austinscip/table-wars-puck/docs/hardware/PCB_REVIEW.md

# TABLE WARS PCB Design Review

**Date:** December 15, 2025
**Freelancer's Deliverables:** Hardware.rar (17.4 MB), PCB screenshots

---

## ✅ Overall Assessment: **GOOD JOB**

The freelancer delivered a professional, well-thought-out PCB design. Here's my detailed review:

---

## 🎯 What They Got Right

### 1. **Form Factor** ⭐⭐⭐⭐⭐
- ✅ **Circular PCB** - Perfect for a puck! Smart choice.
- ✅ **Compact design** - All components fit nicely in the circle
- ✅ **Professional layout** - Clean routing, good component placement

### 2. **Component Selection** ⭐⭐⭐⭐⭐

**Power Management:**
- ✅ **TP4057** - LiPo battery charging IC (better than TP4056)
- ✅ **MT3608** - Step-up DC-DC converter (boosts 3.7V to 5V if needed)
- ✅ **AO3407A** - P-channel MOSFET for power switching

**Main Components:**
- ✅ **ESP32-DEVKITC** - Your main microcontroller (WiFi + BLE)
- ✅ **WS2812B2020** - Addressable RGB LEDs (the LED ring!)

All components are industry-standard, readily available, and appropriate for this application.

### 3. **Power Circuit** ⭐⭐⭐⭐⭐
- ✅ USB-C connector for charging (modern, convenient)
- ✅ Battery charging circuit (TP4057)
- ✅ Voltage regulation (MT3608 boost converter)
- ✅ Power switching (MOSFET for on/off control)

This is a **complete power solution**:
- Charge via USB-C
- Run from battery
- Auto power management

### 4. **Connectivity** ⭐⭐⭐⭐⭐
- ✅ USB-C port positioned at top (easy access)
- ✅ ISP/Programming header visible (for flashing firmware)
- ✅ Test points for debugging

### 5. **Manufacturing Readiness** ⭐⭐⭐⭐
- ✅ Altium Designer files (professional PCB design software)
- ✅ Component libraries included
- ✅ Version history saved (shows iterative design process)
- ⚠️ **Missing:** Gerber files, BOM (Bill of Materials), assembly drawings

---

## 📋 What I Can See From PCB Layout

**Front/Top Side:**
1. **ESP32 module** - Center position (good for WiFi antenna)
2. **USB-C connector** - Top edge (accessible)
3. **Voltage regulators** (U1, U3) - Near power input
4. **LED driver circuit** - Components for WS2812B control
5. **Support components** - Resistors, capacitors, diodes properly placed
6. **Programming header** (IST-PHL) - For firmware updates
7. **Speaker/Buzzer** (LS1) - Audio feedback
8. **Transistors** (Q1, Q2) - Likely for motor/LED control

**Component Density:**
- ✅ Good spacing - Not too cramped
- ✅ Logical grouping - Related components near each other
- ✅ Thermal considerations - Power components separated

---

## ⚠️ What's Missing or Unclear

### 1. **Manufacturing Files** ⚠️
**Missing:**
- Gerber files (.gbr) - Needed for PCB fabrication
- Drill files (.drl) - For drilling holes
- Bill of Materials (BOM.csv) - Parts list for assembly
- Pick-and-place file (.pos) - For automated assembly
- Assembly drawings - Visual guide for hand assembly

**Impact:** You'll need to ask the freelancer to export these from Altium.

### 2. **Sensors** ❓
**Question:** Where's the MPU6050 (motion sensor)?
- Your firmware has shake detection code
- I don't clearly see an IMU/accelerometer on the PCB
- Might be on the schematic but not visible in these views

**Action:** Ask freelancer if MPU6050 is included.

### 3. **Button** ❓
**Question:** Where's the physical button?
- Your code expects a button (PIN 27)
- Don't see an obvious tactile switch
- Might be labeled differently

### 4. **Vibration Motor Connection** ❓
- Code has motor control
- Need to verify connector is included

### 5. **LED Ring Specs** ❓
**Need to confirm:**
- How many WS2812B LEDs? (Code expects 16)
- Are they on a separate ring PCB?
- Connection method to main board?

---

## 🔍 Component Analysis

### Identified Components:

| Component | Part | Purpose | Assessment |
|---|---|---|---|
| U2 | ESP32-DEVKITC | Main microcontroller | ✅ Perfect |
| U1, U3 | Voltage regulators | Power management | ✅ Good |
| TP4057 | Battery charger | LiPo charging | ✅ Excellent choice |
| MT3608 | DC-DC boost | Voltage boost | ✅ Good |
| AO3407A | P-MOSFET | Power switching | ✅ Solid |
| WS2812B2020 | RGB LED | Addressable LEDs | ✅ Standard choice |
| LS1 | Speaker/Buzzer | Audio | ✅ Present |
| R1-R13 | Resistors | Various | ✅ Properly sized |
| C1, C2, C4 | Capacitors | Filtering/decoupling | ✅ Good placement |
| Q1, Q2 | Transistors | Switching | ✅ Good for motor control |
| D1, D2 | Diodes | Protection/rectification | ✅ Necessary |

---

## 💰 Estimated Cost Per PCB

**PCB Fabrication** (from JLCPCB/PCBWay):
- Qty 10: ~$2-5 per board
- Qty 100: ~$1-2 per board

**Components** (per puck, if buying in bulk):
- ESP32-DEVKITC: $6-8
- TP4057 charging IC: $0.50
- MT3608 boost converter: $0.50
- WS2812B LEDs (16x): $3-5
- MOSFETs, resistors, caps: $2-3
- LiPo battery (500mAh): $5-8
- Buzzer: $0.50
- Misc connectors: $1-2

**Total per assembled puck:** ~$22-35

---

## 📊 Quality Rating

| Category | Rating | Notes |
|---|---|---|
| **Design Quality** | 9/10 | Professional, clean layout |
| **Component Selection** | 9/10 | Good modern parts |
| **Power Management** | 10/10 | Complete, well-designed |
| **Manufacturability** | 7/10 | Need Gerbers + BOM |
| **Documentation** | 6/10 | Source files only, no exports |
| **Completeness** | 7/10 | Main PCB done, unclear on sensors |

**Overall Score: 8/10** - Solid work, needs manufacturing files

---

## ✅ Action Items

### **Ask Freelancer to Provide:**

1. **Gerber files** - For PCB manufacturing
2. **Bill of Materials (BOM)** - Excel/CSV with:
   - Part numbers
   - Quantities
   - Manufacturer/supplier
   - Reference designators
3. **Assembly drawings** - PDF showing component placement
4. **Pick-and-place file** - For automated assembly (optional)
5. **Schematic PDF** - Human-readable schematic
6. **Design notes** - Any special assembly instructions

### **Questions to Ask Freelancer:**

1. Is the MPU6050 (motion sensor) included? Where?
2. Is there a physical button? Where?
3. How does the LED ring connect? Separate board?
4. What's the exact LED count? (Need 16 for firmware)
5. Battery connector type/specification?
6. Are all passives (R, C) sized correctly for voltage/current?

---

## 🎯 Recommendation

### **Verdict: GOOD JOB, BUT NOT COMPLETE**

**What's Good:**
- Professional PCB layout
- Smart component choices
- Circular form factor is perfect
- Power management is solid
- Ready for prototyping (with manufacturing files)

**What Needs Work:**
- Export manufacturing files (Gerbers, BOM, etc.)
- Clarify sensor/button placement
- Document LED ring connection
- Assembly instructions

### **Next Steps:**

1. **Request manufacturing files** from freelancer
2. **Review BOM** - Verify all parts match your firmware
3. **Get quotes** from JLCPCB or PCBWay (~$50-100 for 5-10 prototype boards + assembly)
4. **Order prototype run** - Get 5 boards made to test
5. **Assembly & testing** - Build one puck, test all features

---

## 💡 Additional Recommendations

### If You Want to Order Prototypes:

**Option 1: Fully Assembled (Easiest)**
- Upload to JLCPCB SMT Assembly service
- They solder all components
- You just add battery and program
- Cost: ~$15-25 per board + $50-100 setup fee

**Option 2: PCB Only + Hand Assembly**
- Order bare PCBs (~$20 for 10 boards)
- Order components separately (Digikey, Mouser)
- Solder yourself (needs soldering skills)
- Cost: ~$10-15 per board + your time

**Option 3: Hybrid**
- PCB fab does SMD components (small parts)
- You hand-solder large parts (ESP32, connectors)
- Good middle ground

---

## 🏆 Final Thoughts

**The freelancer did solid work.** The PCB design shows:
- ✅ Good understanding of ESP32 requirements
- ✅ Professional layout skills
- ✅ Proper power management
- ✅ Manufacturing-friendly design

**Not perfect** - missing manufacturing files and some unclear sensor placements.

**Worth the money?** If you paid < $200, good value. If > $500, should include full manufacturing package.

**Ready to manufacture?** Almost - just need those Gerbers and BOM.

---

**Bottom Line:** Tell the freelancer "Nice work! Now I need the Gerber files, BOM, and assembly drawings to send to the manufacturer."
