austinscip/table-wars-puck/docs/specs/hardware_requirements.md

# Hardware Requirements Specification

**Project:** [PROJECT_NAME]
**Version:** 1.0
**Date:** [YYYY-MM-DD]
**Status:** [Draft / Under Review / Approved]

## 1. Overview

### 1.1 Purpose
[What does this hardware do? What problem does it solve?]

### 1.2 Scope
[What is included/excluded from this specification]

### 1.3 Definitions and Acronyms
- **MCU:** Microcontroller Unit
- **PCB:** Printed Circuit Board
- **GPIO:** General Purpose Input/Output
- [Add project-specific terms]

## 2. Functional Requirements

### 2.1 Primary Functions

#### FR-001: [Function Name]
**Description:** The system shall [do something]
**Priority:** [Critical / High / Medium / Low]
**Acceptance Criteria:**
- [ ] Criteria 1
- [ ] Criteria 2
- [ ] Criteria 3

#### FR-002: [Function Name]
[Same structure]

### 2.2 User Interface

#### FR-010: Input Controls
- Button 1: [Function]
- Button 2: [Function]
- [Describe all user inputs]

#### FR-011: Output Indicators
- LED 1: [Status indication]
- LED 2: [Status indication]
- Display: [What it shows]
- Audio: [Beep patterns]

### 2.3 Communication

#### FR-020: Wireless Communication
- Protocol: [WiFi / Bluetooth / LoRa / etc.]
- Range: [X meters]
- Data rate: [X kbps]
- Security: [Encryption method]

#### FR-021: Wired Communication
- Interface: [USB / UART / I2C / SPI]
- Purpose: [Programming / Debugging / Data transfer]

## 3. Performance Requirements

### 3.1 Speed and Timing

#### PR-001: Response Time
- User input to feedback: < X ms
- Sensor reading rate: X Hz
- Processing cycle time: < X ms

#### PR-002: Boot Time
- Power-on to ready: < X seconds

### 3.2 Accuracy and Precision

#### PR-010: Sensor Accuracy
- [Sensor 1]: ± X% or ± X units
- [Sensor 2]: ± X% or ± X units

#### PR-011: Measurement Resolution
- [Parameter]: X bits / X units

### 3.3 Capacity and Limits

#### PR-020: Data Storage
- Memory capacity: X MB
- Number of logs: X entries
- Retention time: X days

#### PR-021: Operating Range
- [Parameter]: Min X to Max X [units]

## 4. Power Requirements

### 4.1 Power Supply

#### PW-001: Input Power
- Voltage: X.X V ± X%
- Source: [Battery / USB / Wall adapter]
- Connector: [Type]

#### PW-002: Battery Operation
- Type: [Li-ion / LiPo / Alkaline]
- Capacity: X mAh
- Voltage: X.X V nominal
- Charging: [Method and rate]

### 4.2 Power Consumption

#### PW-010: Operating Modes
- Active mode: X mA @ X.X V
- Sleep mode: X µA @ X.X V
- Deep sleep: X µA @ X.X V

#### PW-011: Battery Life
- Typical usage: X hours/days
- Continuous operation: X hours
- Standby: X days

## 5. Environmental Requirements

### 5.1 Operating Conditions

#### EN-001: Temperature Range
- Operating: X°C to X°C
- Storage: X°C to X°C
- Performance derating: [Describe any temperature effects]

#### EN-002: Humidity
- Operating: X% to X% RH (non-condensing)
- Storage: X% to X% RH

#### EN-003: Other Environmental
- Altitude: [Max X meters]
- Vibration: [Specification]
- Shock: [G-force rating]
- Dust/water: [IP rating if applicable]

### 5.2 Mechanical

#### EN-010: Physical Dimensions
- Maximum: X mm (L) × X mm (W) × X mm (H)
- Weight: X grams (maximum)
- Mounting: [Method and requirements]

#### EN-011: Enclosure
- Material: [ABS / PETG / Aluminum / etc.]
- Color: [Options]
- Finish: [Matte / Glossy / Textured]
- Durability: [Drop test / scratch resistance]

## 6. Interface Requirements

### 6.1 Electrical Interfaces

#### IF-001: [Interface Name]
- Type: [Connector type]
- Signals: [List of signals]
- Voltage levels: [X V logic]
- Current capability: [X mA per pin]
- Protection: [ESD / overcurrent]

### 6.2 Mechanical Interfaces

#### IF-010: Mounting Points
- Type: [Screw holes / clips / adhesive]
- Positions: [Locations]
- Compatibility: [Standards]

## 7. Safety and Compliance

### 7.1 Safety Requirements

#### SF-001: Overcurrent Protection
- Input: Fuse / PTC at X A
- Battery: Protection circuit

#### SF-002: Overvoltage Protection
- Input: TVS diodes / Zener
- Max safe voltage: X V

#### SF-003: Thermal Protection
- Max operating temperature: X°C
- Thermal shutdown: X°C

### 7.2 Regulatory Compliance

#### SF-010: Certifications Required
- [ ] FCC (USA)
- [ ] CE (Europe)
- [ ] RoHS
- [ ] REACH
- [ ] UL/CSA
- [ ] [Others as needed]

## 8. Reliability and Maintenance

### 8.1 Reliability

#### RL-001: MTBF (Mean Time Between Failures)
- Target: X hours
- Conditions: [Operating conditions]

#### RL-002: Component Ratings
- Derating: X% for critical components
- Temperature derating: X% per °C

### 8.2 Maintenance

#### RL-010: User Serviceable Parts
- Battery: [Replaceable by user / technician / non-replaceable]
- [Other parts]

#### RL-011: Firmware Updates
- Method: [OTA / USB / programmer]
- Frequency: [Expected update schedule]

## 9. Quality Requirements

### 9.1 Testing

#### QA-001: Functional Testing
- Power-on self-test
- Communication verification
- Sensor calibration check
- [Other functional tests]

#### QA-002: Environmental Testing
- Temperature cycling: X cycles
- Humidity exposure: X hours
- Vibration: [Profile]

#### QA-003: Production Testing
- Yield target: X%
- Test coverage: X% of functions
- Test time: < X minutes per unit

## 10. Manufacturing Requirements

### 10.1 PCB Specifications

#### MF-001: PCB Details
- Layers: X layers
- Thickness: X.X mm
- Material: [FR4 / Rogers / etc.]
- Surface finish: [HASL / ENIG / etc.]
- Solder mask: [Color]
- Silkscreen: [Color and details]
- Min trace/space: X/X mil
- Min hole size: X mil

### 10.2 Assembly

#### MF-010: Assembly Method
- SMT components: [Auto placement]
- Through-hole: [Manual / wave solder]
- Special processes: [Conformal coating / potting]

#### MF-011: Testing Requirements
- In-circuit test: [Yes / No]
- Functional test: [Procedure]
- Programming: [In-circuit / pre-programmed]

## 11. Documentation Requirements

### 11.1 Required Documentation

- [ ] Schematic (PDF and source)
- [ ] PCB layout (Gerbers and source)
- [ ] BOM with part numbers
- [ ] Assembly drawings
- [ ] Test procedures
- [ ] User manual
- [ ] Quick start guide
- [ ] Firmware source code
- [ ] Design decision log

## 12. Constraints and Assumptions

### 12.1 Constraints
- Budget: $X per unit at quantity Y
- Timeline: [Milestone dates]
- Technology: [Must use existing tools]
- [Other limitations]

### 12.2 Assumptions
- Component availability: [Lead times]
- Manufacturing capability: [Processes available]
- [Other assumptions]

## 13. Verification and Validation

### 13.1 Verification Methods

| Requirement ID | Verification Method | Acceptance Criteria |
|---|---|---|
| FR-001 | Lab test | [Specific test] |
| PR-001 | Measurement | < X ms response |
| PW-010 | Power analyzer | < X mA measured |

### 13.2 Validation Plan

- Prototype testing: [Number of units and test scenarios]
- Field testing: [Beta test plan]
- User feedback: [Method]

## 14. Appendices

### Appendix A: Reference Documents
- [Link to datasheets]
- [Link to application notes]
- [Link to standards]

### Appendix B: Revision History

| Version | Date | Author | Changes |
|---|---|---|---|
| 1.0 | YYYY-MM-DD | [Name] | Initial release |
| 1.1 | YYYY-MM-DD | [Name] | Updated power specs |

---

**Approval Signatures:**

- **Engineering:** ___________ Date: _______
- **Management:** ___________ Date: _______
- **Quality:** ___________ Date: _______

---

*Template by Claude Code*
