austinscip/table-wars-puck/FEATURES_REALITY_CHECK.md

# ESP32 Features - Reality Check for Your Current Hardware

## ✅ WHAT YOU CAN DO RIGHT NOW (No New Hardware)

### 1. ✅ OTA Firmware Updates
**Hardware needed**: NONE - just WiFi
**Cost**: $0
**Status**: ✅ READY TO USE

```cpp
#include "ota_update.h"

void setup() {
    connectWiFi();
    initArduinoOTA();  // Enable OTA updates
}

void loop() {
    handleOTAUpdates();  // Check for updates automatically
}
```

**What this means**:
- Update all 6 pucks wirelessly from your laptop
- Push new games without touching the pucks
- Fix bugs in deployed pucks at the bar

---

### 2. ✅ Dual-Core Processing
**Hardware needed**: NONE - it's in the ESP32 chip
**Cost**: $0
**Status**: ✅ READY TO USE

```cpp
#include "dual_core.h"

void setup() {
    initDualCore();  // Replaces your loop()
}

void loop() {
    // Empty - tasks run on both cores automatically
}
```

**What this means**:
- Game runs on Core 0 (smooth, no lag)
- WiFi runs on Core 1 (doesn't slow down game)
- LEDs update 60 FPS even with heavy WiFi traffic

---

### 3. ✅ Capacitive Touch Surface
**Hardware needed**: Copper tape ($2 for entire roll)
**Cost**: ~$0.30 per puck
**Status**: ✅ READY TO USE

**The ESP32 has 10 built-in touch sensors!** No external hardware needed.

```cpp
#include "capacitive_touch.h"

void setup() {
    initCapacitiveTouch();
    calibrateTouchSensors();  // One-time calibration
}

void loop() {
    readTouchPads();

    if (gestureDetected(GESTURE_TAP)) {
        Serial.println("Tapped!");
    }

    if (gestureDetected(GESTURE_SWIPE_LEFT)) {
        Serial.println("Swiped left!");
    }

    if (gestureDetected(GESTURE_DOUBLE_TAP)) {
        Serial.println("Double tap!");
    }

    // Show which pads are touched on LEDs
    showTouchFeedback();
}
```

**Touch zones available**:
```
T0 = GPIO 4   → Top of puck (tap/double-tap)
T2 = GPIO 2   → Left side (swipe left)
T3 = GPIO 15  → Right side (swipe right)
T4 = GPIO 13  → Bottom (long press)
T5 = GPIO 12  → Corner 1
T6 = GPIO 14  → Corner 2
T7 = GPIO 27  → Corner 3
T8 = GPIO 33  → Corner 4
```

**How to add to your puck**:
1. Cut copper tape into strips
2. Stick to inside of your 3D printed case
3. Solder wire from copper to ESP32 GPIO pins
4. Done! Works through plastic case

---

### 4. ⚠️ Bluetooth Audio (Mixed)
**Hardware needed**: NONE
**Cost**: $0
**Status**: ⚠️ POSSIBLE but HIGH POWER DRAW

```cpp
#include "bluetooth_audio.h"

void setup() {
    // Stream audio TO Bluetooth speaker (instead of buzzer)
    initBluetoothSource("TableWarsPuck");

    // Wait for bar's speaker to connect
    while (!isBluetoothConnected()) {
        delay(100);
    }
}

void gameStart() {
    // Play tones through Bluetooth speaker
    playBluetoothTone(1000, 500);
}
```

**⚠️ WARNING**: Bluetooth uses 100-120 mA
- Your battery: 2000 mAh
- With Bluetooth + WiFi: ~350 mA total
- Battery life: 2000 / 350 = **5.7 hours**
- Without Bluetooth: **8+ hours**

**Recommendation**: Use Bluetooth OR WiFi, not both. Or only use for specific games.

---

## ❌ WHAT YOU CANNOT DO (Need New Hardware)

### 5. ❌ I2S Speaker (Real Audio)
**Hardware needed**: MAX98357A I2S Amplifier ($2.50) + Speaker ($2)
**Cost**: ~$4.50 per puck
**Status**: ❌ NEED TO BUY

**Why you'd want this**:
- Current: Piezo buzzer = annoying beeps
- With I2S: Real audio, voice, music

---

### 6. ❌ SD Card Storage
**Hardware needed**: Micro SD module ($1.50) + SD card ($1)
**Cost**: ~$2.50 per puck
**Status**: ❌ NEED TO BUY

**Why you'd want this**:
- Store 10,000 trivia questions offline
- No WiFi needed for trivia games
- Persistent high scores

---

### 7. ❌ Camera (AR Games)
**Hardware needed**: ESP32-CAM module ($6)
**Cost**: ~$6 per puck
**Status**: ❌ NEED TO BUY

**Why you'd want this**:
- AR games (point at objects)
- QR code scanning
- Victory selfies

---

## 🔊 AUDIO CONFUSION - LET ME EXPLAIN

You currently have a **piezo buzzer**. Here's what each audio option means:

### Option A: Current Buzzer (What You Have)
```cpp
// Your current setup
tone(BUZZER_PIN, 1000, 500);  // Beep at 1000 Hz for 500ms
```

**Sounds like**:
- BEEP BEEP BEEP
- Like a smoke detector
- Can play simple melodies (Mario theme, etc.)
- Very annoying after 5 minutes

**Example**:
```cpp
// Mario coin sound
tone(BUZZER_PIN, 988, 100);
delay(120);
tone(BUZZER_PIN, 1319, 400);
```

Sounds like: "**BEEP BEEP**" (recognizable but not great)

---

### Option B: I2S Speaker (Need $4.50 Hardware)
```cpp
#include "i2s_audio.h"

// Play actual audio files
playWAV("/sounds/mario_coin.wav");  // Real Mario coin sound
playWAV("/sounds/applause.wav");    // Real crowd applause
announceVoice("Player 1 wins!");    // Human voice
```

**Sounds like**:
- Actual recorded audio
- Professional game sounds
- Human voice announcements
- Background music

**Example**:
```cpp
// Game start with voice
announceVoice("ready");     // "Ready" in human voice
delay(1000);
announceCountdown();        // "3... 2... 1... GO!"
startBackgroundMusic("/music/action_theme.wav");

// During game
playWAV("/sounds/score.wav");      // Real "cha-ching!" sound
playWAV("/sounds/explosion.wav");  // Real explosion sound

// Game over
announceVoice("game_over");        // "Game Over" in human voice
playWAV("/sounds/crowd_cheer.wav"); // Real crowd cheering
```

---

### Option C: Bluetooth Audio (No Hardware)
```cpp
#include "bluetooth_audio.h"

// Connect puck to bar's Bluetooth speaker
initBluetoothSource("TableWarsPuck");

// Now ALL sounds play through bar's speakers
playBluetoothTone(1000, 500);
```

**Sounds like**:
- Your buzzer beeps, but through the bar's speaker system
- Still just tones, not real audio
- But MUCH louder

**Use case**: Bar has a Bluetooth speaker system, you want game sounds to play over it

---

### Option D: DAC Analog Audio (Built-in, Free!)
**Wait... I just realized you have ANOTHER option I didn't mention!**

ESP32 has a built-in DAC (Digital-to-Analog Converter) that can generate analog audio.

```cpp
// Use ESP32's built-in DAC to play tones through a simple speaker
// No I2S amplifier needed!

#define SPEAKER_PIN 25  // DAC1 pin

void playDACTone(int frequency, int duration) {
    // Generate analog sine wave
    for (int i = 0; i < duration; i++) {
        int value = 128 + 127 * sin(2 * PI * frequency * i / 44100);
        dacWrite(SPEAKER_PIN, value);
        delayMicroseconds(22);  // 44.1kHz sample rate
    }
}
```

This is better than buzzer beeps but not as good as I2S. It's a **FREE** middle ground!

---

## 🆕 OTHER FEATURES I FORGOT TO MENTION

### 8. ✅ ESP-NOW (Puck-to-Puck Communication)
**Hardware needed**: NONE
**Cost**: $0
**Status**: ✅ READY TO USE

**What this does**: Pucks talk to each other directly (no WiFi router needed!)

```cpp
#include <esp_now.h>

// Send data to another puck instantly
void sendToPuck(int targetPuckId, String message) {
    esp_now_send(targetPuckMAC, message.c_str(), message.length());
}

// Receive from another puck
void onPuckMessage(const uint8_t *mac, const uint8_t *data, int len) {
    String msg = String((char*)data);
    Serial.printf("Puck %d says: %s\n", puckId, msg.c_str());
}
```

**Game ideas**:
- **Puck Wars**: Pucks battle each other, send damage
- **Relay Race**: Pass token from puck to puck
- **Team Games**: Pucks coordinate attacks
- **Sync Challenge**: All pucks must shake at same time

**Benefits**:
- No WiFi needed
- 250m range (way more than Bluetooth)
- Very low power
- Up to 20 pucks can communicate

---

### 9. ✅ Hall Effect Sensor (Magnet Detection)
**Hardware needed**: Small magnet ($0.20)
**Cost**: ~$0.20 per puck
**Status**: ✅ BUILT INTO ESP32!

```cpp
// Detect magnetic field strength
int magneticField = hallRead();

if (magneticField > threshold) {
    Serial.println("Magnet detected!");
}
```

**Game ideas**:
- **Magnetic Treasure Hunt**: Find hidden magnets
- **Docking Station**: Puck knows when it's on charger
- **Secret Unlock**: Wave special magnet to unlock secret game
- **Orientation Detect**: Use Earth's magnetic field as compass

---

### 10. ✅ Temperature Sensor
**Hardware needed**: NONE
**Cost**: $0
**Status**: ✅ BUILT INTO ESP32!

```cpp
extern "C" {
    uint8_t temprature_sens_read();  // Internal temp sensor
}

float temperature = (temprature_sens_read() - 32) / 1.8;
Serial.printf("Temperature: %.1f°C\n", temperature);
```

**Game ideas**:
- **Hot Potato**: Puck gets "hotter" as time runs out
- **Heat Detector**: Find the "hot" zone in the bar
- **Overheat Warning**: Protect the puck from overheating

---

### 11. ✅ Deep Sleep Mode
**Hardware needed**: NONE
**Cost**: $0
**Status**: ✅ READY TO USE

```cpp
// Put puck to sleep when idle
void goToSleep(int seconds) {
    esp_sleep_enable_timer_wakeup(seconds * 1000000ULL);
    esp_deep_sleep_start();
}

// Wake up on button press
void enableButtonWake() {
    esp_sleep_enable_ext0_wakeup(GPIO_NUM_0, 0);  // Button pin
    esp_deep_sleep_start();
}
```

**What this does**:
- Normal power: 250 mA (8 hours battery)
- Deep sleep: 0.01 mA (22,000 hours = 2.5 YEARS!)
- Wake on button press or motion

**Use case**: Puck sleeps when not in use, wakes instantly when picked up

---

## 💰 COST ANALYSIS

### Free Features (Can Do Right Now)
| Feature | Cost | Impact |
|---|---|---|
| OTA Updates | $0 | ⭐⭐⭐⭐⭐ Critical |
| Dual-Core | $0 | ⭐⭐⭐⭐⭐ Huge |
| Capacitive Touch | $0.30 | ⭐⭐⭐⭐ Major |
| ESP-NOW | $0 | ⭐⭐⭐⭐ Major |
| Hall Sensor | $0.20 | ⭐⭐ Nice |
| Temperature | $0 | ⭐ Novelty |
| Deep Sleep | $0 | ⭐⭐⭐ Useful |
| DAC Audio | $0 | ⭐⭐⭐ Good |

**Total: $0.50 per puck**

### Paid Features (Need to Buy)
| Feature | Cost | Impact |
|---|---|---|
| I2S Speaker | $4.50 | ⭐⭐⭐⭐ Major |
| SD Card | $2.50 | ⭐⭐⭐⭐ Major |
| Camera | $6.00 | ⭐⭐⭐⭐ Game changer |

**Total: $13 per puck for all paid features**

---

## 🎯 MY RECOMMENDATION

### Phase 1: FREE UPGRADES (This Weekend!)
1. ✅ **OTA Updates** - Deploy this FIRST
2. ✅ **Dual-Core** - Massive performance boost
3. ✅ **Capacitive Touch** - Add copper tape to case
4. ✅ **ESP-NOW** - Enable multiplayer games

**Cost**: ~$0.50 per puck (just copper tape)
**Time**: 2 hours to integrate
**Result**: Professional-grade puck with multiplayer!

---

### Phase 2: AUDIO UPGRADE ($4.50)
Buy MAX98357A I2S amplifier + small speaker

**Why**:
- Buzzer beeps are annoying
- Voice announcements are awesome
- Background music creates atmosphere

**Example before/after**:
```
BEFORE (buzzer):
Game Start: BEEP BEEP BEEP
Score Point: BEEP!
Game Over: BEEP BEEP BEEEEEEP

AFTER (I2S):
Game Start: "Ready... 3... 2... 1... GO!" (human voice)
Score Point: *cha-ching!* (coin sound)
Game Over: *crowd cheering* (real applause)
```

**Cost**: $4.50 × 6 pucks = **$27 total**

---

### Phase 3: STORAGE UPGRADE ($2.50)
Buy SD card module + 8GB SD card

**Why**:
- 10,000 trivia questions offline
- Works without WiFi
- Downloadable content packs

**Cost**: $2.50 × 6 pucks = **$15 total**

---

### Phase 4: CAMERA (Optional, $6)
Buy ESP32-CAM modules

**Why**:
- AR games are unique
- QR code scavenger hunts
- Victory selfies

**Cost**: $6 × 6 pucks = **$36 total**

---

## 🔊 AUDIO EXAMPLES - BEFORE & AFTER

### Example 1: Trivia Game

**Current (Buzzer)**:
```cpp
void triviaGame() {
    Serial.println("Question: What is 2+2?");

    // Wait for answer...

    if (correct) {
        tone(BUZZER_PIN, 2000, 200);  // BEEP!
        Serial.println("Correct!");
    } else {
        tone(BUZZER_PIN, 500, 500);   // BEEEEP
        Serial.println("Wrong!");
    }
}
```

Sounds like: "**BEEP!**" or "**BEEEEP**" (annoying)

---

**With I2S Speaker** ($4.50):
```cpp
void triviaGame() {
    announceVoice("question_1");  // "What is 2 plus 2?"

    // Wait for answer...

    if (correct) {
        playWAV("/sounds/correct.wav");     // Ding-ding-ding!
        announceVoice("correct");            // "Correct!"
        playWAV("/sounds/applause.wav");    // Crowd cheering
    } else {
        playWAV("/sounds/wrong.wav");       // Buzzer sound
        announceVoice("wrong_answer");       // "Oops, wrong answer!"
    }
}
```

Sounds like: **Real game show!**

---

### Example 2: Shake Duel

**Current (Buzzer)**:
```cpp
void shakeDuel() {
    tone(BUZZER_PIN, 1000, 100);  // Start beep
    delay(3000);
    tone(BUZZER_PIN, 1500, 100);  // GO beep

    // Shake detection...

    tone(BUZZER_PIN, 2000, 1000);  // Winner beep
}
```

Sounds like: "**BEEP ... BEEP ... BEEEEEP**" (boring)

---

**With I2S Speaker**:
```cpp
void shakeDuel() {
    announceVoice("ready");               // "Ready..."
    delay(1000);
    announceCountdown();                  // "3... 2... 1... GO!"

    startBackgroundMusic("/music/tension.wav");  // Suspenseful music

    // Shake detection...

    stopBackgroundMusic();
    playWAV("/sounds/victory_fanfare.wav");     // Ta-da!
    announceVoice("winner");                     // "We have a winner!"
}
```

Sounds like: **Professional game!**

---

### Example 3: Puck Racer (TV Game)

**Current (Buzzer)**:
```cpp
void puckRacer() {
    tone(BUZZER_PIN, 800, 100);   // Start
    // Racing...
    tone(BUZZER_PIN, 1200, 50);   // Nitro boost
    // Racing...
    tone(BUZZER_PIN, 300, 500);   // Crash
}
```

Sounds like: "**BEEP ... BEEP! ... BEEEEEP**" (lame)

---

**With I2S Speaker**:
```cpp
void puckRacer() {
    announceVoice("ready_set_go");              // "Ready, set, GO!"
    startBackgroundMusic("/music/racing.wav");   // Racing music

    // Racing...
    if (nitroBoost) {
        playWAV("/sounds/nitro.wav");          // WHOOOOSH!
    }

    // Racing...
    if (crashed) {
        playWAV("/sounds/car_crash.wav");      // CRASH sound
        announceVoice("crashed");               // "Oops, you crashed!"
    } else {
        playWAV("/sounds/finish_line.wav");    // Checkered flag
        announceVoice("you_win");               // "You win!"
    }
}
```

Sounds like: **Real racing game!**

---

## 🎮 CONCRETE NEXT STEPS

### This Weekend (Free)
```bash
# 1. Integrate OTA updates
cp src/ota_update.h into your main.cpp
# Add to setup(): initArduinoOTA()
# Add to loop(): handleOTAUpdates()

# 2. Enable dual-core
cp src/dual_core.h into your project
# Replace loop() with initDualCore()

# 3. Add capacitive touch
cp src/capacitive_touch.h into your project
# Stick copper tape to case
# Wire to GPIO 4, 2, 15, 13
```

### Next Week (Order Parts - $27)
```bash
# Order on Amazon:
# - 6× MAX98357A I2S Amplifier ($15)
# - 6× Small 4Ω speakers ($12)
```

### Week After (Install I2S)
```bash
# Wire speakers to ESP32
# Load audio files to SPIFFS
# Enjoy professional audio!
```

---

## ❓ FAQ

**Q: Can I just use Bluetooth instead of buying I2S speaker?**
A: Yes, BUT:
- Bluetooth only plays tones (not real audio)
- Bluetooth drains battery fast (100 mA)
- Requires external Bluetooth speaker

I2S is way better for $4.50.

---

**Q: Do I need ALL the features?**
A: No! Priority:
1. OTA Updates (critical)
2. Dual-Core (free performance)
3. I2S Audio (makes it professional)
4. Everything else is optional

---

**Q: What about the camera?**
A: Cool but expensive ($6) and high power (150 mA). Try audio first.

---

**Q: ESP-NOW sounds awesome, how do I use it?**
A: I'll create examples! It's perfect for multiplayer games where pucks need to communicate.

---

## 🚀 BOTTOM LINE

**With current hardware + $0.50 copper tape**:
- ✅ OTA updates
- ✅ Dual-core performance
- ✅ Touch-sensitive surface
- ✅ Puck-to-puck communication
- ✅ Deep sleep battery savings

**Add $27 for I2S audio**:
- ✅ Professional voice announcements
- ✅ Real game sounds
- ✅ Background music
- ✅ Makes your puck 10× better

**Total to make it AMAZING: $27.50 for all 6 pucks**

That's a no-brainer! 🎯
