austinscip/table-wars-puck/.claude.md

# [PROJECT_NAME] - Hardware Project

## Project Overview
**Brief description:** [What this hardware does - 1-2 sentences]
**Type:** [IoT Device / Sensor / Controller / etc.]
**Status:** [Planning / Design / Prototype / Manufacturing / Testing / Production]
**Start Date:** [YYYY-MM-DD]

## Current Status
**Phase:** [Current development phase]
**Version:** [Current version number]
**Last Updated:** [YYYY-MM-DD]

## Quick Facts
- **Target Quantity:** [Number of units to produce]
- **Estimated Cost per Unit:** $[X-Y]
- **Timeline:** [Expected completion date]
- **Key Components:** [List 3-5 main components]

## File Inventory

### ✅ Hardware Design Files
- **CAD Tool:** [Altium / KiCad / Eagle / Other]
- **Schematic:** [Status and location]
- **PCB Layout:** [Status and location]
- **Board Layers:** [Number of layers]
- **Board Size:** [Dimensions]
- **Latest Revision:** [vX.Y - Date]

### ✅ Manufacturing Files
- **Gerbers:** [Status - location]
- **Drill Files:** [Status - location]
- **BOM:** [Status - location]
- **Pick-and-Place (CPL):** [Status - location]
- **Assembly Drawings:** [Status - location]

### ✅ Mechanical Files
- **3D Models:** [Status - location]
- **STL Files:** [Status - location]
- **STEP Files:** [Status - location]
- **Technical Drawings:** [Status - location]

### ✅ Firmware/Software
- **Platform:** [Arduino / ESP32 / STM32 / etc.]
- **Language:** [C++ / MicroPython / etc.]
- **Repository:** [Link or location]
- **Version:** [Current version]

### ❌ Missing or In-Progress
- [List what still needs to be created or completed]

## Key Components

### Main ICs
- **MCU:** [Part number] - $[price] - [Notes]
- **Sensors:** [Part number] - $[price] - [Notes]
- **Power Management:** [Part number] - $[price] - [Notes]
- **Communication:** [Part number] - $[price] - [Notes]

### Power System
- **Input Voltage:** [X-Y V]
- **Battery:** [Type, capacity, voltage]
- **Charging:** [Method - IC used]
- **Regulators:** [List voltage regulators]
- **Expected Runtime:** [Hours on battery]

### Connectivity
- **WiFi:** [Yes/No - chip used]
- **Bluetooth:** [Yes/No - chip used]
- **Cellular:** [Yes/No - chip used]
- **Wired:** [USB / Ethernet / etc.]
- **Other:** [LoRa / ZigBee / etc.]

### I/O
- **Sensors:** [List all sensors]
- **Actuators:** [Motors, LEDs, speakers, etc.]
- **User Interface:** [Buttons, display, etc.]
- **Indicators:** [LEDs, etc.]

## Cost Breakdown

### Per-Unit Component Cost
- **PCB Fabrication:** $[X]
- **Components:** $[X]
- **Assembly:** $[X]
- **Enclosure:** $[X]
- **Testing:** $[X]
- **Packaging:** $[X]
- **Total per unit:** $[X]

### Development Costs (One-Time)
- **Design Time:** $[X] or [Y hours]
- **Prototypes:** $[X]
- **Tooling:** $[X]
- **Certifications:** $[X] (FCC/CE/etc.)
- **Total NRE:** $[X]

### Production Estimates
- **Prototype (1-5 units):** $[X] per unit
- **Small Batch (10-50):** $[X] per unit
- **Medium Run (100-500):** $[X] per unit
- **Production (1000+):** $[X] per unit

## Manufacturing Strategy

### Target Manufacturers
- **PCB Assembly:** [JLCPCB / PCBWay / MacroFab / etc.]
- **3D Printing:** [Same as PCB or separate]
- **Final Assembly:** [Manual / Automated]

### Critical Requirements
- [ ] [List any special manufacturing requirements]
- [ ] [SMT, Through-hole, Mixed assembly]
- [ ] [Conformal coating, special finish, etc.]

### Lead Times
- **PCB Fabrication:** [X days]
- **Assembly:** [Y days]
- **Shipping:** [Z days]
- **Total:** [X+Y+Z days]

## Technical Specifications

### Electrical
- **Operating Voltage:** [X-Y V]
- **Current Draw:**
  - Idle: [X mA]
  - Active: [Y mA]
  - Peak: [Z mA]
- **Power Consumption:** [X W max]

### Environmental
- **Operating Temperature:** [X to Y °C]
- **Storage Temperature:** [X to Y °C]
- **Humidity:** [X-Y% RH]
- **IP Rating:** [IP XX or N/A]

### Mechanical
- **Dimensions:** [L x W x H mm]
- **Weight:** [X grams]
- **Mounting:** [How it mounts/installs]
- **Connectors:** [List external connectors]

### Compliance
- [ ] **FCC:** [Required / Not Required / Status]
- [ ] **CE:** [Required / Not Required / Status]
- [ ] **RoHS:** [Yes / No]
- [ ] **REACH:** [Yes / No]
- [ ] **UL/CSA:** [Required / Not Required / Status]

## Design Decisions

### [Date] - [Decision Title]
**Context:** [Why this decision was needed]
**Options Considered:**
1. [Option 1 - pros/cons]
2. [Option 2 - pros/cons]
**Decision:** [What was chosen]
**Rationale:** [Why this option was best]
**Impact:** [Cost / schedule / performance impact]

### [Date] - Component Selection: [Component Name]
**Chosen:** [Part number]
**Alternatives Considered:** [List]
**Reason:** [Why chosen]
**Source:** [Where to buy]
**Cost Impact:** $[X] per unit

## Known Issues

### Critical (Blocking Progress)
- [Issue description - what's blocked]

### Major (Impacts Functionality)
- [Issue description - workaround if any]

### Minor (Nice to Fix)
- [Issue description]

### Resolved
- [Issue] - Fixed by [solution] on [date]

## Testing & Validation

### Test Procedures Created
- [ ] Power-on test
- [ ] Functional test
- [ ] Stress test
- [ ] Environmental test
- [ ] Compliance test

### Test Results
- **Prototype v1.0:** [Pass/Fail - Date - Notes]
- **Prototype v1.1:** [Pass/Fail - Date - Notes]

### Issues Found in Testing
- [Issue] - [Severity] - [Status]

## External Dependencies

### Must Source Separately
1. **[Component Name]**
   - Reason: [Not available from PCB assembly house]
   - Source: [Adafruit / Digi-Key / etc.]
   - Cost: $[X]
   - Lead Time: [Y days]

### Manual Assembly Required
1. [Component or step that must be done by hand]
2. [Why it can't be automated]

## Certifications & Compliance

### Required Certifications
- [ ] **FCC Part 15:** [Status]
- [ ] **CE:** [Status]
- [ ] **Other:** [List]

### Testing Labs
- [Lab name] - [Contact] - [Cost estimate]

### Timeline
- [Certification name]: [Expected completion date]

## Suppliers & Vendors

### PCB Manufacturing
- **Primary:** [Company name] - [Contact] - [Website]
- **Backup:** [Company name]

### Components
- **Primary:** [Digi-Key / Mouser / etc.]
- **Backup:** [LCSC / Arrow / etc.]

### Mechanical
- **3D Printing:** [Company / In-house]
- **Injection Molding:** [If applicable]
- **Machining:** [If applicable]

### Assembly/Testing
- **Who:** [In-house / Contract manufacturer]
- **Where:** [Location]

## Project Timeline

### Milestones
- [x] **[Date]** - Concept & requirements defined
- [ ] **[Date]** - Schematic complete
- [ ] **[Date]** - PCB layout complete
- [ ] **[Date]** - Prototype ordered
- [ ] **[Date]** - Prototype received & tested
- [ ] **[Date]** - Revisions complete
- [ ] **[Date]** - Pilot run ordered
- [ ] **[Date]** - Production run

## Lessons Learned

### What Went Well
- [Thing that worked well]

### What Could Be Improved
- [Thing to do differently next time]

### Design Changes for v2.0
- [Improvement idea]

## Session Log

### [Date] - [Session Title]
**What was done:**
- [Bullet list of accomplishments]

**Decisions made:**
- [Key decisions]

**Next steps:**
- [ ] [What to do next]

**Time spent:** [X hours]
**Status after session:** [Current state]

---

## Quick Reference

**Main Files:**
- Schematic: `hardware/[tool]/[project].sch`
- PCB: `hardware/[tool]/[project].pcb`
- BOM: `hardware/manufacturing/bom/[project]_bom.csv`
- Gerbers: `hardware/manufacturing/gerbers/`

**Key Documents:**
- README.md - Project overview
- CHANGELOG.md - Version history
- docs/specs/ - Technical specifications
- docs/decisions/ - Design decisions

**Commands:**
```bash
# Zip gerbers for manufacturer
cd hardware/manufacturing && zip gerbers.zip gerbers/*

# Run tests (add your commands)
cd firmware && platformio test

# Generate BOM (add your commands)
# ...
```

---

**Last Updated:** [YYYY-MM-DD] by [Your Name]
**Project Status:** [Planning / Active Development / Testing / Production]
**Next Review:** [YYYY-MM-DD]
