austinscip/table-wars-puck/cad/FINAL_SUMMARY.md

# ESP32 Gaming Puck - CAD Design Final Summary

## 🎮 What You Have

### **Files Created:**
1. ✅ **forerunner_top_shell_v2.scad** → Top dome with Forerunner aesthetics
2. ✅ **forerunner_bottom_shell_v2.scad** → Bottom shell with component mounts
3. ✅ **button_glyph_cap_v2.scad** → Center button with Forerunner glyph
4. ✅ **motor_sock_tpu.scad** → TPU vibration motor holder
5. ✅ **bumper_ring_tpu.scad** → TPU equator bumper ring
6. ✅ **assembled_view.scad** → Full assembly visualization

### **Exported STL Files (Ready to Print):**
- forerunner_top_shell_v2.stl (554 KB)
- forerunner_bottom_shell_v2.stl (455 KB)
- button_glyph_cap_v2.stl (64 KB)
- motor_sock_tpu.stl (126 KB)
- bumper_ring_tpu.stl (255 KB)

---

## ⚠️ CRITICAL DISCOVERY - MUST READ

### **Your Spec vs My Design:**

**Sid's Technical Doc Describes:**
- Custom 88-90mm circular PCB design
- ESP32 chip mounted directly on PCB (not DevKitC module)
- MPU6050 at EXACT CENTER for symmetric motion
- Professional PCB fab + assembly
- **Cost: ~$900-1600 for 10 units**

**My CAD Files Are For:**
- Hand-wired assembly using ESP32-DevKitC module
- Separate breakout boards (MPU6050, TP4057, MT3608)
- MPU6050 offset 25mm from center (asymmetric motion)
- Component mounts for off-the-shelf modules
- **Cost: ~$260-490 for 10 units**

### **These Are DIFFERENT Approaches!**

Read `SPEC_COMPARISON.md` for full details.

---

## 🔴 Design Issues Found

### **1. Battery Clearance (FIXED in next version)**
- Battery tray extends 1mm beyond internal cavity
- **Fix:** Lower tray by 3mm → Done in V3

### **2. MPU6050 Placement (DESIGN DECISION NEEDED)**
- **Spec requires:** MPU6050 at exact center
- **My design:** MPU6050 at 25mm offset
- **Impact:** Asymmetric motion detection (tilt right ≠ tilt left)

**Options:**
- A) Accept offset placement (OK for shake/tap games)
- B) Custom PCB with centered MPU ($900-1600 total)
- C) Redesign enclosure for centered MPU (loses button tower)

### **3. Assembly Type Mismatch**
- **Spec assumes:** Custom PCB
- **My design:** DevKitC modules + wiring

**You need to choose:**
- Path A: Custom PCB (Sid's spec, more $$, better performance)
- Path B: DevKitC assembly (my design, cheaper, faster)

---

## 📐 Current Design Specifications

### **Enclosure:**
- Outer diameter: 95mm
- Total height: 40mm
- Wall thickness: 3.5mm (bottom), 3.0mm (top)
- Material: PETG (structure), TPU 95A (bumper/motor sock)

### **Features:**
✅ 6× M3 screw bosses with brass insert pockets
✅ O-ring groove for IP54 splash resistance
✅ USB-C cutout for TP4057 charging
✅ LED ring mounts (4× standoffs)
✅ Center button tower with 12mm hole
✅ Battery tray (62×37×9mm)
✅ Motor pocket (12.5mm)
✅ Buzzer recess (23mm)
✅ Thermal & sound vents
✅ Wire routing channels
✅ Decorative Forerunner elements

### **Aesthetics V2:**
✅ 3× prominent energy rings on dome
✅ 16× radial light diffusion channels
✅ 6× Forerunner hexagons (top + bottom)
✅ Hexagonal screw recesses
✅ Decorative button recess
✅ Base ridges
✅ Smooth dome curves

---

## 🎯 What to Do Next

### **DECISION 1: PCB or DevKitC?**

**Custom PCB (Sid's Spec):**
- ✅ MPU centered (best gameplay)
- ✅ Professional, compact
- ❌ $900-1600 total
- ❌ 3-4 weeks
- ⚠️ Need to adapt my enclosures for PCB

**DevKitC Assembly (My Design):**
- ✅ Cheaper ($260-490 total)
- ✅ Faster (1-2 weeks)
- ✅ My enclosures ready to use
- ❌ MPU offset (not ideal for precise motion)
- ❌ More wiring

**Answer:** Which path do you want?

---

### **DECISION 2: MPU Centering Priority?**

**For your 37 games, is MPU centering critical?**

**If games need PRECISE tilt:**
- Example: "Tilt 30° left to aim laser"
- → Need custom PCB with centered MPU

**If games just detect SHAKE/TAP:**
- Example: "Shake detected, trigger explosion"
- → Offset MPU is FINE

**Answer:** What type of motion do your games use?

---

### **DECISION 3: Assembly Approach?**

**Option A - DevKitC + My Enclosures:**
1. Use my V2 STL files
2. 3D print enclosures
3. Buy ESP32-DevKitC + breakout boards
4. Hire Sid for assembly only
5. **Total: ~$500, 2 weeks**

**Option B - Custom PCB + Adapted Enclosures:**
1. Pay Sid for PCB design ($300-500)
2. PCB fab + assembly ($500-800)
3. I redesign enclosures for PCB (1 hour)
4. 3D print adapted enclosures
5. **Total: ~$1200, 4 weeks**

**Answer:** Which option?

---

## 📂 File Locations

**All files in:**
```
~/table-wars-puck/cad/
```

**Key files:**
- `SPEC_COMPARISON.md` - PCB vs DevKitC analysis
- `CLEARANCE_CHECK.md` - Technical clearance issues
- `BUTTON_LOCATION.txt` - Button placement explanation
- `V2_IMPROVEMENTS.md` - Aesthetic upgrades
- `assembled_view.scad` - Full assembly visualization

---

## 🖼️ Viewing Your Design

### **Assembly View:**
OpenSCAD should be showing `assembled_view.scad` now.

**In OpenSCAD:**
- Preview (F5) - Fast preview
- Render (F6) - Full render (takes 30 sec)
- Rotate - Left-click + drag
- Zoom - Scroll wheel

**To see exploded view:**
1. Open `assembled_view.scad` in text editor
2. Change line 8: `exploded_view = true;`
3. Re-preview in OpenSCAD

**To see cross-section:**
1. Comment out `full_assembly();` (line at end)
2. Uncomment `cross_section_view();`
3. Re-preview

---

## ✅ What's Ready to Use

**If you choose DevKitC path:**
- ✅ All 5 STL files ready to print
- ✅ All component mounts sized correctly
- ⚠️ Need to fix battery clearance (V3 update)
- ⚠️ MPU is offset (acceptable for most games)

**If you choose Custom PCB path:**
- ⚠️ Need to redesign enclosures for PCB mounting
- ⚠️ Remove component-specific mounts
- ⚠️ Add 88-90mm PCB mounting ring
- ⏱️ 1 hour redesign time

---

## 💰 Cost Estimate

### **DevKitC Path (My Design):**
```
Components (10 units):     $400-500
3D Printing:               $200-400
Assembly (Sid):            $200-400
--------------------------------
TOTAL:                     $800-1300
```

### **Custom PCB Path (Sid's Spec):**
```
PCB Design:                $300-500
PCB Fab + Assembly:        $500-800
3D Printing:               $200-400
--------------------------------
TOTAL:                     $1000-1700
```

---

## 🚀 Next Actions

**ANSWER THESE 3 QUESTIONS:**

1. **Budget:** OK with $800-1300 (DevKitC) or $1000-1700 (PCB)?

2. **Motion sensing:** Do games need precise tilt or just shake detection?

3. **Timeline:** Need in 2 weeks or 4 weeks OK?

**Then I will:**
- Fix battery clearance issue
- Optimize for your chosen path
- Create final production-ready STL files
- Give you assembly instructions

---

## 📞 Contact Sid

**Update your Freelancer message:**

> Hi Sid,
>
> I've reviewed your technical spec and have enclosure CAD files ready.
>
> **Question:** Your spec describes a custom circular PCB. I have two paths:
>
> **Path A - Custom PCB (your spec):**
> - You design 88-90mm circular PCB
> - PCB fab + assembly + 3D printed enclosures
> - Quote for 10 units?
>
> **Path B - DevKitC assembly (simpler/cheaper):**
> - Use ESP32-DevKitC module + breakout boards
> - You assemble electronics only
> - I have enclosure STLs ready
> - Quote for 10 units?
>
> Which do you recommend for 10 prototype units?
>
> Also confirm:
> - Load-sharing solution (Option B vs C)
> - Timeline estimate
> - 30-day warranty
>
> Thanks!

---

**WAITING FOR YOUR 3 ANSWERS TO PROCEED!**
