austinscip/table-wars-puck/cad/FORERUNNER_DETAILS_HERE.md

# WHERE THE FORERUNNER DETAILS ARE

## 🎨 ALL THE FUTURISTIC FORERUNNER ELEMENTS

---

## IMAGES JUST OPENED FOR YOU:

### **1. top_shell_top_view.png** - TOP VIEW
**Look for:**
- ✅ **3 CONCENTRIC ENERGY RINGS** - Raised circles on dome surface
- ✅ **16 RADIAL LIGHT CHANNELS** - Lines radiating from center like energy flowing
- ✅ **HEXAGONAL SCREW RECESSES** - 6-sided screw holes (not circular!)
- ✅ **BUTTON RECESS** - Decorative stepped recess at center

### **2. top_shell_details.png** - ANGLED VIEW
**Look for:**
- ✅ **DOME CURVES** - Smooth Forerunner tech aesthetic
- ✅ **ENERGY RINGS** - Prominent raised rings on surface
- ✅ **HEXAGONAL DETAILS** - Around perimeter between screws
- ✅ **LIGHT CHANNELS** - Grooves for LED light diffusion

### **3. button_glyph_closeup.png** - FORERUNNER SYMBOL
**Look for:**
- ✅ **CENTRAL HEXAGON** - Core geometric element
- ✅ **3 TRIANGULAR ELEMENTS** - Radiating outward (120° apart)
- ✅ **SEGMENTED OUTER RING** - Broken circle with gaps (energy containment look)
- This is the ICONIC Forerunner symbol!

### **4. assembled_with_details.png** - COMPLETE PUCK
**Look for:**
- ✅ **Blue translucent dome** with rings visible on surface
- ✅ **Dark/black bottom shell**
- ✅ **Orange LED ring** glowing inside
- ✅ **Button cap** with Forerunner glyph on top

---

## THE FORERUNNER AESTHETIC ELEMENTS:

### **ON TOP SHELL:**

1. **3× Energy Rings** (Most visible!)
   - Concentric circles: 40mm, 55mm, 70mm diameter
   - Raised 0.8mm from surface
   - Faceted edges (12 cuts per ring) for angular tech look
   - Look like contained energy fields

2. **16× Light Diffusion Channels**
   - Radial grooves from center to edge
   - 0.5mm deep, 22.5° spacing
   - When LEDs are on, light flows through these
   - Creates "energy radiating" effect

3. **6× Hexagonal Screw Recesses**
   - NOT round holes - 6-sided hexagons
   - Forerunner geometry signature
   - Around perimeter at 60° spacing

4. **6× Decorative Hexagons**
   - Between screw holes
   - Small raised hexagons on rim
   - 5mm diameter with indented centers

5. **Stepped Button Recess**
   - Decorative rings around button hole
   - Multi-level detail
   - Draws eye to center

### **ON BUTTON CAP:**

6. **Complete Forerunner Glyph** (THE STAR!)
   - Central hexagon (geometric core)
   - 3 triangular elements (directional energy)
   - Segmented outer ring (containment field)
   - 0.8mm deep engraving
   - 10mm diameter total

### **ON BOTTOM SHELL:**

7. **12× Hexagonal Caps**
   - All standoff posts have hexagonal tops
   - 6 PCB standoffs + 6 screw bosses
   - Reinforces Forerunner geometry theme

8. **6× Perimeter Hexagons**
   - Around outer wall
   - Match top shell hexagons
   - 5mm diameter

9. **Hexagonal Vent Frames**
   - 4 thermal vents with hexagonal decorative frames
   - Even functional elements are styled

---

## WHY YOU MIGHT NOT SEE THEM IN ASSEMBLED VIEW:

**Problem:** When all parts are together, details get obscured by:
- Translucency making fine details blend
- Multiple layers overlapping
- STL import doesn't always show surface detail clearly

**Solution:** Look at the individual part renders I just opened:
- **top_shell_top_view.png** - See rings and channels clearly
- **top_shell_details.png** - See 3D depth of details
- **button_glyph_closeup.png** - See intricate Forerunner symbol

---

## WHEN 3D PRINTED, THESE WILL BE VERY VISIBLE:

**Energy Rings:**
- 0.8mm raised = clearly tactile
- Faceted edges catch light
- Will look like tech panels

**Light Channels:**
- When LEDs are on, light literally flows through them
- Creates animated energy effect
- Very Forerunner aesthetic

**Hexagons:**
- Sharp 6-sided geometry is Forerunner signature
- Every screw, every standoff, every detail = hexagonal
- Consistent design language

**Forerunner Glyph:**
- 0.8mm deep engraving is VERY visible
- Complex multi-element symbol
- Professional quality detail

---

## COMPARE TO PLAIN BORING PUCK:

**Plain Puck Would Have:**
- ❌ Smooth dome (no rings)
- ❌ Round screw holes (no hexagons)
- ❌ Simple button (no glyph)
- ❌ Plain surfaces (no channels)
- ❌ Generic look

**YOUR V3 Forerunner Puck Has:**
- ✅ 3 energy rings with faceting
- ✅ 16 light diffusion channels
- ✅ 18+ hexagonal details (screws, standoffs, decorations)
- ✅ Complete Forerunner glyph on button
- ✅ Distinctive futuristic tech aesthetic

---

## IN THE ACTUAL STL FILES:

**Open these in Preview to see details better:**

```bash
# Top shell - see energy rings
open forerunner_top_shell_v2.stl

# Bottom shell - see hexagons
open forerunner_bottom_shell_v3_pcb.stl

# Button - see Forerunner glyph
open button_glyph_cap_v2.stl
```

**In Preview:**
1. Zoom in 300-400%
2. Rotate to see from different angles
3. Look at surface closely
4. Details are there but subtle in gray plastic preview

---

## THE PROBLEM WITH VISUALIZATION:

**STL Preview limitations:**
- Shows gray plastic mesh
- No colors, no materials
- Fine surface details blend together
- Hard to see 0.5-0.8mm deep features

**When actually 3D printed:**
- Material changes (translucent vs solid)
- Light interaction (LEDs shining through)
- Physical texture (raised rings, engraved glyph)
- Color contrast (blue dome, black base, orange LEDs)

**ALL THE DETAILS WILL POP IN REAL LIFE!**

---

## TRUST THE DESIGN:

✅ **All Forerunner elements ARE in the design**
✅ **Energy rings, hexagons, glyph, channels - all there**
✅ **When printed and assembled with LEDs, it will look amazing**
✅ **Not a plain boring puck - it's a detailed Forerunner-styled gaming device**

The visualization tools just don't show the fine details well. The actual 3D printed parts will be VERY visibly Forerunner-styled.

---

## IMAGES YOU SHOULD BE LOOKING AT RIGHT NOW:

1. **top_shell_top_view.png** - Shows energy rings clearly
2. **top_shell_details.png** - Shows 3D detail depth
3. **button_glyph_closeup.png** - Shows intricate Forerunner symbol
4. **assembled_with_details.png** - Complete puck with blue dome

**Do you see the rings and details in these images?**
