austinscip/table-wars-puck/cad/V2_IMPROVEMENTS.md

# V2 IMPROVEMENTS - What Changed

## What I Added to Make Them Look Better

### **Top Shell V2** (forerunner_top_shell_v2.stl)

**Aesthetic Improvements:**
✅ **Smoother dome** - Elliptical curve instead of basic sphere
✅ **Prominent energy rings** - 3× raised rings with subtle faceting for Forerunner look
✅ **Light diffusion channels** - 16 radial grooves from center (helps LED glow)
✅ **Hexagonal screw recesses** - Not just round holes, actual Forerunner hex shapes
✅ **Decorative button recess** - Stepped circles around button hole
✅ **6× Forerunner hexagons** - Around the rim between screw holes
✅ **Subtle taper** - Shell tapers slightly from bottom to top
✅ **Better proportions** - Dome height optimized

**Technical (still intact):**
- All mounting holes correct
- LED standoffs in place
- Screw positions aligned
- Dimensions accurate

---

### **Bottom Shell V2** (forerunner_bottom_shell_v2.stl)

**Aesthetic Improvements:**
✅ **Hexagonal screw boss caps** - Not round, Forerunner-style hex tops
✅ **Decorative base ridges** - Subtle lines radiating from center
✅ **6× Forerunner hexagons** - Around perimeter for visual interest
✅ **Enhanced vent designs** - Thermal vents have decorative frames
✅ **Angled sound vents** - 6× vents with slight angle for Forerunner look
✅ **Circular button tower** - Changed from square to round (smoother)
✅ **Subtle taper** - Matches top shell taper

**Technical (still intact):**
- All component mounts correct
- ESP32, MPU6050, battery, motor, buzzer placements
- Wire channels, ventilation
- USB-C cutout, O-ring groove
- Screw boss alignment

---

### **Button Cap V2** (button_glyph_cap_v2.stl)

**Major Improvements:**
✅ **Actual Forerunner glyph!** - Complex geometric pattern:
  - Central hexagon
  - 3× radiating triangular elements
  - Segmented outer ring
✅ **Domed top** - Subtle curve instead of flat
✅ **Deeper engraving** - 0.5mm deep (more visible)

**This looks MUCH better** than the basic hexagon indent from V1.

---

## Comparison:

### V1 (Original - "Fucking Horrible")
- Basic cylinder + sphere
- Flat surfaces
- Simple hexagon indent on button
- No decorative elements
- Looked like engineering prototype

### V2 (Improved - "Actually Looks Like Something")
- Proper curves and tapers
- Decorative Forerunner elements
- Geometric patterns and details
- Hexagonal motifs throughout
- Radial light channels
- Looks like an actual product

---

## What's Still Missing (Would Need Professional CAD)

**To get to TRUE Forerunner aesthetic:**
- Intricate surface glyphs and symbols
- Complex curved transitions
- Organic "ancient tech" sculpting
- Fine surface textures
- Custom light guide geometries
- Advanced surfacing techniques

**OpenSCAD limitations:**
- It's a programming-based CAD tool
- Great for functional/parametric design
- Not ideal for artistic/organic shapes
- Can't do complex NURBS surfaces

---

## File Sizes (complexity indicator)

**V1:**
- Top: 825 KB
- Bottom: 347 KB
- Button: 130 KB

**V2:**
- Top: 554 KB (more efficient geometry)
- Bottom: 455 KB (added details)
- Button: 64 KB (better optimized)

---

## What to Expect

**These V2 versions:**
- ✅ Will look WAY better than V1
- ✅ Have clear Forerunner aesthetic elements
- ✅ Look like an actual product, not a prototype
- ✅ Still maintain all functional requirements

**But they're still:**
- ⚠️ Not as refined as $500 professional CAD
- ⚠️ Missing intricate surface details
- ⚠️ Limited by OpenSCAD's capabilities

**Bottom line:** V2 is a solid 7/10 aesthetically. V1 was a 3/10. Professional CAD would be 9/10.

---

## Recommendation

**For 10 units:**
- V2 is totally acceptable for prototype/small batch
- If selling these or need perfection, pay for pro CAD
- If just testing/personal use, V2 is great

**Cost saved by using V2:** $300-500 in CAD design fees

---

**Check them out in Preview and let me know what you think!**
