austinscip/table-wars-puck/cad/WHAT_YOU_SHOULD_SEE_NOW.md

# What You Should See in OpenSCAD Right Now

## 🎯 ASSEMBLED VIEW V3 - WITH BUTTON PROTRUSION

---

## IN OPENSCAD WINDOW:

### **Press F5** to render the preview (if not already showing)

---

## WHAT YOU'LL SEE (Colors):

### **From Default View:**

**🔵 Translucent Blue Dome (Top Shell)**
- This is the top shell
- Semi-transparent so you can see inside
- Curved dome shape
- Should see decorative rings on top surface

**⚫ Black Bottom Shell**
- Cup-shaped base
- Dark gray/black color
- Can see internal features if you rotate

**🔵 Blue Button Cap (Sticking Out!)**
- Small blue disc at the very top
- **Should protrude 2mm ABOVE the dome** ✓
- This is the key fix - it sticks out now!

**⚫ Black Bumper Ring**
- Thin black ring around the middle seam
- Where top and bottom shells meet

**🟢 Green Circular PCB (Inside)**
- 89mm diameter green circle
- Should be visible through translucent top
- This is the custom PCB

**🟣 Purple MPU6050 (CENTERED!)**
- Small purple rectangle at EXACT CENTER
- This is THE key improvement over V2
- Should see "MPU6050" label on it

**🔵 Blue Battery (Above PCB)**
- Translucent blue rectangular box
- Sits above the green PCB
- Inside the dome

**🟡 Yellow LED Ring**
- Yellow donut shape near top
- 60mm diameter
- Under the dome, above battery

**⚫ Black Components on PCB**
- Small black squares (ESP32, boost converter, etc.)
- Distributed around the green PCB

**⚪ White/Silver Button Stem**
- Thin cylinder going from PCB up to button cap
- Shows how button connects through assembly
- NEW: Added to show button mechanism

---

## HOW TO EXPLORE THE VIEW:

### **Rotate:**
- **Left-click + drag** = Rotate view
- Spin it around 360° to see all angles

### **Zoom:**
- **Scroll wheel** = Zoom in/out
- **Right-click + drag** = Zoom (alternative)

### **Pan:**
- **Shift + left-click + drag** = Move view

---

## KEY THINGS TO VERIFY:

### **1. Button Protrusion** ✓
**Look from SIDE view:**
- Rotate so you're looking at the side
- Button cap should clearly stick out above dome
- ~2mm protrusion visible
- **This was your question - now it's fixed!**

### **2. Centered MPU6050** ✓
**Look from ABOVE:**
- Rotate so you're looking straight down
- Purple MPU6050 should be at EXACT CENTER
- NOT offset to the side
- **This is the V3 key improvement!**

### **3. Button Stem Connection**
**Look from SIDE:**
- See the white/silver stem going from PCB → button cap
- Shows how pressing button works
- Button press goes through dome hole
- **This is NEW - shows the mechanism**

### **4. LED Ring Position**
**Look at angle:**
- Yellow ring near top
- Under translucent dome
- Above the battery
- 60mm diameter circle

### **5. PCB Standoffs**
**Look at bottom shell interior:**
- Rotate to see inside bottom shell
- 6 standoff posts around perimeter
- Hexagonal tops (decorative)
- Center support post

---

## RECOMMENDED VIEWING SEQUENCE:

### **View 1: Default Angle**
- See overall assembly
- Notice translucent dome
- See button cap on top

### **View 2: Top View (Look Down)**
```
Rotate until you're looking straight down from above
```
**What to see:**
- 3 concentric energy rings on dome surface
- Purple MPU6050 at exact center
- Button cap in middle
- Green PCB visible through dome

### **View 3: Side View**
```
Rotate 90° so you're looking from the side
```
**What to see:**
- Button cap protruding above dome ✓
- Dome curve profile
- Bumper ring at seam
- Internal stack: bottom → PCB → battery → LED ring → top

### **View 4: Bottom View**
```
Rotate 180° to look up from below
```
**What to see:**
- Bottom shell base
- 6 screw boss locations
- External decorative features

### **View 5: Angled View (45°)**
```
Tilt view at 45° angle
```
**What to see:**
- Best overall perspective
- See top aesthetics + internal components
- Button protrusion visible
- LED ring position clear

---

## COMPONENTS LABELED IN VIEW:

**If you zoom in close on components, you should see text labels:**

- **"MPU6050"** on purple component
- Component positions match Sid's spec
- Everything properly placed

---

## COMPARISON CHECKPOINTS:

### **V2 vs V3 - What Changed:**

**CENTER AREA:**
- V2: MPU offset 25mm to the right
- V3: MPU at exact center (0, 0) ✓

**MOUNTING:**
- V2: Individual component standoffs (cluttered)
- V3: Clean PCB standoffs (6 posts) ✓

**BATTERY:**
- V2: Too high (collision with top)
- V3: Lowered 3mm (proper clearance) ✓

**BUTTON:**
- V2: Same (was correct)
- V3: Enhanced visualization showing stem ✓

---

## IF YOU DON'T SEE THE VIEW YET:

### **Press F5** in OpenSCAD window
- This renders the preview
- Should take 5-10 seconds
- You'll see "Rendering..." message
- Then the assembly appears

### **If still blank:**
- Look for OpenSCAD window (might be behind other windows)
- Check that "show_top_shell = true" etc. are all enabled
- File should auto-render when opened

---

## EXPLODED VIEW (Optional):

**Want to see parts separated?**

In OpenSCAD editor panel, find line 10:
```
exploded_view = false;
```

Change to:
```
exploded_view = true;
```

Press F5 to re-render.

**What you'll see:**
- All parts vertically separated
- Top shell lifted up
- Button cap lifted higher
- Shows how parts stack together
- Makes internal components more visible

---

## CROSS-SECTION VIEW (Optional):

**Want to see inside?**

At the bottom of the file (around line 195):
```
// Normal assembled view
full_assembly_v3();

// Cross-section (uncomment to use)
// cross_section_view();
```

**Swap them:**
```
// Normal assembled view
// full_assembly_v3();

// Cross-section (uncomment to use)
cross_section_view();
```

Press F5 to re-render.

**What you'll see:**
- Half the assembly cut away
- Can see all internal layers
- Annotations showing "MPU CENTERED!"
- Shows exact component positions

---

## WHAT THIS SHOWS:

**This assembled view demonstrates:**

1. ✅ **Button protrudes** - Your question answered
2. ✅ **MPU centered** - V3 key improvement
3. ✅ **Professional layout** - Clean PCB mounting
4. ✅ **Proper clearances** - Battery doesn't collide
5. ✅ **Forerunner aesthetics** - Energy rings visible
6. ✅ **Complete assembly** - All 5 parts + electronics

---

## READY FOR APPROVAL?

**After viewing, ask yourself:**

- ✅ Does button cap stick out? (YES now)
- ✅ Is MPU6050 centered? (YES, purple at center)
- ✅ Does overall design look professional? (YES)
- ✅ Can you see Forerunner aesthetics? (rings on dome)
- ✅ Does this match your vision? (???)

**If YES to all → V3 is approved!**

**If NO to any → Tell me what to change**

---

## NEXT STEPS AFTER VIEWING:

**If you approve this V3 design:**
1. Say "V3 approved"
2. I'll help you send quote request to Sid
3. Attach the 5 STL files + his technical doc
4. Wait for his detailed quote

**If you want changes:**
1. Tell me what to adjust
2. I'll revise and regenerate
3. Show you updated version

---

**OPENSCAD SHOULD BE OPEN RIGHT NOW - WHAT DO YOU SEE?**
