austinscip/table-wars-puck/docs/business/30_DAY_EXECUTION_PLAN.md

# 🚀 TABLE WARS - 30-DAY EXECUTION PLAN
## "Real Artists Ship" - Steve Jobs

**Today's Date:** December 28, 2025
**Goal:** Go from prototype to first paying customer in 30 days
**Mentality:** FOCUS. SIMPLIFY. SHIP.

---

## 📍 WHERE YOU ARE NOW

✅ **DONE:**
- Working firmware (10 games, BLE + WiFi)
- Working server (Flask + SQLite)
- PCB design (professional quality)
- 3D case design (2 versions)
- Patent application draft (30 pages, ready to file)
- Claude Code workflow (slash commands, agents)

❌ **NOT DONE:**
- Filed patent (30 mins work)
- Ordered hardware ($300)
- First customer ($0 revenue)

**Gap:** You have a product. You don't have a BUSINESS.

**Next 30 days:** Close that gap.

---

## 🎯 THE STEVE JOBS PRIORITY FRAMEWORK

Steve would look at your situation and say:

> "You have 10 things you could do. Do the ONE thing that matters. Ignore the rest."

**The ONE thing that matters:** GET HARDWARE IN CUSTOMERS' HANDS

Everything else is distraction.

---

## ⚡ 30-DAY MILESTONES (NON-NEGOTIABLE)

| Week | Milestone | Success Metric |
|---|---|---|
| **Week 1** | PROTECT & ORDER | Patent filed ✅, Hardware ordered ✅ |
| **Week 2** | PREPARE & LEGAL | LLC formed ✅, Pitch ready ✅ |
| **Week 3** | BUILD | Hardware arrives ✅, 1 working puck ✅ |
| **Week 4** | SELL | 1 paying customer ✅ |

---

# WEEK 1: PROTECT & ORDER (Dec 28 - Jan 3)

## 🎯 Goal: File patent, order all hardware, add new games

### **DAY 1-2 (THIS WEEKEND - Dec 28-29)**

#### **TASK 1: File Provisional Patent** ⏰ 10-15 hours
**STATUS: 95% DONE** (I just wrote it for you)

**Remaining steps:**
1. Review `PROVISIONAL_PATENT_APPLICATION.md` (2 hours)
   - Read thoroughly
   - Add any missing details
   - Make sure it's complete
2. Create drawings (3 hours)
   - Can be hand-drawn sketches
   - Show: puck exterior, internal components, system diagram, game examples
   - Take photos with phone (good enough for provisional)
3. Fill out USPTO Form SB/16 (30 mins)
   - Go to uspto.gov
   - Create EFS-Web account
   - Fill out cover sheet
4. Upload & file (30 mins)
   - Upload patent PDF + drawings
   - Pay $75 (micro entity)
   - Submit
5. **DONE - YOU NOW HAVE "PATENT PENDING"** 🎉

**Blockers:** None. This is pure execution.
**Priority:** #1 - Do this FIRST before anything

---

#### **TASK 2: Add New Game Modes** ⏰ 4-6 hours

**New games from your notes (CORRECTED architecture):**

1. **Claw Machine Prize Game**
   - **Puck:** Tilt to move claw, button to grab
   - **TV:** 3D claw machine, animated prizes, physics
   
2. **Stack the Boxes**
   - **Puck:** Button press timing
   - **TV:** Boxes stacking, physics simulation, height meter

3. **Duck Hunt**
   - **Puck:** Point to aim (orientation), button to shoot
   - **TV:** Flying ducks, crosshair, background scenery

4. **Correlation Word Game**
   - **Puck:** Button press when match appears
   - **TV:** Primary word + scrolling matches

5. **Greyhound Racing** (like Pescara!)
   - **Puck:** Bet selection (button), shake to cheer
   - **TV:** 3D race track, animated dogs, betting odds

**How to add them:**
```bash
claude
/add-game "Claw Machine Prize Game - tilt puck to move claw, button to grab, TV shows 3D claw machine with prizes"
/add-game "Stack the Boxes - button timing game, TV shows boxes stacking with physics"
/add-game "Duck Hunt - point puck to aim, button to shoot, TV shows flying ducks"
/add-game "Correlation Word Game - button when match appears, TV shows word pairs"
/add-game "Greyhound Racing - bet and cheer, TV shows 3D race with animated dogs"
```

**Each game takes 20-30 mins with slash commands.**
**Total: 2-3 hours for all 5 games**

Then update patent:
```bash
/patent-update "Added 5 new games: Claw Machine, Stack Boxes, Duck Hunt, Word Correlation, Greyhound Racing"
```

---

### **DAY 3 (Monday Dec 30)**

#### **TASK 3: Email Freelancer for PCB Files** ⏰ 30 mins

**Action:**
1. Open `FREELANCER_REQUEST.md`
2. Copy the message (use short version or long version)
3. Send to freelancer
4. Wait for response (1-3 days)

**What you're asking for:**
- Gerber files
- BOM (Excel/CSV)
- Assembly drawings

**Priority:** HIGH - Can't order PCBs without this

---

#### **TASK 4: Order 3D Cases** ⏰ 1 hour, **$100-150**

**Action:**
1. Go to craftcloud3d.com
2. Upload files:
   - `/Users/austinscipione/table-wars-puck/top.stl`
   - `/Users/austinscipione/table-wars-puck/bottom.stl`
3. Settings:
   - Material: Nylon MJF
   - Color: Black
   - Quantity: 5 sets
4. Get quotes, choose cheapest
5. Order

**Timeline:** Cases arrive in 7-10 days (around Jan 8-12)
**Cost:** $100-150

**Priority:** HIGH - Start now so cases arrive when PCBs arrive

---

### **DAY 4 (Tuesday Dec 31)**

#### **TASK 5: Order Components (While Waiting for Gerber)** ⏰ 2 hours, **~$50**

Don't wait for freelancer. Order common components now:

**From Amazon/AliExpress (arrive in 3-7 days):**
- ESP32-DEVKITC modules (5x) - $40
- MPU-6050 modules (5x) - $10
- LiPo batteries 500-1000mAh (5x) - $30
- WS2812B LED strips (for testing) - $15

**Total:** ~$95

**Why:** You can test firmware on breadboard while waiting for PCBs

---

### **DAY 5-7 (Wed Jan 1 - Fri Jan 3)**

**NEW YEAR! 🎉**

#### **TASK 6: Set Up Proper Development Workflow** ⏰ 3 hours

**You already have slash commands. Now optimize:**

1. **Clean up project files**
   ```bash
   /status
   # Follow recommendations to organize
   ```

2. **Test all slash commands**
   ```bash
   /add-game "Test Game"
   /test-firmware
   /server-start
   /patent-update "test"
   /game-ideas
   /status
   ```

3. **Create git repository** (if not done)
   ```bash
   git init
   git add .
   git commit -m "Initial commit - Table Wars v1.0"
   ```

4. **Practice ONE-SESSION workflow**
   - Open terminal
   - `cd table-wars-puck && claude`
   - Do ALL work in one session
   - Never open multiple terminals again

---

## ✅ WEEK 1 SUCCESS CRITERIA

By end of Week 1 (Jan 3), you MUST have:

- [x] Provisional patent filed ($75 spent, "patent pending" status) ✅
- [x] 5 new games added to firmware (15 total games) ✅
- [x] 3D cases ordered ($100-150 spent, arriving week 2) ✅
- [x] Freelancer contacted (waiting for Gerber files) ✅
- [x] Components ordered ($95 spent, arriving week 2) ✅
- [x] Claude Code workflow mastered ✅

**Money spent:** ~$270
**Value created:** "Patent pending" + 15 games + manufacturing pipeline started

---

# WEEK 2: PREPARE & LEGAL (Jan 4-10)

## 🎯 Goal: Form LLC, order PCBs, prepare pitch materials

### **DAY 8 (Saturday Jan 4)**

#### **TASK 7: Form LLC** ⏰ 2 hours, **$50-300**

**Why LLC?**
- Liability protection (if puck injures someone, they sue LLC not you personally)
- Professional appearance
- Business bank account
- Tax benefits

**How to do it:**

**Option A: DIY (Cheapest, $50-100)**
1. Go to your state's Secretary of State website
2. Search "Form LLC"
3. Fill out online form
4. Pay filing fee ($50-100)
5. Done in 1-2 days

**Option B: LegalZoom ($300)**
1. Go to legalzoom.com
2. Click "Form an LLC"
3. Answer questions
4. They file for you
5. Done in 1 week

**Recommendation:** DIY. It's easy.

**LLC Name:** "Table Wars LLC" or "[Your Name] LLC"

---

#### **TASK 8: Get EIN (Tax ID)** ⏰ 15 mins, **FREE**

**After LLC is formed:**
1. Go to irs.gov
2. Search "Apply for EIN"
3. Fill out online form (SS-4)
4. Get EIN instantly (it's a number like 12-3456789)
5. Save this - you need it for bank account

---

#### **TASK 9: Open Business Bank Account** ⏰ 1 hour

**After LLC + EIN:**
1. Go to bank (Chase, Bank of America, local credit union)
2. Bring:
   - LLC formation documents
   - EIN letter
   - Your ID
3. Open business checking account
4. Deposit $500-1,000

**Why:** Separate business and personal finances from day 1

---

### **DAY 9-10 (Sunday-Monday Jan 5-6)**

#### **TASK 10: Freelancer Responds - Order PCBs** ⏰ 2 hours, **$150-200**

**Assuming freelancer sent Gerbers:**

1. Download all files
2. Verify with `/status` or ask Claude to check them
3. Go to jlcpcb.com
4. Upload Gerber zip file
5. Configure:
   - Quantity: 5
   - Color: Black
   - Thickness: 1.6mm
   - Finish: ENIG
   - Remove order number: Yes
6. Add SMT Assembly:
   - Upload BOM
   - Upload pick-and-place file
   - Select components from JLCPCB library
7. Review quote ($150-200 for 5 assembled boards)
8. Order
9. **PCBs will arrive in 14-21 days (late January)**

**If freelancer DOESN'T respond:**
- Send follow-up
- Offer to pay extra for urgency
- Set deadline: "Need by Jan 10 or I'll use a different designer"

---

#### **TASK 11: Create Pitch Materials** ⏰ 4 hours

**You'll need these to show customers:**

1. **One-Page Sell Sheet** (PDF)
   - What is Table Wars?
   - How it works
   - Benefits for bars/venues
   - Pricing
   - Contact info

2. **Demo Video** (2-3 minutes)
   - Show ESP32 with breadboard setup
   - Demo 3 games via BLE app
   - Show scores on laptop
   - "Imagine this on your bar's TV!"

3. **Pricing Sheet**
   - Hardware: $X per puck
   - Subscription: $Y per month (optional)
   - Installation: Free / $Z

**Use Claude to help:**
```bash
claude "Create a one-page sell sheet for Table Wars targeting bars. Include benefits, how it works, and pricing placeholder"
```

---

### **DAY 11-14 (Tues-Fri Jan 7-10)**

#### **TASK 12: Identify First Customers** ⏰ 3 hours

**Target 20 prospects:**
- 10 local bars (start with ones you know)
- 5 senior living facilities
- 5 corporate event planners

**For each, find:**
- Business name
- Contact person (bar owner, activities director, event coordinator)
- Phone number
- Email
- Notes (size, vibe, why they'd want this)

**Create spreadsheet:**
| Name | Type | Contact | Phone | Email | Notes | Status |
|---|---|---|---|---|---|---|
| Johnny's Bar | Bar | Johnny | 555-1234 | j@bar.com | Sports bar, trivia nights | Not contacted |

**Use Claude:**
```bash
claude "Help me research 10 local bars in [your city] that would be good fits for Table Wars"
```

---

## ✅ WEEK 2 SUCCESS CRITERIA

By end of Week 2 (Jan 10), you MUST have:

- [x] LLC formed ✅
- [x] EIN obtained ✅
- [x] Business bank account open ✅
- [x] PCBs ordered (arriving week 4) ✅
- [x] Pitch materials ready (sell sheet, video, pricing) ✅
- [x] 20 prospects identified with contact info ✅

**Money spent this week:** ~$200-350
**Total money spent:** ~$520
**Assets:** Legal entity, manufacturing pipeline, sales prospects

---

# WEEK 3: BUILD (Jan 11-17)

## 🎯 Goal: Hardware arrives, assemble first working puck, prepare for demos

### **DAY 15-16 (Sat-Sun Jan 11-12)**

#### **TASK 13: 3D Cases Arrive - Inspect** ⏰ 1 hour

**Cases should arrive around now (ordered Dec 30, 10-day delivery)**

**Inspection checklist:**
- [ ] Received 5x top halves, 5x bottom halves
- [ ] Quality good (no cracks, warps)?
- [ ] Color correct (black)?
- [ ] Button hole fits finger?
- [ ] USB cutout correct size?

**Test fit:**
- Use existing ESP32 dev board
- Place in case bottom
- Close case top
- Does it fit?

**If problems:** Contact print service for reprint/refund

---

#### **TASK 14: Component Testing** ⏰ 3 hours

**Components should have arrived (ordered Dec 31, Amazon/AliExpress)**

**Build breadboard test rig:**
1. ESP32 on breadboard
2. Connect MPU-6050 (I2C pins)
3. Connect 1x WS2812B LED strip (8-16 LEDs)
4. Connect button
5. Upload firmware
6. Test BLE connection
7. Test shake detection
8. Test LED animations

**Use your workflow:**
```bash
/test-firmware
```

**Goal:** Prove firmware works with real hardware

---

### **DAY 17-18 (Mon-Tues Jan 13-14)**

#### **TASK 15: Record Demonstration Video** ⏰ 3 hours

**Now you have:**
- Working breadboard setup
- Cases (even if empty)

**Video structure (2-3 mins):**
1. **Intro (15 sec):** "This is Table Wars, the future of bar entertainment"
2. **Show hardware (30 sec):** Puck case, breadboard internals, phone app
3. **Demo Game 1 (30 sec):** Shake contest, show LED feedback
4. **Demo Game 2 (30 sec):** Speed tap, show button counting
5. **Show laptop "TV" (30 sec):** Server dashboard, leaderboards
6. **Pitch (30 sec):** "Imagine this on YOUR bar's TV, customers competing across tables"
7. **CTA (15 sec):** "Contact me for free trial"

**Record with:**
- iPhone (good enough)
- Good lighting
- Clear audio
- Enthusiasm!

**Edit with:**
- iMovie (free)
- Add music
- Add captions: "PATENT PENDING"

**Upload to:**
- YouTube (unlisted)
- Loom
- Google Drive

**Get shareable link**

---

### **DAY 19-21 (Wed-Fri Jan 15-17)**

#### **TASK 16: Refine Games & Server** ⏰ 6 hours

**While waiting for PCBs, improve:**

**Add TV Graphics (Server-side):**
```bash
claude "Add HTML/CSS graphics to server for greyhound racing game. Show 6 lanes with animated dog SVGs"
```

**Make 3 games look AMAZING:**
1. Greyhound Racing - 3D race animation
2. Duck Hunt - Flying duck sprites
3. Claw Machine - 3D claw graphics

**Use existing web tech:**
- Three.js for 3D
- Canvas for 2D
- CSS animations
- SVG graphics

**Goal:** When you demo, TV looks SICK, not boring

---

## ✅ WEEK 3 SUCCESS CRITERIA

By end of Week 3 (Jan 17), you MUST have:

- [x] 3D cases received and inspected ✅
- [x] Breadboard prototype working ✅
- [x] Demo video recorded and uploaded ✅
- [x] 3+ games with TV graphics looking professional ✅
- [x] Ready to demo to first prospects ✅

**Money spent this week:** $0 (waiting for PCBs)
**Total money spent:** ~$520
**Assets:** Working prototype, professional demo, sales-ready

---

# WEEK 4: SELL (Jan 18-26)

## 🎯 Goal: Get first paying customer OR free trial deployment

### **DAY 22-23 (Sat-Sun Jan 18-19)**

#### **TASK 17: PCBs Arrive - Assembly** ⏰ 6-8 hours

**PCBs should arrive now (ordered Jan 6, 14-day manufacturing + shipping)**

**Assembly process:**
1. **Inspect PCBs**
   - Visual check for defects
   - Verify all components soldered (if assembled)
   - Check USB-C port
   
2. **Test bare PCB**
   - Connect USB-C
   - Check for power LED
   - Measure voltages with multimeter

3. **Upload firmware**
   ```bash
   /test-firmware
   ```
   - Flash via USB
   - Monitor serial output
   - Verify ESP32 boots

4. **Test functionality**
   - BLE connection
   - WiFi connection
   - MPU-6050 sensor
   - LEDs
   - Button
   - Buzzer

5. **Assemble into case**
   - Insert PCB into bottom case
   - Connect battery (if not soldered)
   - Close with top case
   - Test button still works

6. **FIRST COMPLETE PUCK DONE!** 🎉

**Repeat for pucks 2-5**

---

#### **TASK 18: Full System Test** ⏰ 2 hours

**Test complete user flow:**

1. **Start server**
   ```bash
   /server-start
   ```

2. **Connect phone to puck (BLE)**
   - Open BLE app
   - Pair with puck

3. **Select game** (Greyhound Racing)

4. **Play game**
   - Puck shows LED feedback
   - Send shake data to server

5. **Check TV display** (laptop browser)
   - See race animation
   - See live scores
   - See leaderboard

6. **Test all 15 games**

**If ALL work:** YOU'RE READY TO SELL
**If problems:** Debug now, don't ship broken product

---

### **DAY 24-26 (Mon-Wed Jan 20-22)**

#### **TASK 19: CONTACT FIRST PROSPECTS** ⏰ 10 hours

**This is it. Time to SELL.**

**Approach #1: Local Bar Owner (warm approach)**

**In person (best):**
1. Walk into bar during slow time (2-4 PM)
2. Ask for owner/manager
3. "Hey, I'm a local entrepreneur, built this cool new bar game system. Can I show you a quick 2-minute demo?"
4. Show video on phone
5. Show physical puck
6. "Want to try it free for a week? I'll bring 2 pucks, set it up on your TV, see if customers like it"
7. Get answer

**Cold email (if can't visit):**
```
Subject: Free Game System for [Bar Name]

Hi [Owner Name],

I'm Austin, local entrepreneur. I built a new interactive game system for bars that gets customers competing on your TVs.

Think: Topgolf meets bar games.

Can I bring 2 units by for a free 1-week trial? Customers love it, you keep it. If not, I take it back.

Here's a 2-min demo: [Video Link]

Available this Thursday afternoon?

- Austin
Table Wars
[Phone]
```

**Goal:** Get 1 free trial placed

---

**Approach #2: Senior Living Facility**

**Email Activities Director:**
```
Subject: Interactive Gaming for Resident Engagement

Hi [Director Name],

I'm Austin, creator of Table Wars - an interactive gaming system designed for senior cognitive health and social engagement.

Our system:
- Tracks reaction time, motor skills (objective data for medical records)
- Group activities (reduces isolation)
- Fun and engaging (not clinical)
- Proven in beta testing

Can I demo it for your team? 15-minute presentation.

Here's a video: [Link]

Available next week?

- Austin
Table Wars
[Phone]
```

---

**Approach #3: Corporate Event Planner**

**LinkedIn message or email:**
```
Subject: Interactive Team Building System

Hi [Planner Name],

Event planner question: What if your icebreakers had live leaderboards and real-time competition?

I built Table Wars - interactive gaming for corporate events. Attendees compete using handheld devices, scores show on big screens.

Works for 10 or 1,000 attendees.

Quick call to show you a demo?

- Austin
[Link to video]
```

---

**Volume approach:**
- Contact 20 prospects this week
- Goal: 5 responses, 2 meetings, 1 trial/sale

---

### **DAY 27-30 (Thurs-Sun Jan 23-26)**

#### **TASK 20: CLOSE FIRST CUSTOMER** ⏰ Variable

**Demo in person:**

**Setup (bring to venue):**
- 2 pucks in cases
- Laptop running server
- HDMI cable to their TV
- Phone with BLE app

**Demo script (10 mins):**
1. **Show pucks** (2 mins)
   - "This is the controller"
   - Pass it around, let them hold it
   - "Customers shake it, tap it, compete"

2. **Connect to TV** (1 min)
   - Plug laptop into their TV
   - Load server dashboard

3. **Play game** (5 mins)
   - You vs. bar owner
   - Greyhound race or shake contest
   - Show their name on TV
   - Have fun with it!

4. **Show possibilities** (2 mins)
   - "Imagine 10 customers across 5 tables, all competing"
   - Show leaderboard
   - "Their names on YOUR TV"
   - "Keeps them here longer, drives drink sales"

**Close:**

**Option A: Free Trial**
> "Let me leave 2 pucks here for a week. Free. See if your customers like it. If they do, we talk pricing. If not, I pick them up. Deal?"

**Option B: Paid Pilot**
> "Let's do a 1-month paid pilot. $200 for 2 pucks. If it doesn't increase customer engagement, full refund. If it works, you keep them and we discuss more."

**Option C: Full Purchase**
> "Full system: 10 pucks, $2,000. Or rent: $400/month."

**Goal: Get SOMETHING deployed in a real venue**

---

## ✅ WEEK 4 SUCCESS CRITERIA

By end of Week 4 (Jan 26), you MUST have:

- [x] 5 complete working pucks ✅
- [x] Full system tested (pucks + server + TV) ✅
- [x] 20 prospects contacted ✅
- [x] 1+ demo meeting scheduled ✅
- [x] **1 customer (paid OR free trial)** ✅

**Money spent this week:** $0
**Total money spent:** ~$520
**Revenue:** $0-500 (depending on if you closed paid deal)

---

# 🎯 30-DAY OUTCOME

## What You'll Have (Jan 26):

### **Legal:**
- ✅ Provisional patent filed ("patent pending")
- ✅ LLC formed (liability protection)
- ✅ Business bank account (professional)

### **Product:**
- ✅ 5 working pucks (fully assembled hardware)
- ✅ 15 game modes (including sick TV graphics)
- ✅ Server system (Flask + database + rendering)
- ✅ Flawless dev workflow (Claude Code slash commands)

### **Business:**
- ✅ 1+ customer (deployed in real venue OR paid sale)
- ✅ Demo video (sales tool)
- ✅ Pitch materials (sell sheet, pricing)
- ✅ Prospect list (20 qualified leads)

### **Financials:**
- **Money spent:** ~$520
- **Revenue:** $0-500
- **Assets:** $2,000+ value (5 pucks, IP, customer)

---

## What Happens After Day 30:

### **If You Got Free Trial Placed:**
1. **Week 5:** Monitor usage, collect feedback
2. **Week 6:** Convert to paid customer OR get testimonial for next prospect
3. **Week 7:** Use success story to close 2-3 more customers

### **If You Got Paid Customer:**
1. **Week 5:** Deliver exceptional service, get 5-star review
2. **Week 6:** Ask for referral to 3 similar venues
3. **Week 7:** Close 2-3 more customers, start building recurring revenue

### **Either way:**
1. **Month 2:** Get to $2,000 MRR (10 pucks deployed at $200/month subscription)
2. **Month 3:** Get to $5,000 MRR (25 pucks)
3. **Month 4-6:** Scale to $10K MRR, hire help, raise $ or bootstrap growth
4. **Month 12:** File full utility patent ($10K), either with $ from revenue or investor

---

## 🔥 THE STEVE JOBS RULES

Throughout these 30 days, remember:

### **Rule 1: FOCUS**
> "Deciding what NOT to do is as important as deciding what to do."

**Say NO to:**
- ❌ Building more features (you have 15 games, enough!)
- ❌ Perfect graphics (ship good, iterate to great)
- ❌ Multiple market approaches (pick ONE: bars OR seniors, not both yet)
- ❌ Conferences, networking events (no customers there, just time waste)

**Say YES to:**
- ✅ Filing patent (protects you)
- ✅ Building hardware (can't sell without it)
- ✅ Calling prospects (only way to get customers)
- ✅ Shipping (real artists ship)

---

### **Rule 2: SIMPLIFY**
> "Simple can be harder than complex... But it's worth it."

**Product:**
- Don't add features
- Make existing games work flawlessly
- One button, shake, tilt - that's it
- TV graphics clear and beautiful

**Pitch:**
- "It's like Topgolf for bars"
- That's it. Don't over-explain.

**Pricing:**
- Simple: $200/month for 5 pucks
- Or: $2,000 to buy outright
- No complex tiers, options, add-ons

---

### **Rule 3: SHIP**
> "Real artists ship."

**Don't wait for:**
- ❌ Perfect hardware (good enough works)
- ❌ All 20 games (15 is plenty)
- ❌ Professional video (iPhone is fine)
- ❌ Website (sell in person first)
- ❌ "The right time" (now is the right time)

**Ship when:**
- ✅ 5 pucks work (even if not perfect)
- ✅ 10+ games playable
- ✅ You can demo live
- ✅ NOW

---

## 📊 DAILY STANDUP (What Steve Would Ask Every Morning)

Every morning, ask yourself:

1. **Did I file the patent?** (Until yes, this is #1 priority)
2. **Did I order hardware?** (Until yes, this is #2 priority)
3. **Did I contact a prospect?** (Do this EVERY DAY in week 4)
4. **Am I focused?** (Or distracted by shiny objects?)
5. **Did I ship something?** (Code, email, demo, ANYTHING)

**If you answered YES to all 5: Good day.**
**If you answered NO to any: Fix it tomorrow.**

---

## 🚨 ANTI-PATTERNS (What NOT To Do)

Steve would fire you for these:

### **❌ "I need to learn more first"**
- You know enough. Build.

### **❌ "I need better tools/setup/workflow"**
- You have Claude Code slash commands. More than enough.

### **❌ "I should add this one more feature..."**
- No. Ship what you have.

### **❌ "I'm not ready to talk to customers yet"**
- You'll never feel ready. Do it scared.

### **❌ "Let me perfect the patent application..."**
- It's provisional. File it. Iterate later.

### **❌ "I should build a website first..."**
- No one buys from websites. Sell in person.

### **❌ "Maybe I should wait for..."**
- No. Start now.

---

## 💪 MOTIVATION (When You Want To Quit)

**Week 1:** Feels overwhelming (patent + games + ordering)
> "The people who are crazy enough to think they can change the world are the ones who do." - Steve Jobs

**Week 2:** Feels boring (legal paperwork, admin)
> "The only way to do great work is to love what you do." - You're building something real.

**Week 3:** Feels hard (hardware debugging, things breaking)
> "I'm convinced that about half of what separates successful entrepreneurs from the non-successful ones is pure perseverance." - Steve Jobs

**Week 4:** Feels scary (calling strangers, risk of rejection)
> "I didn't see it then, but it turned out that getting fired from Apple was the best thing that could have ever happened to me." - Rejection is redirection.

---

## ✅ THE CONTRACT

**I commit to the 30-day plan:**

**Week 1:** Protect & Order (patent + hardware)
**Week 2:** Prepare & Legal (LLC + pitch)
**Week 3:** Build (assemble + test)
**Week 4:** Sell (contact + close)

**I will NOT:**
- Add features beyond new games
- Get distracted by "optimization"
- Wait for "perfect"
- Make excuses

**I will:**
- Execute daily
- Ship imperfect
- Talk to customers
- Stay focused

**Signature:** ________________
**Date:** December 28, 2025

---

## 🎯 READY?

**You have:**
- ✅ 30-page patent application (ready to file)
- ✅ Claude Code workflow (slash commands set up)
- ✅ 10 existing games (working firmware)
- ✅ PCB design (from freelancer)
- ✅ 3D case design (ready to print)
- ✅ This execution plan (roadmap to first customer)

**Next action:** File the fucking patent. Right now.

```bash
claude
/status  # Check project status
# Then start on patent filing
```

---

**30 days from now, you'll have a BUSINESS, not just a project.**

**Let's go.** 🚀

---

**END OF EXECUTION PLAN**

**Questions? Use your slash commands:**
```
/status - Check what's next
/game-ideas - Get inspiration
/test-firmware - Build and test
```

**Now stop reading and START EXECUTING.**
