austinscip/table-wars-puck/docs/business/BAR_PILOT.md

# TABLE WARS - Bar Pilot Deployment Guide

**Your roadmap to getting TABLE WARS into a real bar for testing.**

---

## 🎯 Pilot Goals

The goal of this pilot is to:
1. **Validate the concept** - Do people actually want to play?
2. **Test durability** - Can the pucks survive bar use?
3. **Gather feedback** - What games work? What doesn't?
4. **Capture content** - Get video footage for marketing
5. **Build relationships** - Establish your first customer

**Success = People playing voluntarily + positive feedback + viral video potential**

---

## 📋 Pre-Pilot Checklist

### Phase 1: Build & Test (Complete Before Approaching Bar)

- [ ] **Order remaining parts** (~$60)
  - MT3608 boost converter (10-pack)
  - Multimeter
  - 1× LED ring backup
  - 1× MPU6050 3-pack backup
  - 2× extra batteries

- [ ] **Build first working puck**
  - Assemble per BUILD_CHECKLIST.md
  - Adjust MT3608 to exactly 5.0V
  - Upload TABLE_WARS_MODE firmware
  - Test all 8 games physically
  - Verify battery lasts 6+ hours

- [ ] **Build minimum viable set** (3-6 pucks)
  - 3 pucks = Good for small bar/demo
  - 6 pucks = Full table experience
  - Label each puck (Puck ID 1-6)
  - Test all pucks work identically

- [ ] **Film demo footage**
  - Record each game being played
  - Get reactions from friends/family
  - Create 30-second highlight reel
  - Save for showing bar owner

- [ ] **Create simple instructions**
  - 1-page laminated card
  - "HOW TO PLAY TABLE WARS"
  - Simple graphics/photos
  - List all 8 games briefly

### Phase 2: Find The Right Bar

**Ideal pilot bar characteristics:**
- ✅ Young crowd (21-35 demographic)
- ✅ Social atmosphere (not a quiet dive bar)
- ✅ Already has games (pool table, darts, etc.)
- ✅ Owner/manager is tech-friendly
- ✅ Good social media presence
- ✅ Located near you (easy to monitor)
- ✅ Slow night you can target (Monday-Thursday)

**Red flags:**
- ❌ Corporate chain (too many approvals)
- ❌ Quiet/older crowd
- ❌ Owner seems skeptical of new ideas
- ❌ Already cluttered with failed game attempts

### Phase 3: Research Your Target Bar

- [ ] **Visit during target night**
  - Observe crowd size and energy
  - See what games they currently play
  - Note peak hours
  - Identify decision maker

- [ ] **Social media research**
  - Check Instagram/Facebook
  - See if they promote events
  - Look for innovation/new ideas
  - Find owner's contact info

- [ ] **Competitor analysis**
  - What other bars have games?
  - What's working in your area?
  - How is TABLE WARS different/better?

---

## 🎤 The Pitch

### Timing Your Approach

**Best time to pitch:**
- Early afternoon (2-4pm) when bar is quiet
- NOT during peak hours
- NOT on Friday/Saturday (too busy)
- Talk to owner/manager, not bartender

### The 30-Second Hook

*"Hey [Name], I'm [Your Name]. I've built this new bar game called TABLE WARS - it's like interactive electronic game pucks that people pass around the table. Think of it like a high-tech drinking game meets arcade. I'm looking for one bar to pilot it for free for 2-4 weeks. Would you be open to a 5-minute demo?"*

**Key points:**
- **FREE** for the pilot (they pay nothing)
- **Short commitment** (2-4 weeks)
- **No work for them** (you handle everything)
- **Ask for demo first** (don't oversell before showing)

### The Demo (If They Say Yes)

1. **Show the demo video** (30 seconds)
   - Pull it up on your phone
   - Let them see people playing
   - Show excitement/reactions

2. **Let them hold a puck**
   - Turn it on
   - Let them press button/shake it
   - Run through 2-3 games quickly
   - Make it interactive, not a lecture

3. **Explain the value**
   - *"People stay longer when they're having fun"*
   - *"It's Instagrammable - free marketing for you"*
   - *"Encourages group interaction, more drink orders"*
   - *"Bar vs Bar competition potential"*

4. **Address concerns preemptively**
   - **"What if someone breaks it?"** - *"They're pretty durable, and I'll swap out any broken ones immediately. I'm here to make sure it succeeds."*
   - **"What if people don't play?"** - *"That's what the pilot is for. If it doesn't work, I take them back, no hard feelings."*
   - **"How much?"** - *"Nothing for the pilot. I want your feedback. If you love it after 2-4 weeks, we can talk about a monthly fee."*

5. **Close with a specific ask**
   - *"Can I bring 6 pucks this Thursday night and set them up at one table?"*
   - *"I'll stay the whole night to explain the game and get feedback."*
   - *"Sound good?"*

### If They're Interested But Hesitant

**Offer a super low-commitment test:**
- *"How about I bring them just for one night - this Thursday from 7-11pm?"*
- *"I'll handle everything, and if people love it, we can do the full 2-week pilot."*
- *"If it flops, I take them home and we're done. No risk to you."*

### If They Say No

**Don't burn bridges:**
- *"No problem! If you hear about it working at another bar and change your mind, here's my number."*
- Leave your contact info
- Ask for referral: *"Do you know any other bar owners who might be interested?"*

---

## 📅 Pilot Logistics

### Equipment You Need on Pilot Night

**The Pucks:**
- [ ] 3-6 fully charged pucks (6+ hour battery)
- [ ] Backup batteries (charged)
- [ ] Small toolkit (screwdriver for quick repairs)
- [ ] Charging cables + power bank

**Marketing Materials:**
- [ ] 2-3 laminated instruction cards
- [ ] QR code to feedback form (Google Form)
- [ ] Your business cards
- [ ] "HOW TO PLAY" poster (optional)

**Documentation:**
- [ ] Phone/camera for filming
- [ ] Notebook for feedback
- [ ] Laptop (in car as backup)

### Setup Process

**1 hour before peak time:**

1. **Claim a table**
   - Pick high-visibility table
   - Near bar (staff can see)
   - NOT hidden in corner

2. **Set up signage**
   - Instruction card on table
   - Make it look intentional, not random

3. **Test all pucks**
   - Boot each one
   - Verify games work
   - Check battery levels

4. **Brief the staff**
   - Explain it to bartenders
   - Give them simple pitch: *"It's a new game we're testing, free to play!"*
   - Tell them to send interested people your way

### During the Pilot Night

**Your role:**
- **Be present but not pushy**
- **Approach groups sitting idle:** *"Hey, want to try a new game? It's free!"*
- **Do the first demo yourself** - get people excited
- **Step back once they're playing** - let them discover it
- **Film reactions** (ask permission first!)
- **Take notes on:**
  - Which games get the most laughs?
  - Which games are confusing?
  - Do people play for 5 min or 30 min?
  - Do they order more drinks while playing?

**Red flags to watch for:**
- Pucks getting thrown/dropped
- Games too complicated (people give up)
- Not enough spectator value (boring to watch)
- Technical issues (LEDs flickering, games crashing)

**Good signs:**
- People filming it for Instagram
- Groups playing for 20+ minutes
- Bystanders asking "what is that?"
- Staff getting interested
- People asking "when is this coming back?"

---

## 📊 Gathering Feedback

### Create a Simple Google Form

**Questions to ask:**

1. **How fun was TABLE WARS?** (1-10 scale)
2. **Which game was your favorite?**
   - [ ] Speed Tap Battle
   - [ ] Shake Duel
   - [ ] Red Light Green Light
   - [ ] LED Chase Race
   - [ ] Color Wars
   - [ ] Rainbow Roulette
   - [ ] Visual Bomb
   - [ ] Simon Says

3. **What would make it better?**
   - [ ] Different games
   - [ ] Multiplayer mode
   - [ ] Leaderboard
   - [ ] Prizes/rewards
   - [ ] Other: _______

4. **Would you play this again?**
   - [ ] Definitely
   - [ ] Probably
   - [ ] Maybe
   - [ ] No

5. **Would you pay $5 to play for an hour?**
   - [ ] Yes
   - [ ] No
   - [ ] Maybe if _______

6. **Can we contact you for future testing?**
   - Email: _______
   - Instagram: _______

**Share this via:**
- QR code on table
- Text link you share verbally
- Instagram story (tag the bar)

---

## 🎥 Content Creation Strategy

### What to Film

**Mandatory shots:**
1. **Unboxing/setup** - You setting up the pucks
2. **First reactions** - People's faces when they first play
3. **Action shots** - People shaking pucks, pressing buttons
4. **Crowd shots** - Multiple people playing together
5. **Highlights** - Close-ups of LED animations
6. **Testimonials** - *"This is so cool!"* reactions

**Bonus footage:**
1. Bar owner trying it
2. Bartender reaction
3. Puck in action (POV from puck)
4. Montage of all 8 games

### Editing Plan

**Create 3 versions:**

1. **30-second Instagram Reel**
   - Fast cuts
   - Upbeat music
   - Text overlays: "NEW BAR GAME 🔥"
   - End with "Coming to [Bar Name]"

2. **60-second YouTube Short**
   - Explain what it is
   - Show gameplay
   - Show reactions
   - CTA: "Comment which game you'd play!"

3. **2-minute full video**
   - Story format
   - Problem: "Bar games are boring"
   - Solution: TABLE WARS
   - Social proof: Show people playing
   - Next steps: "DM for pilot in your city"

### Social Media Strategy

**Post schedule:**
- **Night of pilot:** Instagram story live updates
- **Next morning:** Post highlight reel
- **2-3 days later:** Longer YouTube video
- **1 week later:** Testimonial compilation

**Hashtags:**
- #TableWars
- #BarGames
- #InteractiveGames
- #[YourCity]Nightlife
- #TechMeetsBar

**Tag:**
- The bar's social accounts
- People who played (with permission)
- Local influencers (if you know any)

---

## 📈 Post-Pilot Analysis

### Week 1 Debrief (After First Night)

**Ask yourself:**

1. **Did people play voluntarily?**
   - Yes = Great sign!
   - No = Need better hook/marketing

2. **How long did groups play?**
   - 20+ min = Solid engagement
   - 5-10 min = Games need work
   - < 5 min = Major redesign needed

3. **Technical issues?**
   - List every bug/failure
   - Fix before next session

4. **Which games worked best?**
   - Double down on winners
   - Cut or redesign losers

5. **Bar owner's reaction?**
   - Excited = Continue pilot
   - Neutral = Show data, push harder
   - Negative = Pivot or find new bar

### Week 2-4: Iterate & Improve

**Based on feedback:**
- [ ] Update firmware (fix bugs, tweak games)
- [ ] Improve instructions
- [ ] Add requested features
- [ ] Build more pucks if demand is high
- [ ] Schedule regular nights (every Thursday?)

**Track metrics:**
- Total hours played
- Number of unique players
- Social media engagement
- Bar owner satisfaction (weekly check-in)
- Drink sales on pilot nights (ask bartender)

---

## 💰 Pivot to Paid (If Pilot Succeeds)

### When to Bring Up Pricing

**Wait until:**
- Week 3-4 of pilot
- Bar owner has seen people playing regularly
- You have solid feedback/data
- People are asking "is this staying?"

### Proposed Pricing Models

**Option 1: Monthly Rental**
- $150-300/month for 6 pucks
- You maintain/update them
- They keep them at the bar

**Option 2: Revenue Share**
- Free rental
- Bar charges players ($5 per hour)
- You get 50% of revenue

**Option 3: Purchase**
- $500-800 one-time for 6 pucks
- Bar owns them
- You offer paid support ($50/month)

### The Pricing Pitch

*"So it's been [X weeks], and I've been hearing great feedback. People love it! I'm thinking of rolling this out to more bars. Would you want to keep the pucks here? I'm thinking $200/month for the set of 6, and I'll handle all updates and repairs. That's like $6-7 per night for a unique attraction that keeps people at your bar longer. Sound fair?"*

**If they hesitate:**
- Offer first month at 50% off
- Offer trial extension (one more month free)
- Ask what price would work for them

**If they say yes:**
- Get it in writing (simple one-page agreement)
- Set up recurring payment (Venmo/PayPal/Square)
- Thank them for being your first customer!

---

## 🚀 Scaling Beyond the First Bar

### Once You Have Proof of Concept

**Leverage your success:**

1. **Film testimonial from bar owner**
   - *"TABLE WARS has been great for business..."*
   - Use for pitching other bars

2. **Create case study**
   - "How [Bar Name] Increased Engagement 40%"
   - Use data from pilot

3. **Build waitlist**
   - Instagram bio: "DM to bring TABLE WARS to your bar"
   - Collect interested venues

4. **Approach competitors**
   - *"[Rival Bar] has it, want it too?"*
   - FOMO is powerful

### Next Bars to Target

**Start local, then expand:**
- 3-5 bars in your city (Month 1-3)
- Nearby cities (Month 4-6)
- College towns (Month 6-12)
- Tourist destinations (Year 2)

**Build the "Bar vs Bar" narrative:**
- Leaderboard across all locations
- Monthly championships
- Winner gets free month rental

---

## 🎯 Success Metrics

### Hard Metrics (Track These)

- [ ] Number of groups who played
- [ ] Average play time per group
- [ ] Total player count (unique individuals)
- [ ] Social media impressions
- [ ] QR code scans (feedback form)
- [ ] Puck uptime (% working vs broken)
- [ ] Bar owner satisfaction (1-10 rating)

### Soft Metrics (Observe These)

- [ ] Energy level at table (laughter, cheering?)
- [ ] Repeat players (same people coming back?)
- [ ] Spectator interest (people watching?)
- [ ] Staff enthusiasm (bartenders talking it up?)
- [ ] Organic word-of-mouth (people telling friends?)

### Pilot = Success If:

✅ **50+ unique players** in 2-4 weeks
✅ **20+ minute average** play time
✅ **8/10 or higher** average fun rating
✅ **Bar owner wants to keep it**
✅ **At least 1 viral social post** (500+ views)
✅ **Zero major technical failures**

### Pilot = Needs Work If:

⚠️ < 30 players
⚠️ < 10 minute average play time
⚠️ < 6/10 fun rating
⚠️ Bar owner is lukewarm
⚠️ No social traction

### Pilot = Pivot/Kill If:

❌ < 10 players
❌ People give up quickly
❌ Constant technical issues
❌ Bar owner wants you to remove it
❌ Zero organic interest

---

## 📞 Communication Templates

### Follow-Up Email (Day After Pilot)

**Subject:** Thanks for hosting TABLE WARS last night!

---

Hi [Bar Owner Name],

Thanks so much for letting me test TABLE WARS at [Bar Name] last night! I really appreciate you taking a chance on something new.

**Quick summary:**
- [X] groups played
- Average play time: [X] minutes
- Most popular game: [Game Name]
- Overall feedback: [Positive highlights]

I got some great footage and feedback. [Link to Instagram post/video]

For next week:
- [Any improvements you're making based on feedback]
- Planning to be there again [Day/Time]

Let me know if you have any questions or concerns!

Best,
[Your Name]
[Phone]
[Email]

---

### Pricing Conversation (Week 3-4)

**Text or in-person:**

---

Hey [Name], TABLE WARS has been going great! People seem to really love it. I've been thinking - would you want to keep it here permanently? I'm launching officially next month and want [Bar Name] to be one of my flagship locations.

I'm thinking $200/month for the 6 pucks, and I handle all repairs/updates. That's about $6 per night for a unique game that keeps people around longer.

First month would be half off ($100) since you helped me pilot it. Interested?

---

---

## 🧰 Troubleshooting Guide (During Pilot)

### Common Issues & Quick Fixes

**Puck won't turn on:**
- Swap battery with charged backup
- Check power switch
- If still dead, swap entire puck

**LEDs dim or flickering:**
- Battery dying - swap immediately
- MT3608 may need adjustment (do later)

**Game freezes/crashes:**
- Note which game caused it
- Power cycle puck (off/on)
- If repeats, disable that game mode

**Button not responding:**
- Check if it's loose
- Try gentle press vs hard press
- May need hardware fix (swap puck)

**People don't understand the game:**
- Do a live demo for next group
- Simplify instruction card
- Add visual cues to gameplay

**Puck gets dropped:**
- Check for damage immediately
- Test all functions
- If working, keep using
- Note durability for V2 design

**Bar too loud to hear instructions:**
- Rely on visual LED feedback
- Make button presses obvious
- Add bigger text to instruction card

---

## 🎁 Bonus: Pilot Incentives

### Gamification for Pilot Night

**Ideas to drive engagement:**

1. **High Score Challenge**
   - "Best Score Tonight Wins Free Drink!"
   - Bar comp's the drink (you reimburse $5)
   - Creates urgency/competition

2. **Social Media Contest**
   - "Post to Instagram, tag us, enter to win [Prize]"
   - Prize = Free puck rental for home party?
   - Drives content creation

3. **Loyalty Card**
   - "Play 5 times, get a free [Bar Merch]"
   - Encourages repeat play
   - Bar owner may sponsor prizes

---

## ✅ Final Pre-Launch Checklist

### Before You Walk Into That Bar

- [ ] All pucks fully charged (8+ hours)
- [ ] Firmware tested on all pucks
- [ ] Demo video ready on phone
- [ ] Business cards printed
- [ ] Instruction cards laminated
- [ ] Feedback QR code working
- [ ] Toolkit in backpack
- [ ] Backup batteries charged
- [ ] Phone charged (for filming)
- [ ] Practiced pitch 10 times

### During the Pitch

- [ ] Smile and be friendly
- [ ] Lead with value ("free marketing", "people stay longer")
- [ ] Ask for demo, not a commitment
- [ ] Listen more than you talk
- [ ] Address concerns calmly
- [ ] Close with specific next step

### After the Pilot Night

- [ ] Thank bar owner in person
- [ ] Send follow-up email next day
- [ ] Post social media content
- [ ] Analyze feedback data
- [ ] Fix any technical issues
- [ ] Schedule next session (if successful)

---

## 🚀 You Got This!

Remember: **The first pilot is about learning, not perfection.**

- If people smile, laugh, and play → You're onto something
- If the bar owner says "this is cool" → You're building trust
- If you get even one viral Instagram story → You're creating buzz

**Don't wait for perfect. Build your first working puck and get into a bar within 30 days.**

The best product feedback comes from real users in real bars. Go get it!

---

**Questions? Stuck? Need a pep talk?**
Re-read this guide. Then just go do it. The worst they can say is "no thanks," and then you find another bar.

**Good luck! 🍻🎮**
