austinscip/table-wars-puck/docs/business/BUSINESS_PLAYBOOK.md

# TABLE WARS - 90-Day Validation → 12-Month Scale Playbook

**Goal**: Validate product-market fit in 90 days, then scale to 100 bars in 12 months.

**Current Status**: Working prototype, zero customers, unproven business model.

---

## 📋 EXECUTIVE SUMMARY

**The Strategy**:
1. Spend 30 days proving bars will PAY (not just try it for free)
2. Spend 60 days running paid pilots to prove ROI and collect data
3. Make go/no-go decision at Day 90 based on hard metrics
4. If validated, scale aggressively with pre-orders funding manufacturing

**Key Metrics**:
- **Validation Success** = 5+ bars pay for pilots, 3+ renew/buy after trial
- **Scale Success** = 100 bars deployed, $500k ARR, 40%+ gross margin
- **Failure Threshold** = <20% conversion from demo → paid pilot = pivot or kill

**Capital Required**:
- Validation phase: $3-5k (mostly your time + 12 pucks)
- Scale phase: $50-100k (manufacturing + inventory + sales)

---

# PHASE 1: CUSTOMER DISCOVERY (Days 1-30)

## Week 1: Market Research & Competitive Intelligence

### Monday - Tuesday: Competitor Deep Dive

**Task**: Research existing bar entertainment solutions

**Companies to analyze**:
1. **Buzztime** (trivia tablets)
   - Website: buzztime.com
   - Research: Pricing, features, customer reviews
   - Call 3 bars that use it, ask what they love/hate

2. **NTN (National Trivia Network)**
   - Similar to Buzztime, older platform
   - Research: Why are they losing market share?

3. **Pour Taproom** (RFID self-serve + games)
   - Self-serve beer with RFID wristbands
   - Research: How do they monetize games?

4. **AMI Jukeboxes** (TouchTunes competitor)
   - Research: Lease model, revenue share %
   - Understand bar entertainment economics

5. **Digital dartboards** (Arachnid, Valley)
   - Research: Purchase vs lease, price points
   - Understand how bars buy physical games

**Deliverables**:
```
Competitive Analysis Spreadsheet:
├─ Company name
├─ Product type (tablets, physical, RFID, etc.)
├─ Pricing model (sale, lease, rev share, per-play)
├─ Monthly cost to bar
├─ Revenue to vendor
├─ Customer reviews (what do bars love/hate?)
├─ Estimated market share
└─ Your competitive advantage vs them
```

**Actions**:
- [ ] Create competitor spreadsheet (5 companies minimum)
- [ ] Call 3 bars that use Buzztime, ask 10 questions each
- [ ] Identify pricing sweet spot (what do bars currently pay?)

---

### Wednesday - Friday: Bar Owner Interviews (Customer Discovery)

**Goal**: Talk to 20 bar owners BEFORE you pitch anything

**Script** (Informational interview, NOT sales call):

> "Hi [Name], I'm researching bar entertainment for a project. I have 5 quick questions - can I buy you a coffee/beer this week for 15 minutes of your time?"

**The 10 Questions to Ask Every Bar Owner**:

1. "What entertainment do you currently offer?" (Pool, darts, trivia, music?)
2. "What's working? What's not?" (Understand pain points)
3. "How do you decide to buy/lease new entertainment?" (Decision criteria)
4. "What's your budget for entertainment equipment?" (Price sensitivity)
5. "How do you measure ROI on entertainment?" (Metrics: drink sales, foot traffic, average check?)
6. "Have you tried Buzztime/trivia tablets? Why/why not?" (Competitive intel)
7. "What would make customers stay 30 minutes longer?" (Their theory)
8. "If I had interactive game pucks that track scores, would you try them?" (Gauge interest)
9. "What would you pay? One-time or monthly?" (Pricing model preference)
10. "What would make this fail in your bar?" (Risks from their POV)

**Target**:
- **20 bar owner interviews** in Week 1-2
- 10 in-person, 10 phone/video
- Mix: dive bars, sports bars, upscale cocktail bars
- Document everything in spreadsheet

**Deliverables**:
```
Customer Discovery Spreadsheet:
├─ Bar name, location, type
├─ Current entertainment (pool, darts, trivia, etc.)
├─ Annual entertainment budget
├─ Decision maker (owner, manager, corp?)
├─ Pain points (slow nights? customer boredom?)
├─ Willingness to try TABLE WARS (yes/maybe/no)
├─ Preferred pricing model (sale, lease, rev share)
├─ Objections/concerns
└─ Follow-up date
```

**Success Metric**:
- If **<30% say "yes, I'd try it"** → Red flag, rethink concept
- If **30-50% interested** → Promising, continue
- If **>50% interested** → Strong signal, move fast

---

## Week 2: Build Your Pitch & Demo Materials

### Monday - Wednesday: Create Sales Assets

**1. One-Page Pitch Deck** (PDF or Keynote)

```
Slide 1: The Problem
"70% of bars struggle with slow weeknights and declining foot traffic"

Slide 2: The Solution
"TABLE WARS: Interactive game pucks that turn tables into
multiplayer battle arenas. Think digital darts meets Mario Kart."

Slide 3: How It Works
[Photos of pucks, LED animations, multiplayer gameplay]
"Place 6 pucks on tables. Players compete in 8 different games.
Scores show on TV leaderboard. Games last 5-10 minutes."

Slide 4: Why Bars Love It
✓ Increases drink sales (customers stay longer)
✓ Drives weeknight traffic (game leagues)
✓ Social media moments (LED effects)
✓ Easy setup (plug and play)

Slide 5: Pricing
"$99/month for 6 pucks + leaderboard server"
OR "$599 one-time purchase + $29/month software"
[Test both models]

Slide 6: Proof
"5 bars piloting now, 40% increase in Tuesday/Wednesday sales"
[You don't have this yet - placeholder for later]

Slide 7: Next Steps
"2-week free trial. If you love it, keep it. If not, no charge."
```

**2. 90-Second Demo Video**

**Script**:
```
0:00-0:15: Hook
"Bars lose money on slow weeknights. What if you could turn
every table into an interactive game?"

0:15-0:30: Product Demo
[Show pucks lighting up, players competing, LED effects]
"TABLE WARS: Interactive pucks with 8 multiplayer games"

0:30-0:60: Gameplay Examples
[Show "Pass The Bomb" game - tension building]
[Show "Team Battle" - red vs blue LEDs]
"Games last 5-10 minutes. Perfect for bar attention spans."

1:00-1:30: Business Value
"Customers stay 30 min longer = 2 more drinks = $15 extra revenue"
"6 tables × $15 × 4 nights/week = $360/week extra sales"
[Math sells to bar owners]

1:30-1:45: Social Proof (once you have it)
"The Rusty Nail saw 40% increase in Tuesday sales after adding TABLE WARS"

1:45-2:00: CTA
"Try it free for 2 weeks. Text 'GAMES' to [your number]"
```

**Tools**: iPhone + iMovie (free), or pay $200 for Fiverr video editor

**3. Landing Page** (Simple, 1-page site)

**URL**: tablewars.io or tablewars.bar (buy domain: $12/year)

**Sections**:
```html
Hero Section:
  Headline: "Turn Tables Into Multiplayer Battle Arenas"
  Subhead: "Interactive game pucks that increase bar sales"
  CTA: "Request Free Trial" [Button → Email capture]

How It Works (3 steps):
  1. Place pucks on tables
  2. Players compete in 8 games
  3. Leaderboard shows on TV

Demo Video:
  [Embed 90-second video]

Pricing:
  "$99/month for 6 pucks" [or your chosen model]
  "First 2 weeks free"

Social Proof:
  "Trusted by [5] bars" [update as you grow]
  [Photos of bars using it]

CTA:
  "Request Free Trial" [Email capture form]
```

**Tools**:
- Carrd.co ($19/year, easiest)
- Webflow (free, more customizable)
- Squarespace ($16/month, professional)

**Email Capture**: Use Airtable form (free) or Typeform

---

### Thursday - Friday: Build Your First 2 Pilot Sets

**Goal**: Build 2 complete sets (12 pucks total) for pilot deployments

**Why 2 sets?**
- You need inventory to deploy immediately when a bar says "yes"
- Can't scale yet, but can prove concept with 2 bars simultaneously

**Build Checklist**:
- [ ] Order components for 12 pucks (see PARTS_LIST.md)
- [ ] 3D print 12 enclosures (or use breadboard setups for pilots)
- [ ] Assemble, test, QA each puck
- [ ] Create "pilot kit" box:
  - [ ] 6× pucks
  - [ ] 1× charging cables (or charging dock)
  - [ ] 1× Raspberry Pi server (for scoreboard)
  - [ ] 1× HDMI cable (for TV)
  - [ ] 1× Quick start guide (laminated card)
  - [ ] 1× "How to Play" table tents (8.5×11" folded)

**Budget**: ~$360/set × 2 = $720

---

## Week 3-4: Outbound Sales Blitz

### Goal: Book 10 In-Person Demos

**Strategy**: Cold outreach → Demo → Close to paid pilot

### Monday - Tuesday: Build Target List

**Ideal Customer Profile (ICP)**:
```
Bar Type: Sports bars, college bars, craft beer bars
Location: Within 30 min drive of your home (for support)
Size: 100-200 capacity (big enough for revenue, small enough to decide fast)
Vibe: Social, younger crowd (25-40 demo), game-friendly
Avoid: Dive bars (no budget), upscale cocktail bars (games don't fit vibe)
```

**Target List**: 50 bars in your city

**Tools**:
- Google Maps: Search "sports bars near me"
- Yelp: Filter by $$ (mid-price), 3.5+ stars
- Instagram: Search #[YourCity]Bars, find active accounts

**Deliverable**: Spreadsheet with 50 bars
```
Columns:
├─ Bar name
├─ Address
├─ Phone
├─ Owner/Manager name (research on LinkedIn/Facebook)
├─ Instagram handle (for social proof later)
├─ Best time to visit (call ahead or guess)
└─ Notes
```

---

### Wednesday - Friday (Week 3) + All of Week 4: Make Contact

**Multi-Channel Approach**:

**Channel 1: In-Person Cold Visits** (HIGHEST CONVERSION)

**When**: Tuesday - Thursday, 2-4pm (slow time, manager available)

**Script**:
> "Hi! I'm [Name], I build interactive game tech for bars. Do you have 2 minutes? I want to show you something cool that's helping bars increase weeknight sales."
>
> [Pull out puck, light it up with LED animation]
>
> "This is TABLE WARS - think digital darts meets Mario Kart. Customers compete in multiplayer games, scores show on your TV. Bars using this are seeing 30-40% sales lifts on slow nights."
>
> "Can I leave you a demo unit to try tonight? I'll come back Friday to get your feedback."

**Close**:
- Get phone number + best time to follow up
- Leave demo unit (if they agree)
- OR book time for full demo later this week

**Goal**: 5 in-person visits/day × 4 days = 20 bars visited

---

**Channel 2: Cold Calls** (MEDIUM CONVERSION)

**When**: Monday/Tuesday mornings, 10-11am

**Script**:
> "Hi, is [Manager Name] available? This is [Your Name] from TABLE WARS. We make interactive game pucks that are helping bars like [Local Bar Name] increase weeknight sales by 30-40%. I'd love to drop by for 5 minutes to show you how it works - are you free tomorrow around 2pm?"

**Objections**:
- "Not interested" → "I get it - can I ask what you're currently doing for entertainment? [Listen, then adapt pitch]"
- "Too busy" → "I'll make it 3 minutes. I'll bring coffee. Tuesday at 2?"
- "Email me" → "Sure, what's your email? I'll send a video, but trust me, you have to see the LEDs in person. Can I swing by after you watch the video?"

**Goal**: 20 calls/day, book 2 demos/day

---

**Channel 3: Direct Instagram DM** (LOW CONVERSION, but scalable)

**Who**: Bars with active Instagram (posting daily)

**Message**:
> "Hey [Bar Name]! 👋 Love your vibe. I'm building interactive game pucks (think glowing LED bar games) and looking for a few local bars to pilot them. Mind if I DM you a 60-sec demo video? No sales pitch - just want your feedback as a bar pro."

[If they respond]

> [Send demo video]
>
> "Would you ever try something like this for a slow Tuesday/Wednesday? I'm offering 2-week free trials to 5 local spots."

**Goal**: 10 DMs/day, 10-20% response rate = 1-2 demos/week

---

### End of Week 4: Tally Results

**Success Metrics**:

```
Target: 50 bars contacted
├─ 20 in-person visits
├─ 20 cold calls
└─ 10 Instagram DMs

Conversion Funnel:
├─ 50 contacted
├─ 20 demos completed (40% demo rate)
├─ 10 "interested, let's talk pricing" (50% interest rate)
└─ 5 agree to paid pilot (25% close rate)

If you hit this → STRONG VALIDATION, continue
If <5 paid pilots → Need to iterate offer or pricing
If <2 paid pilots → Red flag, may need to pivot
```

---

# PHASE 2: PAID PILOT PROGRAM (Days 31-90)

## Goal: Prove ROI & Collect Data

**Strategy**: Run 5 paid pilots, collect data, iterate rapidly

---

## Week 5: Close First 3 Pilots

### Pilot Offer Structure

**Option A: Paid Trial** (Recommended for validation)
```
Offer: "$99/month, first month 50% off ($49)"
Why: Tests willingness to pay, qualifies serious buyers
Risk: Lower conversion than free trial
```

**Option B: Free Trial → Paid**
```
Offer: "Free for 2 weeks, then $99/month if you keep it"
Why: Easier conversion, gets pucks into bars fast
Risk: Bars may use for 2 weeks then ghost you
```

**MY RECOMMENDATION**: Option A (Paid Trial)
- If bars won't pay $49 for a trial, they won't pay $99/month
- Qualifies serious customers immediately
- Shows real demand validation

---

### Pilot Agreement (Simple 1-Page Contract)

**Use this template**:

```
TABLE WARS - PILOT AGREEMENT

Bar: [Bar Name]
Contact: [Manager Name, Phone, Email]
Start Date: [Date]
End Date: [90 days from start]

What You Get:
✓ 6× interactive game pucks
✓ 1× Raspberry Pi server + TV display
✓ Access to 8 games (13 total with multiplayer)
✓ Phone/email support (response within 24 hours)
✓ Free software updates

Pricing:
Month 1: $49 (50% off)
Months 2-3: $99/month
After 3 months: $99/month (or purchase for $599)

Your Responsibilities:
✓ Provide WiFi access for server
✓ Provide TV/monitor for scoreboard display
✓ Promote games to customers (we provide table tents)
✓ Report issues within 24 hours
✓ Share feedback monthly

Our Responsibilities:
✓ Replace broken pucks within 48 hours
✓ Provide phone support 7 days/week
✓ Fix software bugs within 1 week
✓ Help you promote games to customers

Cancellation:
Either party can cancel with 30 days notice.
If you cancel, we pick up equipment within 7 days.

Success Metrics (Optional):
We'll help you track:
- Games played per week
- Average customer stay time (before/after)
- Sales on game nights vs non-game nights

Data Sharing:
You agree to share anonymized usage data (game plays, peak times)
for product improvement. We will never share your sales data.

Signature: _____________________ Date: _______
[Bar Manager]

Signature: _____________________ Date: _______
[Your Name], TABLE WARS
```

**Tools**:
- DocuSign (free for 3 docs/month) OR
- HelloSign OR
- Just print, sign, scan

---

### Week 5 Tasks:

- [ ] Close 3 pilot agreements (from Week 3-4 leads)
- [ ] Collect first payment ($49 × 3 = $147) - use Square, Stripe, or PayPal
- [ ] Schedule installation dates

---

## Week 6-8: Install & Launch Pilots

### Installation Checklist (Per Bar)

**Pre-Installation (Day Before)**:
- [ ] Call bar, confirm installation time
- [ ] Pack pilot kit: 6 pucks, server, cables, table tents, quick start guide
- [ ] Charge all pucks to 100%
- [ ] Test all pucks one final time

**On-Site Installation (60-90 minutes)**:
1. **Intro meeting** (10 min)
   - Meet bar manager + staff
   - Explain how games work
   - Set expectations

2. **Hardware setup** (20 min)
   - Connect Raspberry Pi to bar WiFi
   - Connect HDMI to TV (ask where they want scoreboard)
   - Test server boots up, shows leaderboard

3. **Puck demo** (20 min)
   - Show all 8 single-player games
   - Demo 1-2 multiplayer games (if other staff available)
   - Let staff play 5 minutes

4. **Staff training** (20 min)
   - How to charge pucks
   - How to troubleshoot (restart server, etc.)
   - How to promote games to customers
   - Give them FAQ sheet

5. **Promotion setup** (10 min)
   - Place table tents on all tables
   - Put up poster (if you made one)
   - Add Instagram story template (they can post)

6. **Final check** (10 min)
   - Test 2-3 games with staff
   - Get manager's cell phone for support
   - Schedule check-in call for 1 week

**Post-Installation (Same Day)**:
- [ ] Send follow-up email with:
  - Quick start guide PDF
  - Your phone number for support
  - Link to demo videos (to show customers)
- [ ] Add to "Active Pilots" tracking spreadsheet

---

### Week 6-8: Deploy to 3-5 Bars

**Timeline**:
- Week 6: Install Bar #1, #2
- Week 7: Install Bar #3
- Week 8: Install Bar #4, #5 (if you closed 5 pilots)

**Why stagger?**
- You only have 2 sets built (12 pucks)
- Need to build 1-2 more sets during Week 6-7
- Allows you to iterate based on Bar #1 feedback before deploying to others

---

## Week 7-12: Data Collection & Iteration

### Metrics to Track (Per Bar)

**Create a "Pilot Metrics" Spreadsheet**:

```
Bar Name: [Name]
Week #: [1-12]

Usage Metrics:
├─ Total games played this week
├─ Peak day (which day had most plays?)
├─ Peak hour (6-8pm? 9-11pm?)
├─ Most popular game
├─ Avg games per customer (if trackable)

Business Metrics (Ask bar to share):
├─ Total sales this week (or just game nights)
├─ Sales on game nights vs non-game nights (% increase)
├─ Average check size on game nights
├─ Customer count on game nights
├─ New customers (did games bring in new people?)

Engagement:
├─ Did customers take photos/videos? (Check Instagram tags)
├─ Did customers ask about games?
├─ Customer feedback (ask bartender)

Issues:
├─ Any pucks break?
├─ Any technical issues?
├─ Staff complaints?
├─ Customer complaints?

Bar Manager Satisfaction (1-10):
├─ "How happy are you with TABLE WARS so far?"
├─ "Would you recommend to other bars?"
└─ "Will you keep this past the pilot?"
```

---

### Weekly Check-Ins (Critical!)

**Schedule**: Every Monday, call each pilot bar

**10-Minute Call Script**:

> "Hey [Manager]! Quick check-in. How did last week go with the pucks?"
>
> [Listen to feedback]
>
> "Awesome! I'm tracking some metrics - mind if I ask 3 quick questions?"
>
> 1. "How many games do you think were played? (Rough estimate)"
> 2. "Did you notice any sales increase on nights people played?"
> 3. "On a scale of 1-10, how happy are you so far?"
>
> "Any issues or broken pucks? I can swing by tomorrow to fix."
>
> "Great! Talk next Monday. Text me if anything breaks."

**Goal**:
- Maintain relationship
- Collect data
- Catch problems early
- Show you care (builds loyalty)

---

### Iteration Based on Feedback

**Common Feedback & Fixes**:

| Feedback | Fix |
|---|-----|
| "Customers don't notice the pucks" | Add LED "attract mode" (pulse lights when idle) |
| "Games are too hard to understand" | Create simpler tutorial mode |
| "Pucks die too fast" | Optimize power settings, provide charging dock |
| "Scoreboard is boring" | Add animations, photos of winners |
| "Customers want prizes" | Create "high score of the week" prize idea |
| "WiFi keeps dropping" | Add offline mode, better reconnection logic |

**Rapid Iteration**:
- Week 7-8: Collect feedback
- Week 9: Implement 2-3 critical fixes
- Week 10: Push firmware update to all pilot bars
- Week 11-12: Measure improvement

---

## Week 12-13: Pilot Results Analysis

### Calculate ROI for Each Bar

**Example Calculation** (Bar #1 - "The Rusty Nail"):

```
BEFORE TABLE WARS (Average Tuesday):
├─ Customer count: 40
├─ Average check: $25
├─ Total sales: $1,000

AFTER TABLE WARS (Average Tuesday with games):
├─ Customer count: 52 (+30%)
├─ Average check: $28 (+12%, stayed longer)
├─ Total sales: $1,456 (+45.6%)

Weekly Impact (2 game nights: Tue + Wed):
├─ Incremental sales: $456 × 2 = $912/week
├─ Monthly: $912 × 4 = $3,648
├─ Bar's cost: $99/month
├─ ROI: $3,648 / $99 = 36.8× return 🔥

Annual Impact:
├─ Incremental revenue: $43,776/year
├─ Bar's cost: $1,188/year
├─ ROI: $43,776 / $1,188 = 36.8× return
└─ Net profit to bar: ~$42,588 (assuming 30% margin)
```

**Do this for all 5 pilot bars**, create comparison table

---

### Week 13: GO / NO-GO DECISION

**Decision Criteria**:

### ✅ STRONG GO SIGNAL (Scale to 100 bars):

```
Metrics:
✓ 4+ of 5 bars want to continue past pilot
✓ Average 30%+ increase in sales on game nights
✓ 50+ games played per bar per week
✓ <10% puck failure rate
✓ Bar managers rating 7+ / 10 satisfaction
✓ 0 bars had major issues (broken pucks, WiFi fails, etc.)

Financial:
✓ $99/month pricing is sustainable (bars see ROI)
✓ You're profitable at $99/month (vs COGS + support time)

Qualitative:
✓ Customers love it (social media posts, word of mouth)
✓ Bars are promoting it themselves
✓ Other bars are asking about it
```

**Action**: Move to PHASE 3 (Scale to 100 bars)

---

### 🟡 MIXED SIGNAL (Iterate, don't scale yet):

```
Metrics:
⚠ 2-3 of 5 bars want to continue (60%)
⚠ 10-20% sales increase (marginal)
⚠ 20-40 games/week (low engagement)
⚠ 10-20% failure rate (quality issues)
⚠ Bar managers rating 5-7 / 10

Financial:
⚠ Bars say $99/month is too high, suggest $49
⚠ You're barely profitable at $99/month

Qualitative:
⚠ Customers like it but don't seek it out
⚠ Games need improvement (feedback consistent across bars)
```

**Action**:
- Run another 90-day iteration cycle
- Fix top 3 issues identified
- Try 5 new bars with improved product
- Re-evaluate after another 90 days

---

### 🔴 STRONG NO-GO SIGNAL (Pivot or shut down):

```
Metrics:
✗ <2 of 5 bars want to continue (<40%)
✗ <10% sales increase (not worth it to bars)
✗ <20 games/week (nobody playing)
✗ >30% failure rate (product not ready)
✗ Bar managers rating <5 / 10

Financial:
✗ Even at $49/month, bars say it's not worth it
✗ You're losing money on every deployment

Qualitative:
✗ Customers don't care
✗ Bars only tried it because it was free/cheap
✗ No organic word of mouth
```

**Action**:
- **Pivot Option 1**: Try different venue (breweries? arcades? offices?)
- **Pivot Option 2**: Different use case (team building? events?)
- **Pivot Option 3**: Sell to competitor who has distribution
- **Shut Down**: Cut losses, move to next idea

**DO NOT SCALE A PRODUCT THAT ISN'T WORKING**

---

# PHASE 3: SCALE TO 100 BARS (Months 4-15)

*Only proceed if you got STRONG GO signal in Phase 2*

---

## Month 4: Prepare for Scale

### Task 1: Raise Capital or Pre-Sell

**You need $50-100k to scale to 100 bars. Here's why:**

```
Manufacturing Costs:
├─ Injection molding tooling: $20-30k (one-time)
├─ First production run (600 pucks = 100 bars): $24k
│   └─ $40 COGS × 600 = $24,000
├─ 100× Raspberry Pi servers: $5k
├─ Packaging, shipping materials: $2k
└─ TOTAL: $51-61k

Working Capital:
├─ Need inventory before you can deploy
├─ 60-90 day payment terms if selling to distributors
└─ Need cash buffer: $10-20k

Sales & Marketing:
├─ Trade show booth: $3-5k
├─ Demo units for sales team: $2k
├─ Marketing materials: $2k
└─ TOTAL: $7-9k

GRAND TOTAL: $68-90k
```

**Funding Options**:

**Option A: Pre-Sales** (Bootstrap-Friendly)
```
Strategy: Sell 50 bars BEFORE you manufacture

Offer: "Founding Member Pricing"
├─ $899 one-time purchase (vs $1,200 later)
├─ OR $79/month (vs $99 later)
├─ Guarantee: "First 50 bars get lifetime discounts"

Math:
├─ 50 bars × $899 = $44,950 upfront
├─ Covers injection molding + first production run
├─ Ship in 90 days

How to Pre-Sell:
├─ Email your 50-bar target list from Phase 1
├─ Offer pilot pricing: "$899 now, save $301"
├─ Leverage social proof: "5 bars already running this successfully"
└─ Goal: 20-30 pre-orders in 30 days
```

**Option B: Friends & Family Round** ($25-50k)
```
Offer: 10-20% equity for $25-50k
Pitch: "I've validated demand with 5 paying bars. I need capital
to manufacture 600 pucks and scale to 100 bars in 12 months."
Show: Pilot data, ROI metrics, financial projections
```

**Option C: Small Business Loan** ($50k)
```
SBA Microloan: Up to $50k at ~8% interest
Requirements: Business plan, pilot data, credit score 680+
Best for: If you have strong credit and pilot traction
```

**Option D: Angel Investor** ($100-250k)
```
Trade: 15-25% equity for $100-250k
Pitch: "Bar entertainment is a $2B market. I'm taking share from
Buzztime with better product and lower cost."
Show: 5 happy pilot bars, 30%+ sales lift data, path to 1,000 bars
```

**MY RECOMMENDATION**: Try Option A (Pre-Sales) first
- Lowest dilution
- Validates demand AGAIN (if people pre-pay, it's real)
- If you can pre-sell 30-50 bars → angels will fight to invest

---

### Task 2: Manufacturing Setup

**Step 1: Get Injection Molding Quotes**

**Send CAD files to 3 companies**:
1. **Protolabs** (USA, fast, expensive)
   - Request quote on website
   - Expect: $25-35k tooling, $4-6 per part

2. **Star Rapid** (China, slower, cheaper)
   - Email quote request
   - Expect: $15-20k tooling, $2-3 per part

3. **Xometry** (Marketplace, medium)
   - Upload CAD, instant quote
   - Expect: $20-30k tooling, $3-5 per part

**Questions to ask**:
- Tooling lead time? (6-12 weeks typical)
- Per-part cost at 100, 500, 1000 qty?
- Material options? (PETG, ABS, PC)
- Can you do overmolding for TPU bumper?
- What's the minimum order quantity?

**Goal**: Choose vendor by end of Month 4

---

**Step 2: PCB Assembly Partner**

**Current**: You're hand-wiring ESP32s (doesn't scale)
**Needed**: Custom PCB with all components

**Options**:
1. **PCBWay** (China)
   - PCB fabrication + assembly
   - Upload schematic, they quote
   - Expect: $15-20 per assembled board (qty 500+)

2. **MacroFab** (USA)
   - More expensive but faster
   - Great for small runs
   - Expect: $25-30 per assembled board

**Task**: Hire electrical engineer (Upwork, $500-1000) to design custom PCB
- Integrate ESP32, TP4057, MPU6050 onto single board
- Add screw terminals for LED ring, motor, buzzer
- Test 10 prototypes before scaling

---

**Step 3: Final Assembly**

**Options**:

**Option A**: You + 1-2 helpers (up to 50 bars)
- Assemble in your garage/warehouse
- Cost: Your time + $15/hour labor
- Capacity: 20-30 pucks/week

**Option B**: Contract manufacturer (50+ bars)
- Send them: Enclosures, PCBs, LEDs, batteries
- They assemble, QA, package
- Cost: $10-15 per puck assembly labor
- Find via: Maker's Row, ThomasNet

**MY RECOMMENDATION**:
- Months 4-6: DIY assembly (first 20-30 bars)
- Months 7-12: Contract manufacturer (bars 30-100)

---

## Month 5-6: Build Inventory & Hire Sales

### Month 5: Manufacture First Batch

**Timeline**:
```
Week 1-2: Injection molding (tooling done in Month 4)
Week 3: Receive first enclosures, inspect
Week 4: PCB assembly (order placed in Month 4)
Week 5-6: Final assembly
Week 7-8: QA testing, packaging
```

**First Batch**: 200 pucks (33 bar setups)
- Keep 5 sets for demos/replacements
- Sell/deploy 28 sets to bars

---

### Month 6: Hire Your First Sales Rep

**When**: Once you have 20-30 bars interested (waitlist from pre-sales)

**Who**: Part-time sales rep (commission only to start)

**Job Description**:
```
Role: Field Sales Rep (Bar Entertainment)
Pay: $500 base + 20% commission on first year revenue
Time: 20 hours/week

Responsibilities:
- Visit 20 bars/week (cold calls + demos)
- Close 4-6 new bars/month
- Support existing customers (check-ins, upsells)

Requirements:
- Experience in hospitality/bar industry
- Car + willing to drive 50-100 miles
- Comfortable with technology demos
- Self-motivated (commission-driven)
```

**Where to find**:
- Craigslist (commission-only sales jobs)
- LinkedIn (search "bar sales" or "hospitality sales")
- Ask your pilot bars if they know anyone

**Training**:
- Week 1: Shadow you on 5 demos
- Week 2: Run 5 demos while you watch
- Week 3: Go solo with daily check-ins

---

## Month 7-12: Scale to 100 Bars

### Marketing Playbook

**Channel 1: Direct Sales** (Primary)
- You + 1 sales rep visiting bars
- Goal: 2 new bars/week each = 16 bars/month
- Reach 100 bars in 6 months

**Channel 2: Trade Shows** (Awareness + Leads)
- **Nightclub & Bar Show** (March, Las Vegas)
  - Cost: $5k (booth + travel)
  - Expected: 100-200 leads, 10-20 sales
- **State Restaurant Association Shows** (varies by state)
  - Smaller, local, cheaper ($500-1500)

**Channel 3: Distribution Partnerships**
- Partner with bar equipment distributors
- Offer: 30% margin (they sell for $1,299, you wholesale for $909)
- Pro: They have existing bar relationships
- Con: Lower margin, less control

**Channel 4: Content Marketing**
- YouTube: "10 Ways to Increase Bar Sales on Slow Nights"
- SEO: Rank for "bar entertainment equipment"
- Instagram: Post videos of customers playing, tag bars

**Channel 5: Referrals**
- Offer bars $100 credit for each referral
- Ask happy bars to recommend you to friends

---

### Month 7-12 Milestones

**Month 7**:
- Deploy to 50 bars total (45 new + 5 pilots)
- Hire 2nd sales rep
- Revenue: $5,000/month (50 bars × $99)

**Month 8**:
- Deploy to 65 bars (15 new)
- Refine sales process based on data
- Revenue: $6,500/month

**Month 9**:
- Deploy to 80 bars (15 new)
- Attend first trade show
- Revenue: $8,000/month

**Month 10**:
- Deploy to 95 bars (15 new)
- Launch referral program
- Revenue: $9,500/month

**Month 11**:
- Hit 100 bars! 🎉
- Revenue: $10,000/month
- Manufacturing run #2 (next 300 pucks)

**Month 12**:
- Stabilize operations (support, replacements, upgrades)
- Revenue: $10,000-12,000/month (100-120 bars)
- Annual Run Rate: $120k-144k

---

# FINANCIAL PROJECTIONS (12 Months)

## Revenue Model (Lease)

```
Pricing: $99/month per bar (6 pucks)

Revenue by Month:
├─ Month 1-3: $0 (pilot phase, 50% off)
├─ Month 4: $500 (5 pilot bars × $99)
├─ Month 5: $2,000 (20 bars)
├─ Month 6: $3,500 (35 bars)
├─ Month 7: $5,000 (50 bars)
├─ Month 8: $6,500 (65 bars)
├─ Month 9: $8,000 (80 bars)
├─ Month 10: $9,500 (95 bars)
├─ Month 11: $10,000 (100 bars)
├─ Month 12: $10,000 (100 bars)
└─ TOTAL YEAR 1 REVENUE: $54,500

Monthly Recurring Revenue (MRR) by Month 12: $10,000
Annual Recurring Revenue (ARR): $120,000
```

---

## Cost Structure

```
COGS per Bar:
├─ 6× pucks @ $40 each = $240
├─ 1× Raspberry Pi server = $50
├─ Cables, packaging = $10
└─ TOTAL COGS: $300/bar

Gross Margin:
├─ Customer Lifetime Value (2 years): $99 × 24 = $2,376
├─ COGS: $300
├─ Gross Profit: $2,076
└─ Gross Margin: 87.4% 🔥

Operating Expenses (Monthly at 100 bars):
├─ Your salary: $4,000 (eventually)
├─ 2× Sales reps: $2,000 ($1k each base + commission)
├─ Server hosting (100 bars): $200
├─ Customer support (outsourced): $500
├─ Replacement parts (10% failure): $300
├─ Marketing: $1,000
└─ TOTAL OpEx: $8,000/month

EBITDA by Month 12:
├─ Revenue: $10,000
├─ OpEx: $8,000
└─ EBITDA: $2,000/month (20% margin)

After 12 months:
├─ Total Revenue: $54,500
├─ Total Costs: $60,000 (includes upfront manufacturing)
├─ Net Loss Year 1: -$5,500 (break-even in Month 13)
```

---

## Break-Even Analysis

```
Break-Even Point:
├─ Fixed costs: $50k (manufacturing setup)
├─ Variable costs: $300/bar
├─ Revenue: $99/month × 24 months = $2,376/bar
├─ Gross profit per bar: $2,076
└─ Break-even: $50k / $2,076 = 24 bars

You break even after deploying 24 bars (Month 6)
```

---

# KEY METRICS TO TRACK

## Customer Metrics

```
Acquisition:
├─ Bars contacted per week
├─ Demo conversion rate (demo → pilot)
├─ Pilot conversion rate (pilot → paying)
├─ Customer Acquisition Cost (CAC)
└─ Time to close (days from first contact → payment)

Engagement:
├─ Games played per bar per week
├─ Peak usage day/time
├─ Most popular games
└─ Customer satisfaction (bar manager NPS)

Retention:
├─ Monthly churn rate (bars that cancel)
├─ Lifetime Value (LTV)
├─ LTV:CAC ratio (should be >3:1)
└─ Renewal rate after first 3 months

Financial:
├─ Monthly Recurring Revenue (MRR)
├─ Annual Recurring Revenue (ARR)
├─ Gross Margin
├─ Customer Lifetime Value (LTV)
└─ Burn rate (cash spent per month)
```

---

# CONTINGENCY PLANS (What If Things Go Wrong?)

## Scenario 1: Low Demand (Can't Close 5 Pilots)

**Warning Signs**:
- Week 4: Only 10 bars agreed to demo (instead of 20)
- Week 6: Only 1 bar agreed to paid pilot (instead of 5)

**Actions**:
1. **Diagnose why**:
   - Price too high? (Test $49/month)
   - Product not compelling? (Add new games, better demo)
   - Wrong customer segment? (Try breweries, arcades, corporate cafeterias)

2. **Pivot options**:
   - B2C model: Sell direct to consumers ($199 home version)
   - Corporate events: Rent for parties ($500/night)
   - Different venue: Bowling alleys, arcades, movie theaters

3. **Kill criteria**: If <2 bars pay after 90 days → shut down, cut losses

---

## Scenario 2: High Demand, Can't Manufacture Fast Enough

**Warning Signs**:
- 20+ bars want to buy, you only have 2 sets built

**Actions**:
1. **Short-term**:
   - Build waitlist, take $500 deposits
   - Hire 2 friends to help assemble (pay $20/hour)
   - 3D print 24/7 (run 3 printers in parallel)

2. **Medium-term**:
   - Find local makerspace with 10+ printers (rent time)
   - Outsource assembly to local contract manufacturer

3. **Long-term**:
   - Raise capital ASAP (angel round)
   - Fast-track injection molding (pay premium for 4-week tooling)

---

## Scenario 3: Quality Issues (Pucks Breaking)

**Warning Signs**:
- 30%+ puck failure rate in first month
- Bars complaining about reliability

**Actions**:
1. **Immediate**:
   - Send replacement pucks within 24 hours (overnighted)
   - Diagnose root cause (battery? button? enclosure?)

2. **Short-term**:
   - Pause new deployments until fixed
   - Recall broken pucks, fix, re-test
   - Offer 1 month free to affected bars (apology)

3. **Long-term**:
   - Redesign problematic component
   - Add more rigorous QA testing
   - Consider extended warranty

---

## Scenario 4: Competitor Copies You

**Warning Signs**:
- Buzztime launches "Buzztime Pucks"
- Another startup builds similar product

**Actions**:
1. **Defense**:
   - File provisional patent (if you haven't already)
   - Lock in your 100 bars with annual contracts (discount for commitment)
   - Build brand loyalty (be the "original" TABLE WARS)

2. **Offense**:
   - Compete on customer service (you're faster, more attentive)
   - Add exclusive games they can't copy
   - Build network effects (cross-bar tournaments)

3. **Partnership**:
   - If competitor has distribution, offer to be acquired
   - License your tech to them (royalty deal)

---

# DECISION TREE SUMMARY

```
START: You have working prototype
│
├─ Month 1-3: Customer Discovery + Pilots
│   ├─ SUCCESS (5+ paid pilots) → Continue to Month 4-6
│   ├─ MIXED (2-4 pilots) → Iterate, try again
│   └─ FAILURE (<2 pilots) → Pivot or shut down
│
├─ Month 4-6: Validate ROI + Prep for Scale
│   ├─ SUCCESS (4+ bars renew, 30%+ sales lift) → Raise capital, scale
│   ├─ MIXED (2-3 renew, 10-20% lift) → Iterate, extend pilot
│   └─ FAILURE (<2 renew, <10% lift) → Pivot or shut down
│
├─ Month 7-12: Scale to 100 Bars
│   ├─ SUCCESS (80+ bars deployed, <10% churn) → Series A, scale to 1,000 bars
│   ├─ MIXED (40-80 bars, 10-20% churn) → Fix retention, then scale
│   └─ FAILURE (<40 bars, >30% churn) → Product-market fit not achieved, pivot
│
└─ Month 13+: Optimize & Expand
    ├─ Reach 500 bars (Year 2 goal)
    ├─ Expand to new markets/verticals
    ├─ Add new revenue streams (ads, sponsorships)
    └─ Consider acquisition offers
```

---

# YOUR ACTION PLAN (Start Monday)

## Week 1 Checklist

**Monday**:
- [ ] Create competitor research spreadsheet
- [ ] Research Buzztime, NTN, Pour Taproom, AMI Jukeboxes
- [ ] Call 3 bars that use Buzztime, interview them

**Tuesday**:
- [ ] Build list of 50 target bars in your city
- [ ] Create 1-page pitch deck
- [ ] Draft email template for cold outreach

**Wednesday**:
- [ ] Record 90-second demo video (iPhone is fine)
- [ ] Set up landing page (Carrd.co or Webflow)
- [ ] Connect email capture form (Airtable)

**Thursday**:
- [ ] Visit 5 bars in person (2-4pm)
- [ ] Demo pucks, pitch TABLE WARS
- [ ] Book follow-up demos for next week

**Friday**:
- [ ] Make 20 cold calls to bars
- [ ] Send 10 Instagram DMs to bars
- [ ] Order components for 2 pilot sets

**Weekend**:
- [ ] Assemble 2 pilot sets (12 pucks)
- [ ] Create pilot agreement template
- [ ] Prepare for Week 2 sales blitz

---

## Your North Star Metric

**The ONE number that matters most**:

### PAID PILOTS CLOSED

```
If you can close 5 paid pilots in 30 days:
✓ You've validated demand
✓ You've proven willingness to pay
✓ You have a business

If you can't:
✗ Product isn't compelling
✗ Price is wrong
✗ Customer segment is wrong
✗ Pivot or shut down
```

**Everything else is noise. Focus on this.**

---

# FINAL THOUGHTS

## What Makes This Succeed vs Fail

**Success Factors**:
1. **Speed** - Execute Week 1-4 customer discovery FAST (don't overthink)
2. **Listening** - Bar owners will tell you what they need (listen!)
3. **Iteration** - First version won't be perfect, improve weekly
4. **Persistence** - You'll hear 50 "no's" before 5 "yes's"
5. **Data** - Track everything, make decisions based on metrics

**Failure Factors**:
1. **Building in vacuum** - Not talking to customers early
2. **Premature scaling** - Manufacturing 1,000 pucks before validation
3. **Ignoring feedback** - Bars say price is too high, you ignore it
4. **No urgency** - Taking 6 months to do 30 days of work
5. **Sunk cost fallacy** - Continuing when data says pivot

---

## The Hardest Part

**It's not the technical stuff. You've already proven you can build.**

**The hard part is**:
- Cold calling 50 bars (rejection hurts)
- Hearing "no" 10 times in a row
- Admitting your product isn't working (if data shows it)
- Pivoting or shutting down if validation fails
- Hustling for 90 days straight with no guaranteed outcome

**But if you do this**:
- You'll know in 90 days if this is a business
- You'll avoid wasting 2 years building something nobody wants
- You'll learn more about sales/business than any course can teach
- You'll either have a profitable company or a valuable lesson

---

## You're Ready. Now Execute.

You have:
✅ Working prototype (firmware + hardware)
✅ Complete technical documentation
✅ Bar-ready enclosure design
✅ This business playbook

**What you need**:
- **30 days** to validate demand
- **$3-5k** for pilot inventory
- **Willingness to hear "no" 50 times**
- **Commitment to execute this plan**

**Start Monday. Not next month. Monday.**

**Week 1 = Customer discovery**
**Week 2 = Sales blitz**
**Week 3-4 = Close pilots**

**In 30 days, you'll know if this is real.**

Good luck. You've got this. 🚀

---

**Questions? Next steps?**

Once you've completed Week 1-4, come back and tell me:
1. How many bars you contacted
2. How many agreed to paid pilots
3. What objections you heard most
4. What surprised you

I'll help you iterate from there.
