austinscip/table-wars-puck/docs/legal/PATENT_BROADER_CLAIMS.md

# Broader Patent Claims - Interactive Gaming System

**Revision based on broader market positioning**

---

## IMPROVED PRODUCT DESCRIPTION

### **Primary Description (Broad - Use This):**

**"Interactive Competitive Gaming System"**

A networked system of portable electronic gaming devices that track physical interactions (shaking, tapping, movement patterns) through motion sensors, provide real-time visual and audio feedback via LEDs and sound, communicate wirelessly with mobile devices for control and with servers for score aggregation, and display competitive rankings across multiple simultaneous users on centralized displays. Designed for venues, events, and social gatherings where multiple participants engage in skill-based physical challenges.

---

## MARKET APPLICATIONS (Ranked by Potential)

### **Tier 1: Primary Markets (High Revenue Potential)**

#### 1. **Bars & Nightlife** (Original concept)
- Annual US revenue: ~$30B
- ~65,000 bars in US
- **Use case:** Gamification to increase dwell time and beverage sales
- **Value prop:** Customers stay longer, spend more, return for leaderboard competition

#### 2. **Restaurants (Full-Service)**
- Annual US revenue: ~$300B
- ~660,000 restaurants
- **Use case:** Wait time entertainment, kids' meals, special events
- **Value prop:** Reduce perceived wait time, family entertainment, differentiation

#### 3. **Corporate Events & Team Building**
- Annual corporate events spending: ~$500B globally
- **Use case:** Icebreakers, competition, team bonding
- **Value prop:** Measurable engagement, networking facilitation, memorable experiences

#### 4. **Entertainment Venues**
- Dave & Buster's, Main Event, bowling alleys, arcades
- **Use case:** Add portable games between fixed attractions
- **Value prop:** Flexible entertainment, table-based gaming, high margin

---

### **Tier 2: Secondary Markets (Growing Potential)**

#### 5. **Event Services & Rentals**
- Wedding receptions, corporate parties, conferences
- **Use case:** Interactive entertainment rental packages
- **Value prop:** Unique activity, icebreaker, measurable engagement

#### 6. **Fitness & Wellness**
- Gyms, CrossFit boxes, wellness retreats
- **Use case:** Reaction time training, fitness challenges, gamification
- **Value prop:** Data-driven fitness, competitive motivation, engagement

#### 7. **Education & STEM**
- Schools, museums, science centers, libraries
- **Use case:** Physics education (acceleration, force), game theory, coding clubs
- **Value prop:** Hands-on learning, engagement tracking, STEM appeal

#### 8. **Hospitality & Resorts**
- Hotels, cruise ships, resorts, vacation properties
- **Use case:** Pool/beach games, lobby entertainment, kids' clubs
- **Value prop:** Guest engagement, differentiation, dwell time

---

### **Tier 3: Niche Markets**

#### 9. **Consumer/Retail** (Home use)
- Direct-to-consumer sales
- **Use case:** House parties, family game nights, backyard BBQs
- **Value prop:** Reusable party entertainment, social media shareable

#### 10. **Therapy & Healthcare**
- Physical therapy, cognitive rehabilitation, senior living
- **Use case:** Reaction time assessment, motor skill training, engagement
- **Value prop:** Measurable progress, gamified therapy, patient motivation

---

## REVISED PATENT CLAIMS (Broader)

### **Claim 1 - Device (Broadest)**

A portable interactive device comprising:
- A housing adapted to be held by a user
- At least one motion sensor detecting movement in multiple axes
- A visual feedback system comprising a plurality of light-emitting elements
- A wireless communication module
- An input mechanism for user interaction
- A power source
- A processor configured to:
  - Detect physical interaction patterns via the motion sensor
  - Calculate performance metrics based on said patterns
  - Provide feedback via the visual system
  - Transmit said metrics via the wireless module

**Note:** No mention of "drinking," "bar," or "alcohol" - keeps it broad!

---

### **Claim 2 - System (Venue/Event Focus)**

A competitive gaming system for venues comprising:
- A plurality of portable interactive devices as in Claim 1
- A central server configured to receive performance data from said devices
- A display system configured to show aggregated performance data
- Wherein said devices operate simultaneously and independently
- Wherein said display shows real-time competitive rankings

**Applications:** Bars, restaurants, corporate events, fitness centers, etc.

---

### **Claim 3 - Method (Activity-Agnostic)**

A method of conducting a competitive physical activity comprising:
- Distributing portable devices to a plurality of participants
- Receiving an activity initiation command at each device
- Measuring physical interaction via motion sensors during a defined period
- Calculating performance metrics for each participant
- Transmitting said metrics to a centralized system
- Displaying comparative rankings of participants

**Note:** "Activity" not "game" - broader! Could be fitness, training, competition, etc.

---

### **Claim 4 - Dual Wireless Architecture**

The device of Claim 1, wherein the wireless communication module comprises:
- A first wireless protocol for receiving commands from a proximate control device
- A second wireless protocol for transmitting data to a remote server
- Wherein said protocols operate independently and simultaneously

**Novel aspect:** BLE for control, WiFi for data - unusual in battery-powered device

---

### **Claim 5 - Motion Detection Specifics**

The device of Claim 1, wherein the processor is configured to:
- Detect rapid oscillatory motion and calculate intensity metrics
- Detect discrete impact events and calculate frequency
- Detect continuous motion patterns and calculate endurance metrics
- Compare detected patterns against predetermined thresholds

**Applications:** Shake contests, tap speed, sustained activity, precision challenges

---

### **Claim 6 - Multi-Device Coordination**

A system comprising:
- Multiple devices as in Claim 1 operating within a common venue
- A server configured to synchronize activity timing across devices
- A display showing simultaneous performance data from multiple devices
- Wherein performance metrics from different devices are comparable

**Novel aspect:** Multi-puck networked competition with centralized coordination

---

## USAGE SCENARIOS (Show Versatility)

### **Scenario A: Bar Entertainment**
- Customer requests puck from bartender
- Plays speed-tap game against friend
- Scores appear on bar TV
- Winner gets bragging rights (optional: discount/free drink)

### **Scenario B: Corporate Icebreaker**
- Conference attendees receive pucks
- Compete in shake-intensity challenge
- Leaderboard shown on main screen
- Top 10 win prizes, all attendees network

### **Scenario C: Kids' Birthday Party**
- 10 kids each get a puck
- Play "hot potato" passing game
- Parents see scores on TV
- Winner gets extra cupcake

### **Scenario D: Gym Fitness Challenge**
- Gym members use pucks for reaction drills
- Coach monitors performance on tablet
- Monthly leaderboard for top performers
- Gamifies workout, increases engagement

### **Scenario E: STEM Education**
- Students use pucks to measure acceleration
- Learn about force, velocity, sensor technology
- Compete to achieve specific G-force readings
- Data exported for analysis

### **Scenario F: Wedding Reception**
- Guests play during cocktail hour
- Icebreaker for guests who don't know each other
- Bride/groom appear on leaderboard
- Photo ops with winning table

---

## COMPETITIVE POSITIONING

### **What Makes This Different from Existing Products:**

| Product Category | Limitation | Our Advantage |
|---|---|---|
| **Arcade games** | Fixed location, high cost | Portable, affordable, rental-ready |
| **Wii/PlayStation** | Requires TV per player, home use | Standalone, venue-optimized, multi-user |
| **Topgolf** | Sport-specific, massive infrastructure | Activity-agnostic, minimal setup |
| **Electronic darts** | Wall-mounted, single game type | Portable, 10+ game types |
| **Board games** | No tracking, manual scoring | Automated scoring, leaderboards |
| **Fitness trackers** | Individual use, no competition | Multi-user competitive, real-time |

---

## KEY MESSAGING FOR PATENT

### **Don't Say:**
- ❌ "Drinking game device"
- ❌ "Bar entertainment only"
- ❌ "Beer pong replacement"
- ❌ "Alcohol-related"

### **Do Say:**
- ✅ "Interactive competitive gaming system"
- ✅ "Networked physical activity tracking"
- ✅ "Multi-user engagement platform"
- ✅ "Portable venue entertainment system"
- ✅ "Social competitive device network"

---

## REVENUE MODELS (Shows Versatility)

### **B2B (Business-to-Business):**
1. **Venue Sales** - Sell/lease puck sets to bars, restaurants, gyms
2. **Event Rentals** - Rent to corporate event planners, wedding venues
3. **White Label** - License to Dave & Buster's, Chuck E. Cheese, etc.
4. **Subscription** - Monthly fee for software updates, leaderboards
5. **Per-Game Fees** - Revenue share on game plays

### **B2C (Business-to-Consumer):**
1. **Direct Sales** - Sell consumer version for home parties
2. **Subscription Games** - Monthly game pack DLC
3. **Tournament Entry** - Fee for online tournaments

### **Licensing:**
1. **Technology Licensing** - License dual-wireless + motion tech
2. **Patent Licensing** - License to competitors (defensive)
3. **Brand Licensing** - License "Table Wars" name to other products

---

## INTERNATIONAL POTENTIAL

### **Why This Matters Globally:**

**Market Size:**
- 🇺🇸 USA: 65K bars, 660K restaurants
- 🇪🇺 Europe: 3M+ hospitality venues
- 🇨🇳 China: Massive event/hospitality growth
- 🇯🇵 Japan: Gaming culture, tech adoption
- 🇦🇺 Australia: Strong bar/pub culture

**Patent Strategy:**
- File **PCT (Patent Cooperation Treaty)** - covers 150+ countries
- Prioritize: US, EU, China, Japan, South Korea, Australia
- Cost: ~$30K for international filings (do after provisional)

---

## TRADEMARK STRATEGY (Beyond Patent)

### **Protectable Brand Elements:**

**Name:**
- "Table Wars" - Main brand
- Alternative: "CompeteNow", "PuckBattles", "SkillPucks"

**Taglines:**
- "Turn Any Table Into an Arena"
- "Compete. Connect. Conquer."
- "Where Every Moment Counts"

**Product Line Names:**
- "Pro Series" (venue/commercial grade)
- "Party Pack" (consumer home use)
- "Kids Edition" (family-friendly)
- "Fitness Tracker" (gym/wellness)

---

## DESIGN PATENT POTENTIAL

### **Protectable Design Elements:**

1. **Circular puck form factor** with specific proportions
2. **LED ring arrangement** (16 lights in circular pattern)
3. **Button placement** on top surface
4. **Overall ornamental design** of assembled puck
5. **Case design** with specific curves/edges

**Why Design Patent:**
- ✅ Cheaper than utility patent (~$2-4K)
- ✅ Harder to design around (protects look/feel)
- ✅ Prevents knockoffs with similar appearance
- ✅ 15-year protection (vs. 20 for utility)

---

## TRADE SECRET CONSIDERATIONS

### **What to Patent vs. Keep Secret:**

**Patent (Public Disclosure Required):**
- ✅ Dual wireless architecture
- ✅ Multi-device networking
- ✅ Motion detection methods
- ✅ System-level claims
- ✅ General game mechanics

**Keep as Trade Secret (Don't Disclose):**
- 🔒 Specific algorithms (shake intensity calculation)
- 🔒 Server-side anti-cheat validation
- 🔒 Battery optimization techniques
- 🔒 Manufacturing processes
- 🔒 Supplier relationships
- 🔒 Detailed firmware implementation

**Strategy:** Patent the "what," keep secret the "how" (specific implementation)

---

## SUMMARY: BROADER IS BETTER

### **Original Pitch:**
"Wireless drinking game puck for bars"

### **Improved Pitch:**
"Networked interactive gaming system for social venues and competitive events, enabling real-time tracked physical challenges across multiple simultaneous users with centralized scoring and display."

**Benefits of Broader Claims:**
- ✅ Harder to design around
- ✅ More market applications
- ✅ Higher valuation (bigger TAM)
- ✅ Licensing opportunities
- ✅ Defensive protection
- ✅ Future-proof (new uses covered)

---

## ACTION ITEMS

**For Your Lawyer:**
1. ✅ Use broader "interactive gaming system" language
2. ✅ Emphasize multi-venue applications
3. ✅ Don't limit to "drinking" or "bars" in claims
4. ✅ Include education, fitness, corporate use cases
5. ✅ Patent system-level (not just device)

**For Your Business:**
1. ✅ Market to bars first (fastest adoption)
2. ✅ Expand to restaurants, events, corporate
3. ✅ Create different "editions" (Pro, Party, Kids, Fitness)
4. ✅ White label for major entertainment brands
5. ✅ International expansion (EU, Asia markets)

---

**Bottom Line:** This isn't just a "drinking game" - it's a **social competitive gaming platform** with applications across hospitality, events, fitness, education, and entertainment. Patent it broadly to capture all these markets! 🚀
