austinscip/table-wars-puck/server/RENAMED_GAMES_LEGAL.md

# LEGALLY SAFE GAME NAMES FOR TABLE WARS

**Legal Issue:** Many game names were directly copied from Jackbox Party Packs (Trivia Murder Party, Fibbage, Quiplash, etc.)

**Solution:** Rename all games with original names while keeping the mechanics (game mechanics can't be copyrighted, but names/branding can)

---

## PROBLEMATIC NAMES → NEW NAMES

### Core Trivia Games

1. ~~**Trivia Murder Party**~~ → **DEATH QUIZ**
   - Same mechanics: Horror trivia with mini-games for wrong answers
   - Original name, different branding

2. **Category Royale** ✅ (SAFE - generic name)

3. **Speed Pyramid** ✅ (SAFE - generic name)

4. **Fact or Crap** ✅ (SAFE - generic phrase)

5. ~~**You Don't Know Jack: Puck Edition**~~ → **SCREW THE CREW**
   - Same mechanics: Force opponents to answer hard questions
   - Original name, no YDKJ reference

6. **Multiplier Madness** ✅ (SAFE - generic name)

7. ~~**The Wheel of Enormous Proportions**~~ → **SPIN TO WIN**
   - Same mechanics: Answer trivia then spin for multiplier
   - Generic name

8. ~~**Guesspionage**~~ → **PERCENTAGE PANIC**
   - Same mechanics: Guess survey percentages
   - Original name

9. **Trivia Gauntlet** ✅ (SAFE - generic name)

10. ~~**Timejinx**~~ → **YEAR HUNTER**
    - Same mechanics: Guess historical years
    - Original name

### Lie Detection & Deception

11. ~~**Fibbage: Puck Lies**~~ → **LIE DETECTOR**
    - Same mechanics: Create fake answers, vote for truth
    - Original name

12. ~~**Survive the Internet**~~ → **QUOTE TWIST**
    - Same mechanics: Twist quotes out of context
    - Original name

13. ~~**Split the Room**~~ → **50/50 SPLIT**
    - Same mechanics: Create divisive scenarios
    - Generic name

14. ~~**Hypnotorious**~~ → **SPOT THE ODD**
    - Same mechanics: Find the outlier player
    - Original name

15. ~~**Suspectives**~~ → **ACCUSATION**
    - Same mechanics: Social deduction murder mystery
    - Generic name

16. ~~**Fakin' It: Puck Edition**~~ → **FAKE OUT**
    - Same mechanics: One player fakes actions
    - Original name

17. ~~**Weapons Drawn**~~ → **MURDER MYSTERY PUCK**
    - Same mechanics: Deduce murderer by signature
    - Original name

### Word & Creativity

18. ~~**Quiplash: Puck Wars**~~ → **BATTLE OF WITS**
    - Same mechanics: Funniest answer wins
    - Original name

19. ~~**Mad Verse City: Rap Battle**~~ → **RAP ROYALE**
    - Same mechanics: Fill-in-the-blank rap lyrics
    - Original name

20. ~~**Joke Boat**~~ → **PUNCHLINE WARS**
    - Same mechanics: Complete joke setups
    - Original name

21. ~~**Dictionarium**~~ → **DEFINE THIS**
    - Same mechanics: Define fake words
    - Generic name

22. ~~**FixyText**~~ → **AUTOCORRECT CHAOS**
    - Same mechanics: Chaotic text injection
    - Original name

23. ~~**Word Spud**~~ → **WORD CHAIN**
    - Same mechanics: Word association
    - Generic name

24. ~~**Blather 'Round**~~ → **CLUE GIVER**
    - Same mechanics: Describe with limited vocabulary
    - Original name

25. ~~**Nonsensory**~~ → **RATE IT**
    - Same mechanics: Rate descriptions 1-10
    - Generic name

### Gambling & Risk

26. **All or Nothing** ✅ (SAFE - common phrase)

27. **Russian Roulette Trivia** ✅ (SAFE - generic)

28. **Double or Nothing** ✅ (SAFE - common phrase)

29. ~~**Bracketeering**~~ → **BRACKET BATTLE**
    - Same mechanics: Tournament voting
    - Generic name

30. **Lucky Streak** ✅ (SAFE - common phrase)

### Physical & Skill Hybrid

31. **Shake Attack** ✅ (SAFE - generic)

32. **Screw Your Neighbor** ✅ (SAFE - common card game name)

33. **Hostage Trivia** ✅ (SAFE - generic)

34. **Chaos Round** ✅ (SAFE - generic)

35. **Perfect Timing** ✅ (SAFE - generic)

36. **Balance Master** ✅ (SAFE - generic)

37. **Spin Zone** ✅ (SAFE - generic)

### Team & Cooperative

38. ~~**The Poll Mine**~~ → **POLL PREDICTIONS**
    - Same mechanics: Guess poll rankings
    - Original name

39. ~~**Devils and the Details**~~ → **FAMILY CHAOS**
    - Same mechanics: Cooperative chores vs selfish tasks
    - Original name

40. ~~**Push the Button**~~ → **FIND THE IMPOSTOR**
    - Same mechanics: Find alien among crew
    - Generic name (also avoids Among Us territory)

41. ~~**Legends of Trivia**~~ → **QUEST MASTERS**
    - Same mechanics: Cooperative RPG trivia
    - Original name

---

## SUMMARY OF CHANGES

**Total Games:** 41
**Safe Names (No Change):** 15 games
**Renamed Games:** 26 games

**Legal Basis:**
- Game mechanics ✅ CANNOT be copyrighted
- Specific names/branding ❌ CAN be trademarked
- Our approach: Same mechanics, 100% original names

**Example:**
- ❌ "Fibbage: Puck Lies" (Jackbox trademark)
- ✅ "Lie Detector" (generic name, same mechanics)

**All renamed games use:**
- Generic descriptive names (Spin to Win, Year Hunter)
- Common phrases (All or Nothing, Double or Nothing)
- Original creative names (Death Quiz, Screw the Crew)

**No Jackbox references** in any game name.

---

## UPDATED 41 GAME LIST (LEGAL NAMES ONLY)

### Core Trivia (10)
1. Death Quiz
2. Category Royale
3. Speed Pyramid
4. Fact or Crap
5. Screw the Crew
6. Multiplier Madness
7. Spin to Win
8. Percentage Panic
9. Trivia Gauntlet
10. Year Hunter

### Lie Detection (7)
11. Lie Detector
12. Quote Twist
13. 50/50 Split
14. Spot the Odd
15. Accusation
16. Fake Out
17. Murder Mystery Puck

### Word & Creativity (8)
18. Battle of Wits
19. Rap Royale
20. Punchline Wars
21. Define This
22. Autocorrect Chaos
23. Word Chain
24. Clue Giver
25. Rate It

### Gambling & Risk (5)
26. All or Nothing
27. Russian Roulette Trivia
28. Double or Nothing
29. Bracket Battle
30. Lucky Streak

### Physical & Skill (7)
31. Shake Attack
32. Screw Your Neighbor
33. Hostage Trivia
34. Chaos Round
35. Perfect Timing
36. Balance Master
37. Spin Zone

### Team & Cooperative (4)
38. Poll Predictions
39. Family Chaos
40. Find the Impostor
41. Quest Masters

---

**Next Steps:**
1. Update database game_types table with new names
2. Update all documentation (YDKJ_41_GAMES.md, BUSINESS_OVERVIEW, etc.)
3. Update trivia_game_engines.py with new class names
4. Consult with IP attorney for final review before launch

**Legal Budget:** $5,000-10,000 for provisional patent + trademark search
