austinscip/table-wars-puck/docs/archive/ALL_37_GAMES_REFERENCE.md

# 🎮 TABLE WARS - ALL 37 GAMES QUICK REFERENCE

## 📋 COMPLETE GAME LIST

| # | Game Name | Category | Duration | Mechanic | Bar Appeal |
|---|---|---|---|---|---|
| 1 | ⚡ Speed Tap Battle | Speed | 10s | Button mashing | High |
| 2 | 🔥 Shake Duel | Physical | 10s | Shake intensity | High |
| 3 | 🔴 Red Light Green Light | Skill | 30s | Freeze control | Medium |
| 4 | 🎯 LED Chase Race | Timing | 45s | LED tracking | Medium |
| 5 | ⚔️ Color Wars | Strategy | 60s | Territory defense | Medium |
| 6 | 🌈 Rainbow Roulette | Luck | 30s | Color matching | Medium |
| 7 | 💣 Visual Bomb Countdown | Social | 20s | Pass the bomb | High |
| 8 | 🧠 Simon Says LED | Memory | 60s | Pattern recall | Medium |
| 9 | 💣 Hot Potato | Social | 30s | Hot potato | High |
| 10 | ⚡ Drunk Duel | Reaction | 20s | 1v1 speed test | Very High |
| 11 | 💀 Last Tap Standing | Timing | 60s | Tap before red | Medium |
| 12 | 💪 Hammer Time | Physical | 30s | Peak strength | High |
| 13 | 🎰 Bar Roulette | Social | 30s | Dare spinner | Very High |
| 14 | 🧘 Hold Your Nerve | Skill | 60s | Stay still | Medium |
| 15 | 👊 Slap Battle | Reaction | 30s | Reaction slap | Very High |
| 16 | 🍺 Chug Timer | Drinking | 30s | Timed chug | Very High |
| 17 | 🔥 Pressure Cooker | Endurance | 60s | Resist button | Medium |
| 18 | 🍻 Power Hour | Drinking | 300s | Timed drinking | Very High |
| 19 | 🎲 Dare Roulette | Social | 30s | Dare intensity | Very High |
| 20 | 🎯 Bullseye | Skill | 45s | Spin accuracy | Medium |
| 21 | 🎤 Karaoke Judge | Social | 30s | Performance | High |
| 22 | 🎴 Wild Card | Social | 20s | Random command | Medium |
| 23 | 🎰 Lucky Seven | Luck | 30s | Dice rolling | High |
| 24 | 🔊 Volume Wars | Physical | 10s | Scream contest | Very High |
| 25 | 🥃 Shot Roulette | Drinking | 30s | Shot order | Very High |
| 26 | ⚖️ Balance Master | Skill | 20s | Balance test | Medium |
| 27 | 🌀 Spin Master | Physical | 45s | Spin speed | Medium |
| 28 | ⚡ Lightning Round | Multi | 45s | Command switching | High |
| 29 | 🎵 Beat Master | Rhythm | 120s | Rhythm precision | Medium |
| 30 | 💰 Double or Nothing | Gambling | 120s | Risk/reward | Very High |
| 31 | 🥊 Combo Breaker | Skill | 150s | Input combos | Medium |
| 32 | 🚫 Lockout | Reaction | 120s | Penalty avoidance | High |
| 33 | 🎯 Precision Strike | Timing | 150s | Perfect timing | Medium |
| 34 | 🏃 Gauntlet Mode | Multi | 180s | 5 challenges | High |
| 35 | 💀 Russian Roulette | Gambling | 150s | Risk management | Very High |
| 36 | 🏃 Marathon Mode | Endurance | 300s+ | Consistency | Medium |
| 37 | 🔄 Mirror Match | Memory | 120s | Pattern recognition | Medium |

---

## 📊 CATEGORY BREAKDOWN

### **By Game Type:**
- **Speed/Reaction:** 8 games (1, 2, 10, 11, 12, 15, 24, 32)
- **Timing/Precision:** 6 games (4, 6, 11, 20, 26, 33)
- **Memory/Pattern:** 3 games (8, 31, 37)
- **Rhythm:** 2 games (29, 36)
- **Physical:** 5 games (2, 12, 24, 27, 3)
- **Social/Party:** 7 games (7, 9, 13, 19, 21, 22, 25)
- **Drinking:** 3 games (16, 18, 25)
- **Gambling/Risk:** 5 games (13, 19, 23, 30, 35)
- **Skill/Strategy:** 5 games (5, 14, 31, 33, 34)
- **Multi-Mechanic:** 3 games (28, 34, 5)

### **By Bar Appeal:**
- **Very High (10+ games):** 10, 13, 15, 16, 18, 19, 24, 25, 30, 35
- **High (13 games):** 1, 2, 7, 9, 12, 21, 23, 28, 32, 34
- **Medium (14 games):** 3, 4, 5, 6, 8, 11, 14, 17, 20, 22, 26, 27, 29, 31, 33, 36, 37

### **By Duration:**
- **Quick (< 30s):** 12 games
- **Medium (30-120s):** 18 games
- **Long (120s+):** 7 games

---

## 🎯 GAME RECOMMENDATIONS BY SITUATION

### **Late Night Crowd (Drunk-Friendly):**
1. 👊 Slap Battle (15)
2. ⚡ Drunk Duel (10)
3. 🍺 Chug Timer (16)
4. 🔊 Volume Wars (24)
5. 🥃 Shot Roulette (25)
6. 🎲 Dare Roulette (19)
7. 💀 Russian Roulette (35)
8. 💰 Double or Nothing (30)

### **Competitive Players:**
1. ⚡ Speed Tap Battle (1)
2. 🎵 Beat Master (29)
3. 🥊 Combo Breaker (31)
4. 🎯 Precision Strike (33)
5. 🏃 Marathon Mode (36)
6. 🏃 Gauntlet Mode (34)
7. 💪 Hammer Time (12)

### **Social Groups:**
1. 🎰 Bar Roulette (13)
2. 💣 Hot Potato (9)
3. 🎴 Wild Card (22)
4. 🎤 Karaoke Judge (21)
5. 🎲 Dare Roulette (19)
6. 💣 Visual Bomb (7)

### **Quick Games (Bar Traffic):**
1. ⚡ Speed Tap (1) - 10s
2. 🔥 Shake Duel (2) - 10s
3. 🔊 Volume Wars (24) - 10s
4. ⚡ Drunk Duel (10) - 20s
5. ⚖️ Balance Master (26) - 20s

### **Revenue Drivers:**
1. 🍻 Power Hour (18) - $5/table rental
2. 🍺 Chug Timer (16) - Sells drinks
3. 🥃 Shot Roulette (25) - Group shots
4. 💰 Double or Nothing (30) - Betting appeal
5. 💀 Russian Roulette (35) - Betting appeal

---

## 🏆 TOP 10 "SIGNATURE" GAMES

**If you only demo 10 games to a bar owner, show these:**

1. **⚡ Lightning Round (28)** - Shows ALL hardware capabilities
2. **💰 Double or Nothing (30)** - Crowd screaming guaranteed
3. **👊 Slap Battle (15)** - Viral video gold
4. **🍺 Chug Timer (16)** - Direct revenue driver
5. **💀 Russian Roulette (35)** - Suspense + drama
6. **🎵 Beat Master (29)** - Unique rhythm mechanic
7. **⚡ Drunk Duel (10)** - Classic bar competition
8. **🎰 Bar Roulette (13)** - Social icebreaker
9. **🏃 Gauntlet Mode (34)** - Shows game variety
10. **🥃 Shot Roulette (25)** - Instant bar culture fit

---

## 📱 DISPLAY SCREEN TEXT (For Bar TVs)

### **Game Announcements:**

```
GAME 28: LIGHTNING ROUND
Follow the colored commands!
Green = TAP 3X
Red = SHAKE
Blue = FREEZE
Yellow = HOLD BUTTON
```

```
GAME 30: DOUBLE OR NOTHING
TAP to BANK your points
or WAIT to double (risk BUST!)
```

```
GAME 35: RUSSIAN ROULETTE
TAP = advance (+100 pts)
HOLD 3s = BANK points
One chamber is loaded... 💀
```

---

## 🎮 CONTROLS CHEAT SHEET

### **Basic Controls:**
- **TAP:** Quick press and release
- **HOLD:** Press and hold for 2-3 seconds
- **DOUBLE TAP:** Two quick taps
- **SHAKE:** Violent shaking motion
- **FREEZE:** Don't move at all
- **SLAP:** Hard quick hit

### **LED Color Meanings:**
- **GREEN:** Go / Correct / Safe
- **RED:** Stop / Wrong / Danger
- **BLUE:** Freeze / Hold Still
- **YELLOW:** Caution / Ready
- **CYAN:** Active / In Progress
- **MAGENTA:** Game Over
- **WHITE:** Perfect / Target

---

## 💡 GAME MASTERY TIPS

### **Speed Tap Battle (1):**
- Use two fingers alternating
- Tap lightly, not hard
- Stay relaxed

### **Beat Master (29):**
- Close your eyes and feel the rhythm
- Don't tap early trying to "catch up"
- Let the LED guide you

### **Double or Nothing (30):**
- Bank at 400 points (2 doubles)
- Never wait past 800 points
- Trust your gut on bust timing

### **Combo Breaker (31):**
- Visualize the combo before executing
- Practice hold duration (full 2 seconds)
- Don't rush between moves

### **Russian Roulette (35):**
- Bank at position 3 (50% loaded)
- Only go to 5+ if you're drunk
- Chamber 0 is never loaded (advance once for free)

### **Marathon Mode (36):**
- Count in your head: "one Mississippi"
- Tap on "pi" of Mississippi
- Don't focus on the LED, feel the rhythm

### **Precision Strike (33):**
- Watch the sweep LED, not the target
- Late rounds: predict where it will be
- Tap slightly before you think (reaction delay)

---

## 🔧 TROUBLESHOOTING

### **Game doesn't start:**
- Check button press
- Verify skip button works
- Reboot puck

### **Game feels too hard:**
- Some games have progressive difficulty
- Marathon/Beat Master start easy
- Gauntlet gives 3 attempts

### **Game feels too easy:**
- Later levels increase difficulty
- Precision Strike gets very hard
- Marathon narrows tolerance over time

### **Don't understand a game:**
- Watch LED colors (they guide you)
- Serial monitor shows instructions
- Skip to next game and try later

---

## 📈 STATS TO TRACK

### **For Each Game:**
- Times played
- Average score
- High score
- Completion rate
- Average duration

### **For The Puck:**
- Total games played
- Most popular game
- Least popular game
- Average session length
- Battery cycles

### **For The Bar:**
- Revenue per puck per week
- Customer engagement time
- Drink sales increase %
- Social media mentions
- Return customer rate

---

## 🎊 THE COMPLETE PACKAGE

**37 games. Every mechanic covered. Every player type satisfied.**

- ✅ **Speed demons** → Lightning Round, Speed Tap
- ✅ **Rhythm gamers** → Beat Master, Marathon
- ✅ **Gamblers** → Russian Roulette, Double or Nothing
- ✅ **Precision players** → Precision Strike, Bullseye
- ✅ **Social butterflies** → Dare Roulette, Wild Card
- ✅ **Endurance athletes** → Marathon, Gauntlet
- ✅ **Combo masters** → Combo Breaker
- ✅ **Party animals** → Slap Battle, Volume Wars
- ✅ **Strategists** → Color Wars, Hold Your Nerve
- ✅ **Drinkers** → Chug Timer, Power Hour, Shot Roulette

**No player left behind. No moment left boring. No bar left unimpressed.**

---

**Total Games:** 37
**Total Duration:** ~111 minutes
**Total Awesomeness:** 💯

**Now go upload and dominate.** 🚀🎮🍻
