austinscip/table-wars-puck/docs/archive/ALL_97_GAMES_MASTER_LIST.md

# 🎮 ALL 97 TABLE WARS GAMES - COMPLETE MASTER LIST

**Total: 97 Games**
- 51 ESP32 Skill Games (1-51)
- 5 TV-Integrated Games (52-56)
- 41 YDKJ-Style Trivia Games (57-97)

---

## 🎯 ESP32 SKILL GAMES (1-51)

### 1. ⚡ SPEED TAP BATTLE
- Mash button as fast as possible for 10 seconds
- Each tap lights up an LED
- Typical score: 200-400 points
- Pro score: 600+ points
- Pure dopamine rush, competitive

### 2. 🔥 SHAKE DUEL
- Shake puck as violently as possible for 10 seconds
- More shake intensity = more red LEDs
- Typical score: 500-1500 points
- Beast mode: 2000+ points
- Extremely viral, hilarious to watch

### 3. 🔴 RED LIGHT GREEN LIGHT
- Shake when GREEN, FREEZE when RED
- 5 rounds total
- Movement during RED = lose points
- Start with 1000 points
- Squid Game reference, builds tension

### 4. 🎯 LED CHASE RACE
- Press button when moving LED reaches target
- 10 rounds, increasing speed
- Direct hit: +100 points, miss: -50
- Tests reflexes and timing
- Visual + motor coordination

### 5. ⚔️ COLOR WARS
- Defend your team color territory
- Tap button fast to defend (10+ taps = win)
- 10 rounds total
- Win = gain territory, lose = lose territory
- Tribal identity, territorial conquest

### 6. 🌈 RAINBOW ROULETTE
- Stop spinning rainbow on target color
- 5 rounds
- Exact match: +200 (JACKPOT!)
- Part skill, part luck
- Beautiful rainbow effect, gambling psychology

### 7. 💣 VISUAL BOMB COUNTDOWN
- Pass the bomb before it explodes
- LEDs count down visually
- Press button to "pass" bomb
- 3 rounds
- Hot potato mechanic, visual tension

### 8. 🧠 SIMON SAYS LED
- Remember and repeat LED pattern
- Patterns get longer (1-5 LEDs)
- Miss = game over
- Max score: 1500 points (all levels)
- Classic memory game, progressively harder

### 9. 💣 HOT POTATO
- Hold puck while timer counts down
- Pass to another player before explosion
- Random timer (5-15 seconds)
- Last holder loses points
- Multi-player chaos, social pressure

### 10. ⚡ DRUNK DUEL
- Two players shake simultaneously
- Harder shake = more points
- 15 second duel
- Real-time LED comparison
- Head-to-head competition

### 11. 💀 LAST TAP STANDING
- Tap battle royale - last player tapping wins
- Must tap every 2 seconds or eliminated
- Up to 6 players
- Escalating pressure
- Endurance + focus test

### 12. 💪 HAMMER TIME
- Shake as hard as possible in 5 seconds
- Peak force measured
- "Break the hammer" visual effect
- Carnival strength test vibes
- Physical exertion, instant feedback

### 13. 🎰 BAR ROULETTE
- LED spins, stop on color for reward
- Different colors = different challenges
- RED = drink, GREEN = give drink, BLUE = truth/dare
- Random outcomes
- Social drinking game integration

### 14. 🧘 HOLD YOUR NERVE
- Hold puck perfectly still for 30 seconds
- Accelerometer detects any movement
- Movement = lose points
- Meditation meets drunk challenge
- Tests focus and steadiness

### 15. 👊 SLAP BATTLE
- Slap puck on table as hard as possible
- Peak impact measured by accelerometer
- 3 slaps per round
- Hardest slap wins
- Physical comedy, bar-safe violence

### 16. 🍺 CHUG TIMER
- Start timer when drinking begins
- Stop when done
- Leaderboard for fastest chug
- Automatic time tracking
- Drinking game essential

### 17. 🔥 PRESSURE COOKER
- Score builds as you hold button
- Random "explosion" time (5-30s)
- Hold too long = lose everything
- Release early = keep points
- Risk/reward gambling mechanic

### 18. 🍻 POWER HOUR MANAGER
- 60 minute timer with shot alerts
- Buzzer every 60 seconds = take shot
- Tracks total shots consumed
- LED countdown between shots
- Classic drinking game automation

### 19. 🎲 DARE ROULETTE
- Spin LED wheel to select dare level
- 1-5 difficulty scale
- Group decides dare based on level
- Can refuse for point penalty
- Social pressure + gambling

### 20. 🎯 BULLSEYE
- Tap button at EXACT moment LED hits target
- 10 rounds, variable LED speeds
- Perfect timing = 200 points
- Within 100ms = 100 points
- Precision timing challenge

### 21. 🎤 KARAOKE JUDGE
- Sing along to karaoke
- Shake puck to beat = rhythm score
- Measures consistency with rhythm
- Visual beat indicator on LEDs
- Music + motion integration

### 22. 🎴 WILD CARD
- Random game selected each round
- 5 mini-challenges
- Variety test of all skills
- Unpredictable
- Keeps players on toes

### 23. 🎰 LUCKY SEVEN
- Shake puck = roll virtual dice
- Get exactly 7 = jackpot (500pts)
- Over/under scoring
- 10 rolls
- Pure luck, gambling appeal

### 24. 🔊 VOLUME WARS
- Measure ambient noise level via shake sensor
- Louder environment = higher score
- "Make the bar scream" challenge
- 30 second window
- Crowd energy amplifier

### 25. 🥃 SHOT ROULETTE
- Spin for shot type assignment
- RED = whiskey, BLUE = vodka, etc.
- LED lands on color = your shot
- Social drinking selector
- Removes decision fatigue

### 26. ⚖️ BALANCE MASTER
- Balance puck on various surfaces
- Must stay within 5° tilt for 30s
- Progressive difficulty (hand, head, foot)
- Meditation + physical control
- Drunk people WILL fail hilariously

### 27. 🌀 SPIN MASTER
- Spin puck as fast as possible
- Gyroscope measures RPM
- Faster spin = more points
- 10 second window
- Fidget spinner vibes

### 28. ⚡ LIGHTNING ROUND
- Random rapid-fire challenges
- 10 seconds each
- Mix of tap, shake, freeze
- No time to think
- Chaotic energy

### 29. 🎵 BEAT MASTER
- Match the beat pattern shown by LEDs
- Tap button in rhythm
- Accuracy score (0-100%)
- 8 beat sequences
- Rhythm game core mechanic

### 30. 💰 DOUBLE OR NOTHING
- Bet current score on coin flip
- Shake puck = flip
- 50/50 win/lose all
- Up to 5 flips
- Degenerate gambling

### 31. 🥊 COMBO BREAKER
- Perform tap + shake combos
- Specific sequences shown on LEDs
- "TAP-SHAKE-TAP" pattern matching
- 10 combos, increasing difficulty
- Fighting game mechanics

### 32. 🚫 LOCKOUT
- First to tap button after GO signal wins
- Random delay (1-5 seconds)
- Too early = lockout penalty (-200)
- Reaction time test
- Buzzer game show vibes

### 33. 🎯 PRECISION STRIKE
- Hold button for EXACTLY 3.00 seconds
- Display shows your time
- Within 0.1s = perfect (500pts)
- Within 0.5s = good (200pts)
- Timing precision challenge

### 34. 🏃 GAUNTLET MODE
- Survive all challenges back-to-back
- No breaks between games
- Cumulative score
- 5 random mini-games
- Endurance test

### 35. 💀 RUSSIAN ROULETTE
- 6 virtual chambers, 1 loaded
- Shake to "pull trigger"
- Loaded chamber = explosion, lose all
- Safe = +200 per round
- Gambling + suspense

### 36. 🏃 MARATHON MODE
- 5 minute continuous play
- Score accumulates entire time
- Mixture of all game types
- Stamina + variety
- Long-form challenge

### 37. 🔄 MIRROR MATCH
- Copy the LED pattern exactly
- Timing AND position must match
- 5 patterns of increasing complexity
- Perfect copy = bonus multiplier
- Precision + memory

### 38. ⏱️ PERFECT HOLD
- Hold button for exact duration shown
- Target changes each round (1s, 2s, 3s)
- Must release at perfect moment
- Internal clock accuracy test
- Zen + precision

### 39. 🎯 COUNTDOWN SNIPER
- Wait for countdown to reach ZERO
- Tap at exact 0.00 moment
- Too early/late = miss
- Visual countdown on LEDs
- Anticipation + timing

### 40. 🔗 REACTION CHAIN
- Tap button as fast as possible
- Must tap within 500ms of last tap
- Chain breaks if too slow
- Longest chain wins
- Sustained focus test

### 41. 🗡️ JUDAS MODE
- Social deduction game
- Everyone shakes to contribute to pot
- One player secretly chosen as JUDAS
- Judas can STEAL pot (hold button 3s)
- Stealing = 2x points if successful
- If JUDAS doesn't steal = everyone splits pot
- Among Us meets hot potato

### 42. 🦆 DRUNK DUCK HUNT
- Physical slapping game
- SLAP/SHAKE when you hear "QUACK!"
- DON'T hit when you hear "HONK!" (goose)
- 12 rounds
- Hit duck = +100, hit goose = -200
- 300ms reaction window
- Hilarious when drunk

### 43. 🥊 SUCKER PUNCH
- Western standoff reaction game
- Hands ready over puck
- Yellow = get ready (2s)
- Orange = steady (1-4s random)
- GREEN = GRAB NOW!
- <100ms = 500 points
- 5 rounds total
- Tense, competitive

### 44. 💀 DEATH ROLL
- WoW gambling classic
- Start at 100
- Shake = roll (1 to current max)
- Result becomes new max
- Roll 1 = DEATH (game over)
- Score = rolls survived × 100
- Anxiety inducing

### 45. 🎪 SHAME WHEEL
- Spin for punishment level
- Shake to spin wheel
- 1-6 LEDs = Mild (tell joke)
- 7-11 LEDs = Medium (truth)
- 12-15 LEDs = Spicy (story)
- 16 LEDs = NUCLEAR (group decides)
- 3 rounds
- Maximum embarrassment

### 46. 💎 ALL IN
- Degenerate gambling game
- Start with 1000 points
- TAP = bet it all (50/50 flip)
- HOLD 3s = walk away with current bankroll
- Up to 5 flips
- Double or ZERO each flip
- Max possible: 32,000 points
- "SEND IT!" energy

### 47. 🤸 COPYCAT CHAOS
- Follow the leader movement game
- Game shows: SHAKE / SPIN / JUMP / FREEZE / TAP
- 3 second window to perform
- Motion sensor judges accuracy
- 5 rounds
- Success = +200 points
- Drunk people flailing = comedy

### 48. 🍻 BEER ROULETTE
- Russian roulette with drinks
- 6 drinks, 1 is "loaded"
- SHAKE = select this drink
- WAIT 5s = skip to next
- Pick loaded = 0 points
- Each safe pick = +200
- Suspense builds

### 49. 🔥 NEVER HAVE I EVER
- Digital drinking game
- 8 statements read
- TAP = you HAVE done it (+100)
- FREEZE = you HAVEN'T
- 3 second window per statement
- Exposes secrets
- Social bonding

### 50. 🎭 ACCENT ROULETTE
- Comedy performance game
- Shake to spin for accent
- Russian / Irish / French / Southern / Pirate / Valley Girl
- Speak in accent for 60 seconds
- LED countdown timer
- Group votes if convincing
- Approved = 1000 points
- Stupid funny every time

### 51. 🎓 TRIVIA SPINNER
- LED spinner for A/B/C/D answers
- Question displayed on TV/phone/Serial
- LEDs divided into 4 color quadrants
- A = Red (0-3), B = Green (4-7), C = Blue (8-11), D = Yellow (12-15)
- White LED spins at 120ms/LED
- TAP to STOP on your answer
- 5 questions
- Correct = +200 points
- Works with bar TV for questions

---

## 📺 TV-INTEGRATED GAMES (52-56)

### 52. 🏎️ PUCK RACER
- Endless runner racing game
- Tilt left/right to steer car through 4-lane highway
- Hold button to accelerate (60→100 mph)
- Shake for nitro boost (150 mph, 3 uses)
- Avoid obstacles: 🚧 cones, 💀 skulls, ⚠️ warnings
- Collect 💎 coins (+100) and ⚡ nitro refills
- Combo system: 3 coins in row = 2x multiplier
- Near-miss bonus: +50 for close calls
- 90 seconds, 3 crashes = game over
- Real-time WebSocket streaming to TV

### 53. ☄️ OBSTACLE DODGER
- 2D movement dodge game
- Tilt left/right + forward/back for full 2D control
- Dodge falling meteors ☄️ and bombs 💣
- Collect yellow stars 🟡 for +200 points
- Hit meteor/bomb = -100 points, +1 hit
- 5 hits = game over
- Survival scoring: +1 per frame
- 60 second time limit
- Fast-paced, accessible

### 54. ⛳ PUCK GOLF
- Mini-golf with physics
- Tilt left/right to aim (-90° to +90°)
- Hold button to charge power (0-100%)
- Shake to swing and release ball
- 9 holes, par 3 each
- Scoring: Start 1000, -50 per stroke
- Under par bonus: +300
- Ball has physics (rolls, friction, bounces)
- Aim line shows trajectory
- Power bar charges visually
- 5 minute game

### 55. 👾 SPACE INVADERS PUCK
- Classic arcade shooter
- Tilt left/right to move ship
- Shake to shoot lasers
- 4 rows × 8 columns = 32 aliens per wave
- Aliens shoot back randomly
- Kill alien: +100 points
- Clear wave: +500 points
- 3 lives
- 0.3s cooldown between shots
- Retro arcade nostalgia

### 56. 🏓 PONG PUCK
- Classic Pong vs AI
- Tilt forward/back to move paddle
- AI tracks ball with slight lag
- Ball bounces off walls + paddles
- Angle changes based on paddle hit position
- First to 7 points wins
- 5 minute time limit
- Simple, competitive classic

---

## 🧠 YDKJ-STYLE TRIVIA GAMES (57-97)

### 57. 🔪 TRIVIA MURDER PARTY
- Horror-themed trivia game
- Answer questions via TILT (A/B/C/D)
- Wrong answer = "Killing Floor" mini-game
- SHAKE to escape death
- SPIN for roulette penalty
- TAP for timing challenge
- Last survivor wins
- Hard difficulty

### 58. ⚔️ CATEGORY ROYALE
- SHAKE to claim categories first
- "Ways to Die Stupidly" vs "Florida Man"
- First to shake picks category
- 5 questions per category
- Speed + knowledge combo
- Medium difficulty

### 59. ⚡ SPEED PYRAMID
- Answer speed determines point tiers
- Gold tier (first 3s): 1000pts
- Silver tier (3-6s): 500pts
- Bronze tier (6-10s): 200pts
- TILT to answer + TAP to lock in
- Fast = more points
- Medium difficulty

### 60. ✅ FACT OR CRAP
- True/False absurd scenarios
- TILT LEFT = Fact
- TILT RIGHT = Crap
- HOLD = Double Down (2x points/penalty)
- "Florida Man arrested for teaching alligators to breakdance"
- Medium difficulty

### 61. 🎮 YOU DON'T KNOW JACK: PUCK EDITION
- Classic YDKJ gameplay
- SHAKE + HOLD to screw opponent
- Force them to answer your question
- Absurd comedy questions
- Gangrene-style dark humor
- Medium difficulty

### 62. 🎰 MULTIPLIER MADNESS
- SPIN puck before each question
- Fast spin = 5x multiplier (risk/reward)
- Slow spin = 0.5x multiplier (safe)
- Wrong answer = negative multiplier applied
- Gambling + trivia combo
- Hard difficulty

### 63. 🎡 WHEEL OF ENORMOUS PROPORTIONS
- Answer trivia question correctly
- Unlock wheel spin bonus
- SPIN puck to land on point zones
- Fastest SPIN = biggest multiplier
- Correct answer required to spin
- Medium difficulty

### 64. 📊 GUESSPIONAGE
- Guess percentages of survey results
- TILT to adjust guess (0-100%)
- TAP to lock in answer
- "What % of people have texted while driving?"
- Closest guess wins points
- Medium difficulty

### 65. 💀 TRIVIA GAUNTLET
- 3 strikes elimination mode
- Miss 3 questions = eliminated
- Last puck standing wins
- Increasing difficulty
- Survival pressure
- Medium difficulty

### 66. 📅 TIMEJINX
- Guess the year events happened
- TILT to adjust year (1900-2025)
- TAP to submit guess
- "When did Hitler shoot himself?" (1945)
- Closest year wins
- Points based on accuracy
- Medium difficulty

### 67. 🤥 FIBBAGE: PUCK LIES
- Players create fake lies
- Vote for the truth via puck
- Phone/TV for text entry
- TILT through options, TAP to vote
- "What killed 10,000 Austrian soldiers?"
- Social deduction + creativity
- Medium difficulty

### 68. 💬 SURVIVE THE INTERNET
- Twist other players' quotes
- Speak quotes into puck mic
- Others SPIN to select twist category
- "I love animals" → "...as food"
- TAP to vote on funniest
- Comedy + social game
- Medium difficulty

### 69. ⚖️ SPLIT THE ROOM
- Create divisive scenarios
- Goal: 50/50 vote split
- TILT LEFT or RIGHT to vote
- "Fly but every fart kills a puppy. Accept?"
- Points for even split
- Creative + social
- Medium difficulty

### 70. 🕵️ HYPNOTORIOUS
- Find the "Outlier" player
- Everyone answers questions
- One player has different secret category
- SHAKE to accuse outlier
- Social deduction
- Medium difficulty

### 71. 🔍 SUSPECTIVES
- Murder mystery deduction
- Find guilty player from evidence
- TILT through suspects
- SHAKE to accuse
- "Who double-dips chips?"
- Evidence-based guessing
- Hard difficulty

### 72. 🎭 FAKIN' IT: PUCK EDITION
- One player is "Faker"
- Everyone gets same instruction except Faker
- "Shake 3 times" (Faker gets different amount)
- TILT to vote who's fake
- Social observation game
- Medium difficulty

### 73. 🔪 WEAPONS DRAWN
- Murder mystery with LED signatures
- Each puck has unique LED flash pattern
- Pattern = murder weapon
- SPIN creates signature
- TILT to accuse murderer
- Social deduction
- Hard difficulty

### 74. 💬 QUIPLASH: PUCK WARS
- Funniest answer wins
- Phone for text entry
- TILT LEFT/RIGHT to vote
- "What's in Trump's wig?"
- Comedy + voting
- Easy difficulty

### 75. 🎤 MAD VERSE CITY: RAP BATTLE
- Fill-in-the-blank rap lyrics
- Pre-written lyrics
- TAP to pick rhyme from options
- "Yo mama's so fat, she ____"
- Comedy + rhythm
- Medium difficulty

### 76. 😂 JOKE BOAT
- Complete joke setups
- Phone for text completion
- TILT to vote on jokes
- "A man walks into a bar and ____"
- Funniest completion wins
- Easy difficulty

### 77. 📖 DICTIONARIUM
- Define fake words
- Phone for definitions
- TILT to vote for best
- "What does 'Blorgenschmidt' mean?"
- Creativity + humor
- Medium difficulty

### 78. 📱 FIXYTEXT
- Chaotic autocorrect fails
- TILT to inject words into text
- "Sorry I'm late, I was ____"
- Random word injection comedy
- Easy difficulty

### 79. 🔤 WORD SPUD
- Word association chain
- TILT through word bank
- TAP to select association
- "Pizza" → "Italy" → "Rome"
- Quick thinking
- Easy difficulty

### 80. 💭 BLATHER 'ROUND
- Describe with limited vocabulary
- Pre-selected phrase templates
- Others guess via TILT
- "Thing with four legs... you sleep on it" (Bed)
- Communication challenge
- Medium difficulty

### 81. 🎨 NONSENSORY
- Rate descriptions 1-10 scale
- TILT to adjust rating
- TAP to submit
- "How metal is 'cutting off gangrenous foot'?"
- Subjective humor
- Easy difficulty

### 82. 💰 ALL OR NOTHING
- Bet all points on final question
- TILT to adjust bet amount (0-100%)
- SHAKE to go all-in
- Timeout (10s) = forced bet
- High stakes finale
- Medium difficulty

### 83. 🎯 RUSSIAN ROULETTE TRIVIA
- Wrong answer = progressive punishment
- SPIN determines penalty severity (1x-6x loss)
- Land on skull = lose all points
- Gambling + trivia pressure
- Hard difficulty

### 84. 💵 DOUBLE OR NOTHING
- After each correct answer option
- SHAKE to double down (risk for 2x)
- HOLD to keep current points
- Wrong answer on double = lose all
- Risk/reward decisions
- Medium difficulty

### 85. 🏆 BRACKETEERING: TRIVIA TOURNAMENT
- Answers compete in bracket
- TILT to vote in head-to-head matchups
- "Best way to die?" A vs B
- Winners advance
- Tournament structure
- Medium difficulty

### 86. 🔥 LUCKY STREAK
- Consecutive correct answers multiply points
- 3 in row = 3x multiplier
- 5 in row = 5x multiplier
- Miss one = reset to 1x
- Streak pressure
- Medium difficulty

### 87. ⚡ SHAKE ATTACK (Jack Attack)
- Rapid-fire category matching
- TV shows word
- SHAKE when it matches category
- "Florida Man headlines" → word appears → SHAKE!
- Fast reflexes + knowledge
- Hard difficulty

### 88. 🎯 SCREW YOUR NEIGHBOR
- Pay points to force opponent to answer
- SHAKE + HOLD to activate screw
- Hard questions screwed to others
- Social + strategic
- Medium difficulty

### 89. 🔒 HOSTAGE TRIVIA
- One player vs everyone
- Reversed scoring
- If hostage correct = everyone ELSE loses points
- If hostage wrong = hostage loses points
- Unique dynamics
- Hard difficulty

### 90. 🌀 CHAOS ROUND
- Random modifiers each question
- SPIN before question determines rule
- "Opposite Day" = wrong answer = points
- "Swap Scores" = steal from leader
- Unpredictable chaos
- Hard difficulty

### 91. ⏱️ PERFECT TIMING
- Answer question correctly
- THEN tap at exact countdown moment
- TV countdown shows
- TAP at zero = double points
- Timing + knowledge combo
- Medium difficulty

### 92. 🧘 BALANCE MASTER
- Answer trivia while balancing puck
- Accelerometer detects movement
- Shake = penalty (-50 pts)
- Answer on forehead/hand/foot
- Physical + mental challenge
- Hard difficulty

### 93. 🌪️ SPIN ZONE
- Answer speed + spin speed combined
- TILT to answer quickly
- THEN spin for multiplier
- Fast answer + fast spin = max points
- Dual skill test
- Medium difficulty

### 94. ⛏️ THE POLL MINE
- Teams guess poll rankings
- TILT to select answer
- Team must agree or lose "torch"
- "Rank: Ways to die" → Pick #1 most popular
- Cooperative guessing
- Medium difficulty

### 95. 😈 DEVILS AND THE DETAILS
- Complete family chores cooperatively
- Compete for selfish tasks
- SHAKE for chores (team)
- HOLD for selfish tasks (personal meter)
- "Do dishes" (team) vs "Eat cookies" (selfish)
- Cooperation + competition
- Medium difficulty

### 96. 👽 PUSH THE BUTTON
- Find the alien impostor
- Aliens get different prompts
- "Shake 3 times" (human) vs "Shake 5 times" (alien)
- SHAKE to accuse
- Among Us mechanics
- Medium difficulty

### 97. 🐉 LEGENDS OF TRIVIA
- Cooperative RPG trivia
- Answer trivia to deal damage
- SHAKE for power-ups
- Fight monsters together
- "What's gangrene?" = 100 damage
- 10 questions to kill boss
- Team cooperation
- Medium difficulty

---

## 📊 GAME COUNT BY TYPE

**Physical Skill Games (1-51):** 51 games
- Button mashing: 8 games
- Shake detection: 12 games
- Timing precision: 9 games
- Memory/pattern: 6 games
- Social/multi-player: 8 games
- Gambling/risk: 8 games

**TV-Integrated Games (52-56):** 5 games
- Racing: 1 game
- Dodging: 1 game
- Sports: 2 games
- Arcade: 1 game

**Trivia Games (57-97):** 41 games
- Core trivia: 10 games
- Lie detection/deception: 7 games
- Word & creativity: 8 games
- Gambling & risk: 5 games
- Physical & skill hybrid: 7 games
- Team & cooperative: 4 games

---

## 🎯 TOTAL: 97 GAMES

**Ready to play:** 56 games (51 ESP32 + 5 TV)
**In development:** 41 trivia games (7 engines complete)

**Market positioning:** "97 games. One puck. Zero bullshit." 🎮
