austinscip/table-wars-puck/docs/archive/GAMES.md

# 🎮 TABLE WARS - GAME DOCUMENTATION

**All 8 Mini-Games Explained**

---

## 🚀 Getting Started

### How to Run Game Mode

1. **Edit `src/main.cpp`**
2. **Uncomment `#define TABLE_WARS_MODE`** (line 31)
3. **Comment out other modes**
4. **Upload to your puck**

```cpp
// #define NORMAL_MODE
#define TABLE_WARS_MODE      // 🎮 USE THIS!
```

5. **Open Serial Monitor** (115200 baud) to see game progress
6. **Games will auto-cycle** every ~30 seconds

---

## 🎯 Game Controls

All games use:
- **Big button** - Primary action (tap, confirm, stop)
- **Shake/movement** - Detected by MPU6050
- **LED ring** - Visual feedback
- **Buzzer** - Audio cues
- **Vibration motor** - Haptic feedback

---

## 🎮 THE GAMES

### 1. ⚡ SPEED TAP BATTLE

**Concept:** Mash the button as fast as humanly possible!

**How to Play:**
1. 3-2-1 countdown
2. LEDs turn GREEN = GO!
3. Tap button as fast as you can for 10 seconds
4. Each tap lights up an LED

**Scoring:**
- Each tap = 10 points
- Typical score: 200-400 points
- Pro score: 600+ points

**Strategy:**
- Use multiple fingers
- Rapid tapping technique
- Watch the LED ring fill up!

**Why It Works:**
- Pure dopamine rush
- Easy to understand
- Competitive instantly
- Great to watch/film

---

### 2. 🔥 SHAKE DUEL

**Concept:** Shake the puck as violently as possible!

**How to Play:**
1. 3-2-1 countdown
2. LEDs turn GREEN = GO!
3. Shake puck for 10 seconds
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
