austinscip/table-wars-puck/cad/BUTTON_ABOVE_SURFACE.png

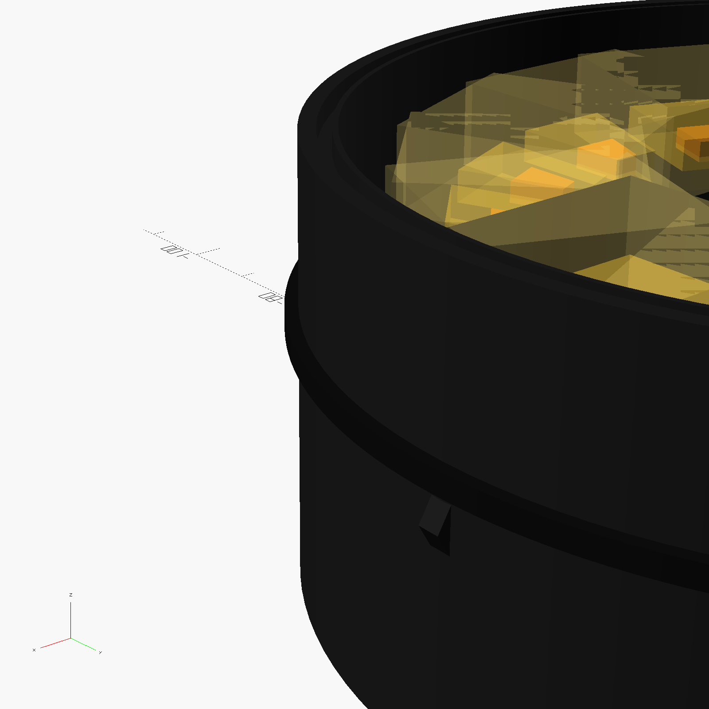
cad/BUTTON_ABOVE_SURFACE.png
