austinscip/table-wars-puck/cad/button_glyph_closeup.png

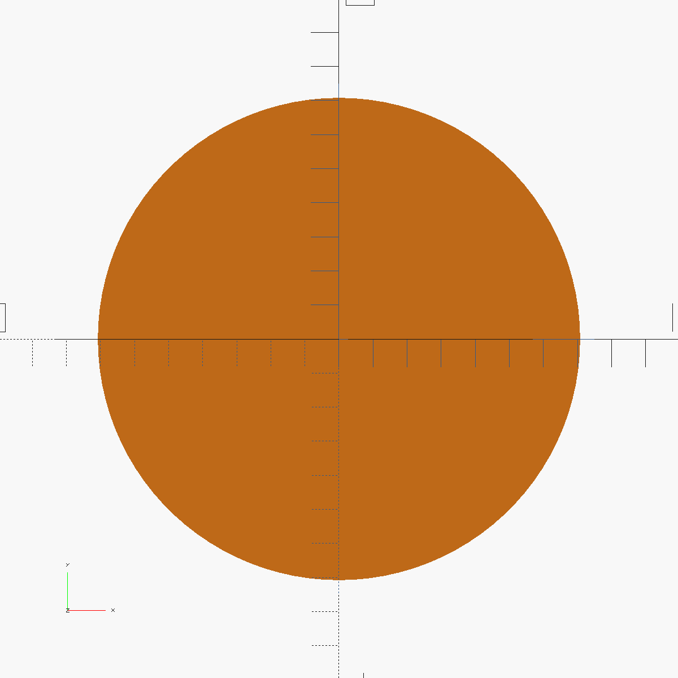
cad/button_glyph_closeup.png
