austinscip/table-wars-puck/cad/BUTTON_SIDE_CLEAR.png

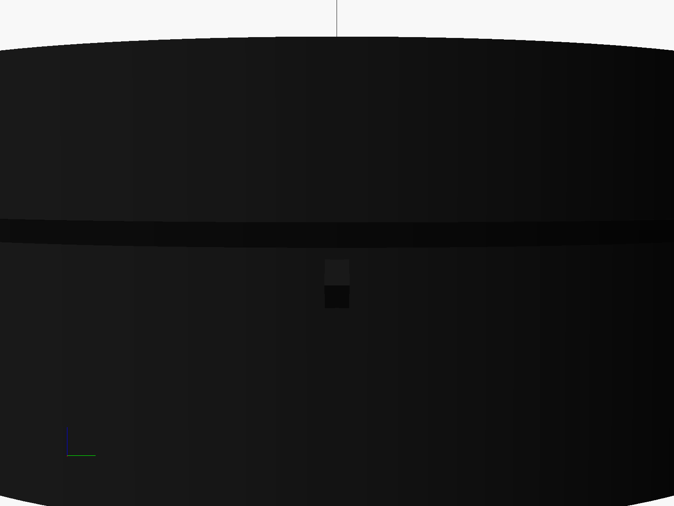
cad/BUTTON_SIDE_CLEAR.png
