austinscip/table-wars-puck/cad/BUTTON_TOP_VIEW.png

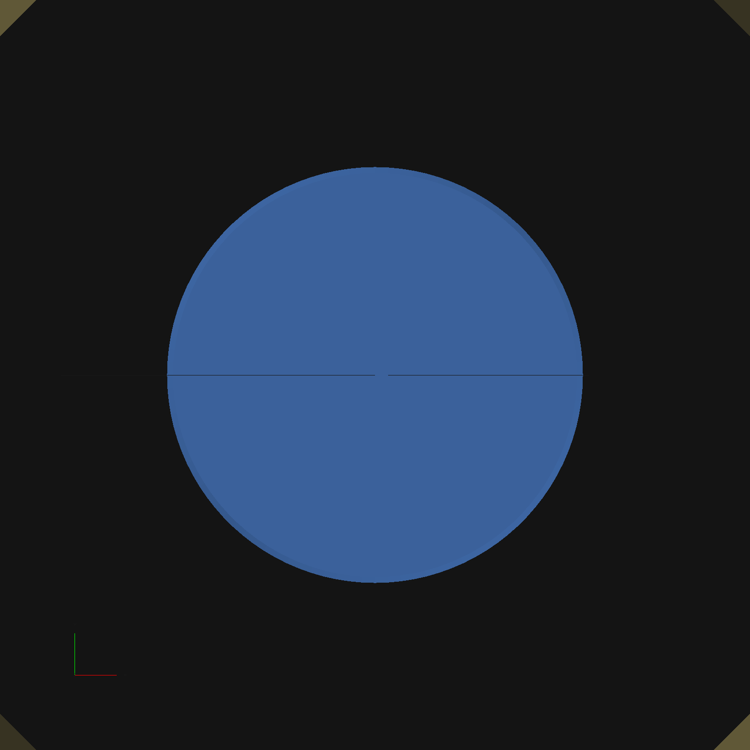
cad/BUTTON_TOP_VIEW.png
