austinscip/table-wars-puck/cad/FINAL_TOP_VIEW.png

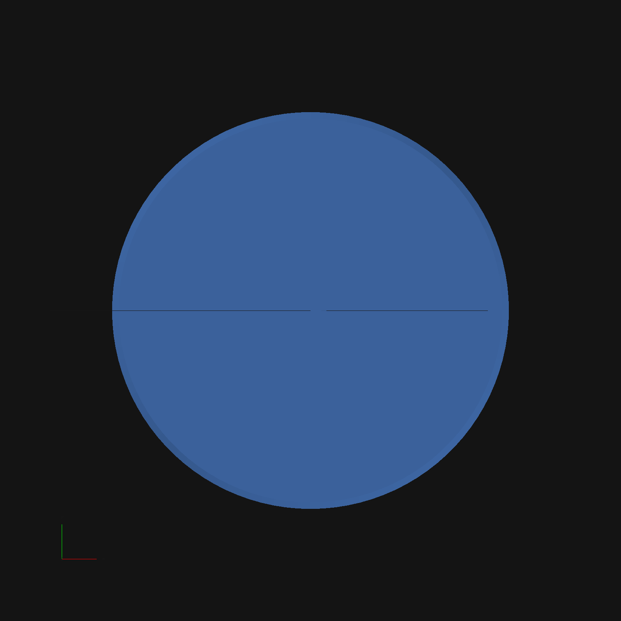
cad/FINAL_TOP_VIEW.png
