austinscip/table-wars-puck/cad/PRODUCT_BUTTON_SIDE.png

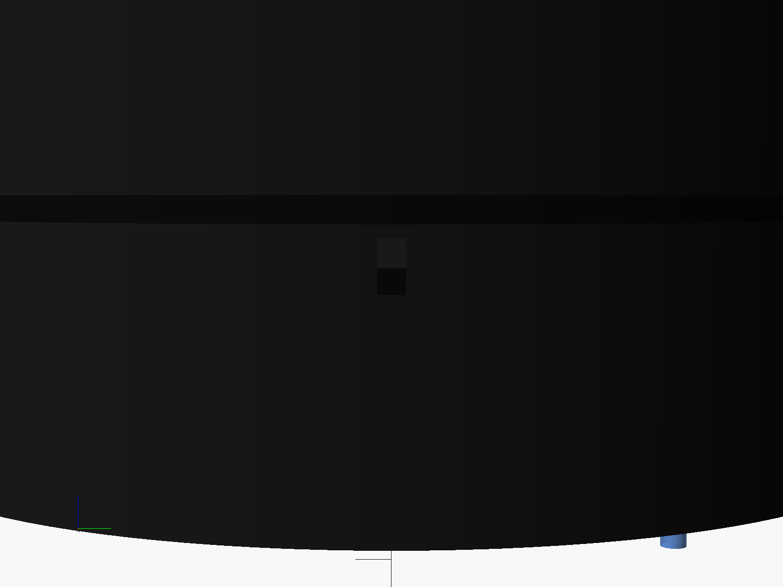
cad/PRODUCT_BUTTON_SIDE.png
