austinscip/table-wars-puck/cad/PRODUCT_LEDS_ON_top.png

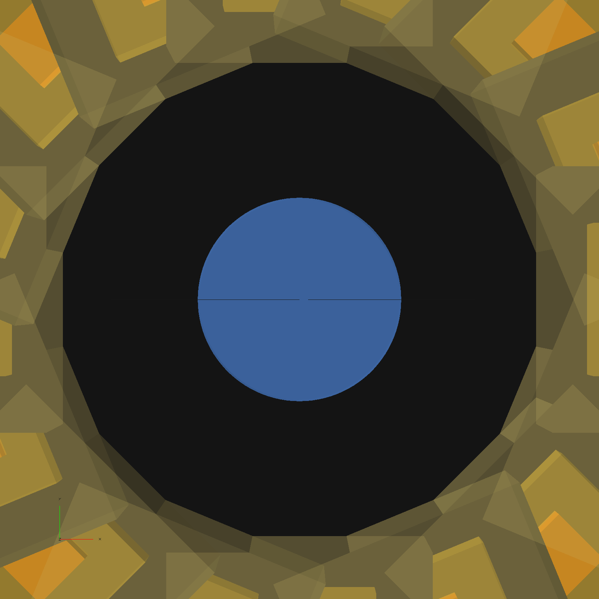
cad/PRODUCT_LEDS_ON_top.png
