austinscip/table-wars-puck/cad/PRODUCT_VIEW_angled.png

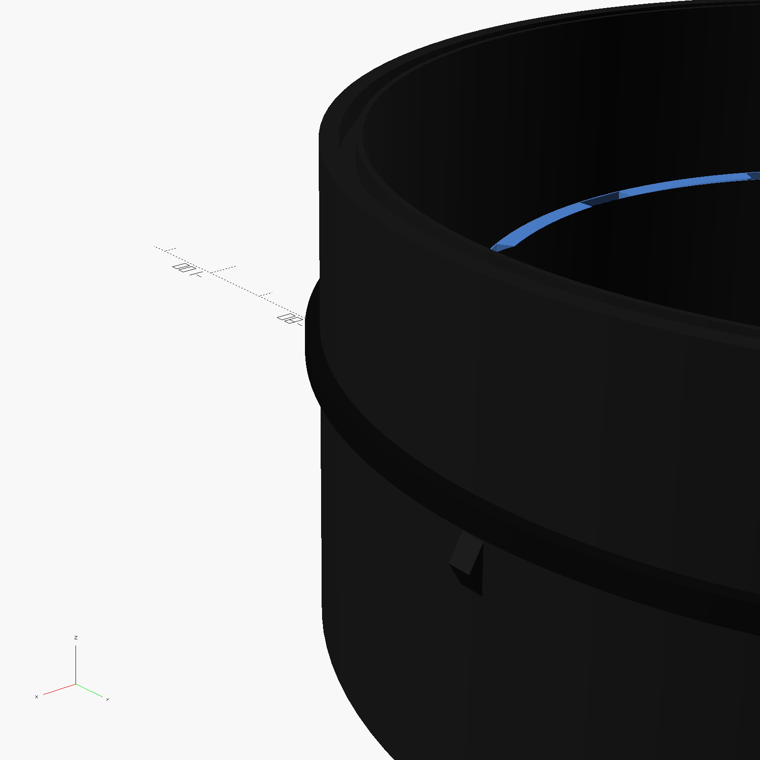
cad/PRODUCT_VIEW_angled.png
