austinscip/table-wars-puck/cad/PRODUCT_VIEW_side.png

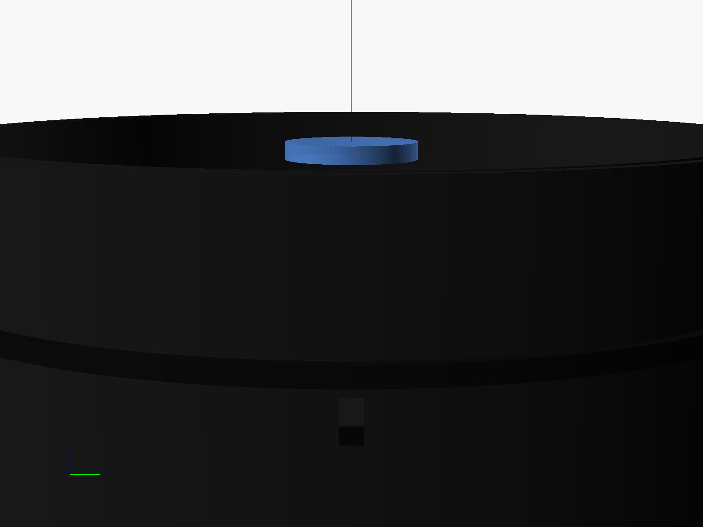
cad/PRODUCT_VIEW_side.png
