austinscip/table-wars-puck/cad/PRODUCT_VIEW_top.png

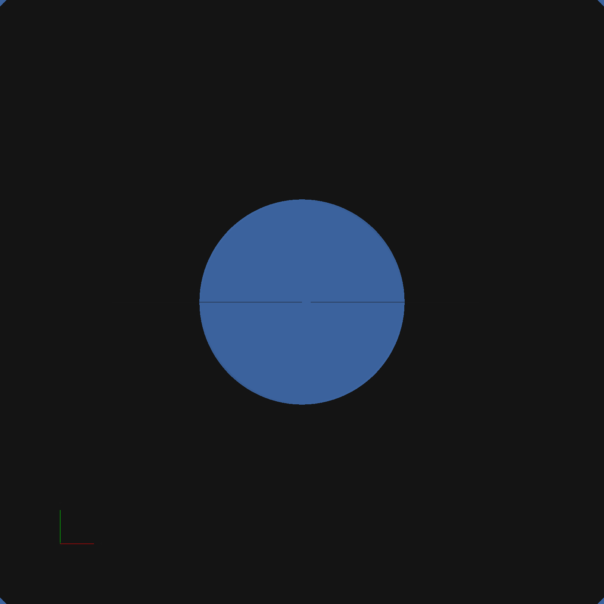
cad/PRODUCT_VIEW_top.png
