austinscip/table-wars-puck/cad/top_shell_details.png

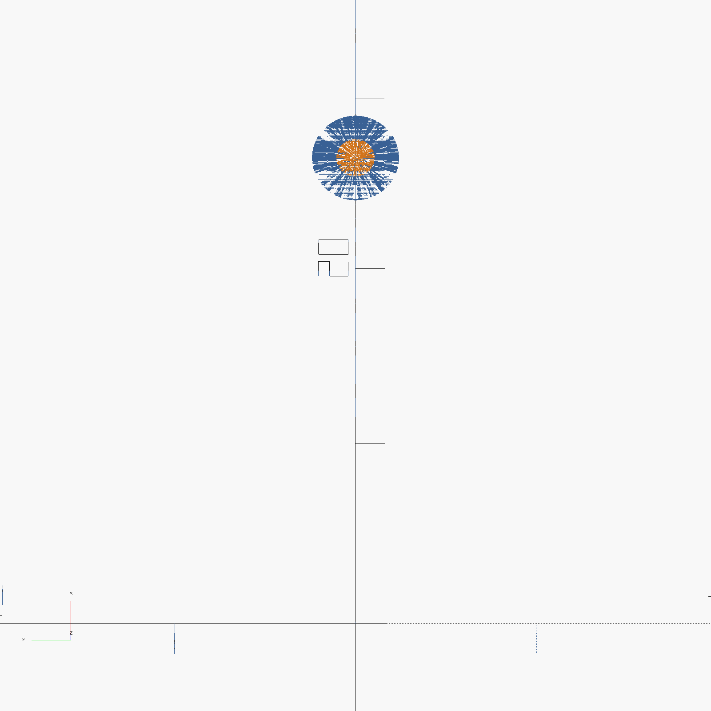
cad/top_shell_details.png
