austinscip/table-wars-puck/cad/top_shell_top_view.png

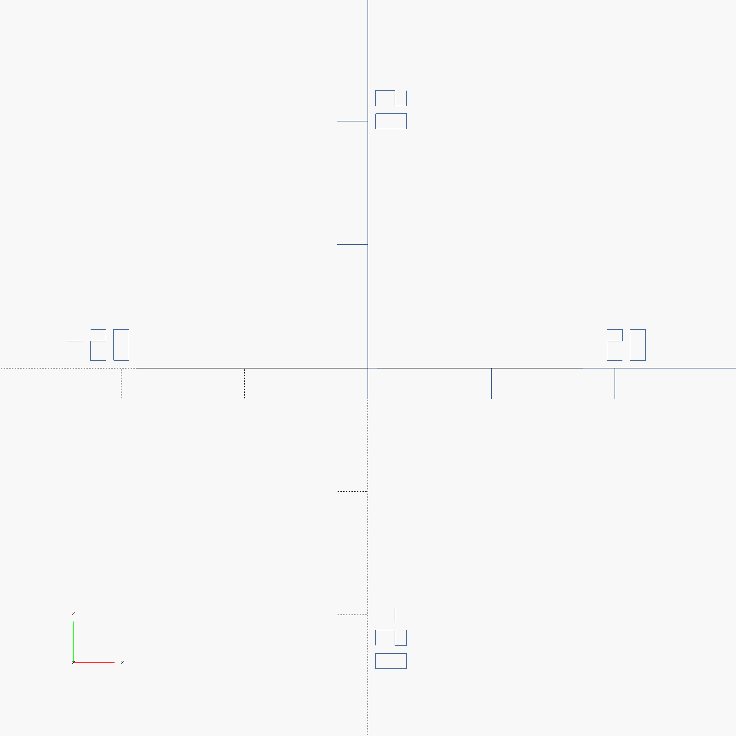
cad/top_shell_top_view.png
