austinscip/table-wars-puck/cad/forerunner_top_shell.stl

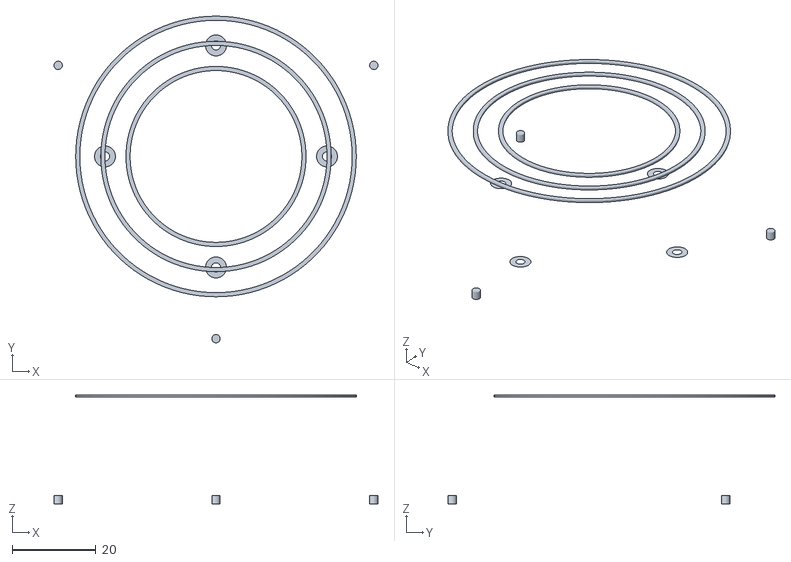
[picture p21: CAD file, 2026-01-06]
cad/forerunner_top_shell.stl
77.3 x 78.0 x 26.0
