austinscip/table-wars-puck/cad/forerunner_top_shell_v2.stl

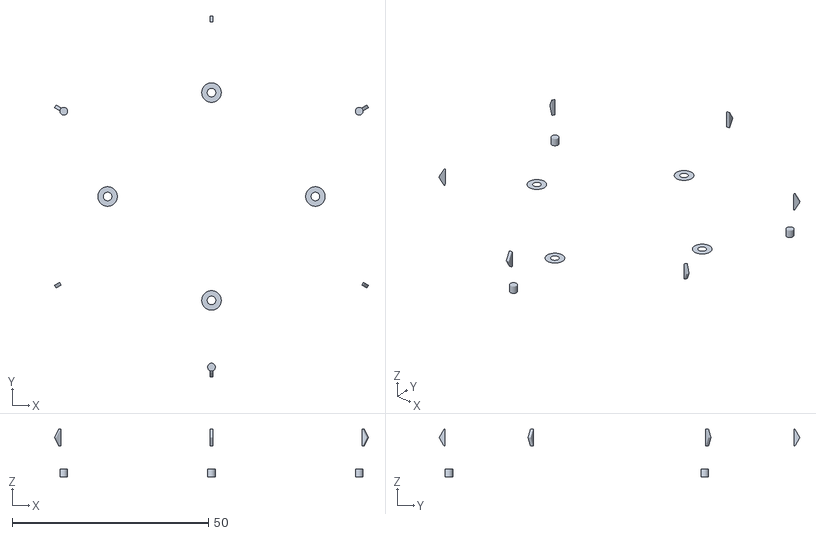
[picture p22: CAD file, 2026-01-06]
cad/forerunner_top_shell_v2.stl
80.1 x 92.0 x 12.2
