austinscip/table-wars-puck/cad/forerunner_bottom_shell.stl

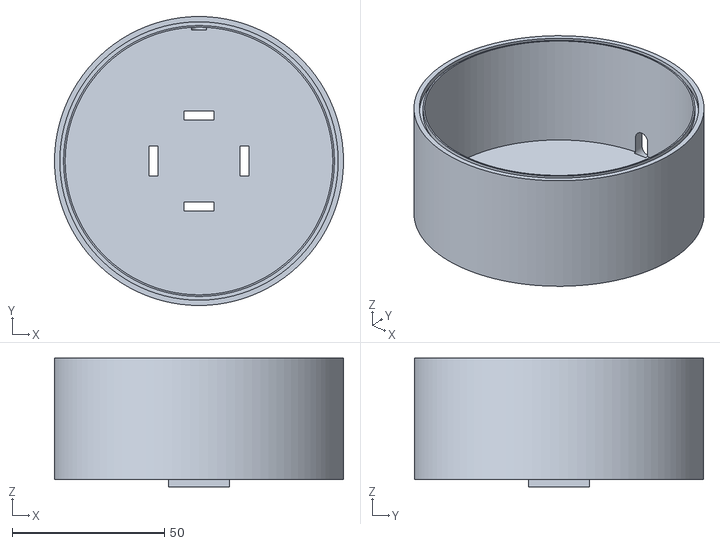
[picture p23: CAD file, 2026-01-06]
cad/forerunner_bottom_shell.stl
95.0 x 95.0 x 42.4
