austinscip/table-wars-puck/docs/manufacturing/MANUFACTURING_GUIDE.md

# Table Wars Puck - Manufacturing Guide

Your complete guide from design files to working pucks in your hands.

---

## 🎯 Current Status: DESIGN COMPLETE ✅

**What you have:**
- ✅ Professional PCB design (circular, 8/10 rating)
- ✅ ESP32 + sensors + LEDs + power management
- ✅ Working firmware (BLE + WiFi tested)
- ✅ Component list extracted (26 parts identified)

**What you need:**
- ❌ Manufacturing files (Gerbers, BOM, assembly docs)

---

## 📋 The Manufacturing Journey

### **Phase 1: Get Manufacturing Files** ⏱️ 1-3 days
**Status:** CURRENT STEP

**Action Items:**
1. Send message to freelancer (use FREELANCER_REQUEST.md)
2. Wait for files (usually 1-3 days)
3. Verify files (use MANUFACTURING_CHECKLIST.md)

**Timeline:** 1-3 business days
**Cost:** $0 (already paid freelancer)

---

### **Phase 2: Get Manufacturing Quote** ⏱️ 1 hour
**Status:** WAITING FOR FILES

**Action Items:**
1. Upload Gerbers to JLCPCB.com
2. Configure PCB specs (black, ENIG finish, etc.)
3. Add SMT assembly service
4. Upload BOM and pick-and-place files
5. Review quote

**Timeline:** Instant online quote
**Expected Cost:**
- **5 bare PCBs:** $10-20
- **5 fully assembled:** $150-250

**Comparison:**
| Option | PCBs | Assembly | Components | Total |
|---|---|---|---|---|
| **Bare PCBs only** | $15 | DIY | ~$100 | ~$115 |
| **Full assembly** | $15 | $80 | Included | ~$180 |
| **Hybrid (SMD only)** | $15 | $50 | $30 | ~$95 |

---

### **Phase 3: Order Prototypes** ⏱️ 15 minutes
**Status:** WAITING FOR FILES

**Action Items:**
1. Review quote carefully
2. Double-check BOM matches your needs
3. Add to cart
4. Pay (credit card or PayPal)
5. Wait for production

**Timeline:** 15 mins to place order
**Cost:** $150-250 for 5 assembled boards

**What You'll Pay For:**
- PCB fabrication: ~$15
- PCB assembly setup: ~$50-80 (one-time per order)
- Components: ~$15-25 per board
- Shipping: ~$20-40 (DHL/FedEx express)

---

### **Phase 4: Manufacturing** ⏱️ 7-10 days
**Status:** WAITING FOR FILES

**What Happens:**
1. **PCB Fabrication** (3-5 days)
   - Laser cutting copper layers
   - Drilling holes
   - Applying soldermask
   - Silkscreen printing
   - Surface finish (ENIG)

2. **SMT Assembly** (2-3 days)
   - Automated pick-and-place machines
   - Solder paste application
   - Reflow oven (melts solder)
   - Visual inspection
   - Testing (if requested)

3. **QC & Packaging** (1 day)
   - Quality control checks
   - Packaging for shipping
   - Shipping label

**Timeline:** 7-10 business days
**You Do:** Nothing! Just wait for tracking number

---

### **Phase 5: Shipping** ⏱️ 3-7 days
**Status:** WAITING FOR FILES

**Shipping Options:**
- **Standard (15-25 days):** ~$10 - NOT recommended
- **Express DHL (3-7 days):** ~$20-40 - RECOMMENDED
- **Urgent (2-3 days):** ~$60+ - Overkill for prototypes

**Recommendation:** DHL Express (~$30)
- Fast enough
- Full tracking
- Reliable customs clearance

**Timeline:** 3-7 days
**Tracking:** Provided via email

---

### **Phase 6: Arrival & Testing** ⏱️ 1-3 days
**Status:** WAITING FOR FILES

**What You'll Receive:**
- 5 PCB boards in anti-static bags
- Some come partially assembled (depends on your order)
- May include leftover components

**Action Items:**
1. **Visual Inspection** (10 mins)
   - Check for obvious defects
   - Verify all components present
   - Look for solder bridges or cold joints

2. **Power Test** (30 mins)
   - Connect USB-C cable
   - Check voltage outputs with multimeter
   - Verify no magic smoke 🚭

3. **Program Firmware** (1 hour)
   - Connect via USB
   - Upload BLE+WiFi firmware
   - Monitor serial output

4. **Functional Test** (2 hours)
   - Test BLE connection
   - Test WiFi connection
   - Test button presses
   - Test LED animations
   - Test accelerometer (shake detection)
   - Test buzzer
   - Test motor (if included)

**Timeline:** 1-3 days of testing
**Expected Issues:** 1-3 bugs in first prototype (normal!)

---

## 💰 Total Cost Breakdown

### **Scenario A: Full Professional Assembly** (Recommended for first run)

| Item | Cost |
|---|---|
| PCB fabrication (5 boards) | $15 |
| Assembly setup fee | $80 |
| Components (5x) | $90 |
| Shipping (DHL) | $30 |
| **TOTAL** | **~$215** |

**Cost per puck:** ~$43

**Pros:**
- ✅ Professional quality
- ✅ No soldering required
- ✅ Fast turnaround
- ✅ Lower risk of assembly errors

**Cons:**
- ❌ Higher upfront cost
- ❌ Setup fee makes small orders expensive

---

### **Scenario B: Bare PCBs + DIY Assembly** (Budget option)

| Item | Cost |
|---|---|
| PCB fabrication (5 boards) | $15 |
| Components (bulk order) | $100 |
| Shipping | $20 |
| **TOTAL** | **~$135** |

**Cost per puck:** ~$27

**Pros:**
- ✅ Cheaper
- ✅ Learn soldering skills
- ✅ Full control

**Cons:**
- ❌ Requires soldering equipment
- ❌ Time-consuming (4-6 hours per board)
- ❌ Higher risk of errors
- ❌ Tiny SMD components are HARD to solder

---

### **Scenario C: Hybrid Assembly** (Best value for experienced makers)

| Item | Cost |
|---|---|
| PCB fabrication (5 boards) | $15 |
| SMD assembly (small parts only) | $50 |
| Through-hole components (you buy) | $30 |
| Shipping | $25 |
| **TOTAL** | **~$120** |

**Cost per puck:** ~$24

**Pros:**
- ✅ Factory handles difficult SMD parts
- ✅ You solder easy through-hole parts
- ✅ Lower cost than full assembly
- ✅ Still professional quality for SMD

**Cons:**
- ❌ Still requires some soldering
- ❌ Slightly more complex ordering

---

## ⏱️ Complete Timeline

**From today to working pucks:**

| Phase | Duration | Your Effort |
|---|---|---|
| Get files from freelancer | 1-3 days | 30 mins |
| Get quote & order | 1 day | 1 hour |
| Manufacturing | 7-10 days | 0 hours |
| Shipping | 3-7 days | 0 hours |
| Assembly (if DIY) | 1-3 days | 20 hours |
| Testing & debugging | 1-3 days | 6 hours |
| **TOTAL** | **2-4 weeks** | **8-28 hours** |

**Realistic Target:** Have working pucks in 3 weeks

---

## 🎯 Milestones

### **Week 1: Get Files & Order**
- ✅ Request files from freelancer (Day 1)
- ✅ Receive and verify files (Day 2-3)
- ✅ Get quote from JLCPCB (Day 3)
- ✅ Place order (Day 3)
- ⏳ Manufacturing starts (Day 4)

### **Week 2: Manufacturing**
- ⏳ PCB fabrication (Day 4-8)
- ⏳ SMT assembly (Day 9-11)
- ⏳ QC & shipping (Day 12)

### **Week 3: Delivery & Testing**
- ⏳ Shipping in transit (Day 13-17)
- ✅ Package arrives! (Day 18)
- ✅ Visual inspection (Day 18)
- ✅ Power test (Day 19)
- ✅ Program & test (Day 19-21)

### **Week 4: Refinement** (if needed)
- 🐛 Fix any bugs found
- 🔄 Order revised boards (if major issues)
- 📦 Order production run (if all good!)

---

## 🚨 Common Issues & Solutions

### **Issue: Gerbers Won't Upload**
**Cause:** Wrong file format or corrupt zip
**Solution:** Ask freelancer to re-export, specify RS-274X format

### **Issue: Parts Out of Stock**
**Cause:** Component shortage (happens with chips)
**Solution:** Ask freelancer for alternative part numbers that are in stock

### **Issue: Quote Is Too High**
**Cause:** Uncommon components or small quantity
**Solutions:**
- Order more boards (10 instead of 5) - setup fee amortizes
- Remove assembly service, do it yourself
- Use LCSC parts library only (cheaper)

### **Issue: Board Doesn't Power On**
**Causes:** Short circuit, wrong voltage, reversed polarity
**Solutions:**
- Check for solder bridges with magnifying glass
- Test continuity with multimeter
- Verify power supply voltage (should be 5V from USB)

### **Issue: ESP32 Won't Program**
**Causes:** Wrong USB driver, bad cable, wrong pins
**Solutions:**
- Install CP2102 or CH340 USB driver
- Try different USB cable (must be data cable, not charge-only)
- Hold BOOT button while connecting

---

## 📦 What Comes After Prototypes?

### **If Prototypes Work Great:**

**Option 1: Small Production Run (10-50 pucks)**
- Cost per board drops to ~$25-30
- Still use JLCPCB/PCBWay
- Order in batches as you sell

**Option 2: Medium Production (50-500 pucks)**
- Negotiate with PCB manufacturer
- Cost per board ~$15-20
- Consider contract manufacturer (CM)

**Option 3: Large Production (500+ pucks)**
- Work with CM in China
- Cost per board ~$10-15
- Requires MOQ (minimum order quantity)
- Consider crowdfunding first

### **If Prototypes Need Changes:**

1. Document all bugs/issues
2. Modify design (you or freelancer)
3. Order new prototypes (cheaper 2nd time, no design fee)
4. Test again
5. Iterate until perfect

**Normal:** 2-3 iterations before production-ready

---

## 🎓 Learning Resources

### **If You Want to Solder:**
- YouTube: "How to Solder SMD Components"
- Required tools: ~$50-100
  - Soldering iron (TS100 or Pinecil)
  - Solder (63/37 leaded or SAC305 lead-free)
  - Flux pen
  - Tweezers
  - Magnifying glass/microscope

### **If You Want to Learn PCB Design:**
- Software: KiCad (free) or EasyEDA (free)
- Alternative to Altium (no $7000 fee)
- Can edit and revise your design

### **If You Want to Understand the Circuit:**
- Read the schematic PDF (when you get it)
- Google each IC datasheet
- Understand power flow, signal routing

---

## ✅ Success Checklist

**You're ready to order when:**
- [ ] Received all manufacturing files from freelancer
- [ ] Verified files using MANUFACTURING_CHECKLIST.md
- [ ] Uploaded Gerbers to JLCPCB (or PCBWay)
- [ ] Reviewed quote and it's acceptable
- [ ] Confirmed all components are in stock
- [ ] Understand the timeline (2-4 weeks)
- [ ] Budget approved (~$150-250 for 5 boards)
- [ ] Have USB-C cable ready for testing
- [ ] Have firmware ready to flash

**Then click ORDER and wait for your pucks to arrive!** 🚀

---

## 📞 Next Steps

1. **Today:** Send message to freelancer (FREELANCER_REQUEST.md)
2. **Day 2-3:** Verify files when received
3. **Day 3:** Upload to JLCPCB and get quote
4. **Day 3:** Review quote and place order
5. **Week 2-3:** Wait for manufacturing & shipping
6. **Week 3:** Test your first puck!
7. **Week 4:** Celebrate or debug 🎉🐛

---

**You're so close to having real hardware!** The design is solid, firmware is tested, now just need to turn it into reality.

**Questions?** Come back anytime during the process and I'll help debug.

**Good luck!** 🍀
