austinscip/table-wars-puck/cad/assembled_top_view.png

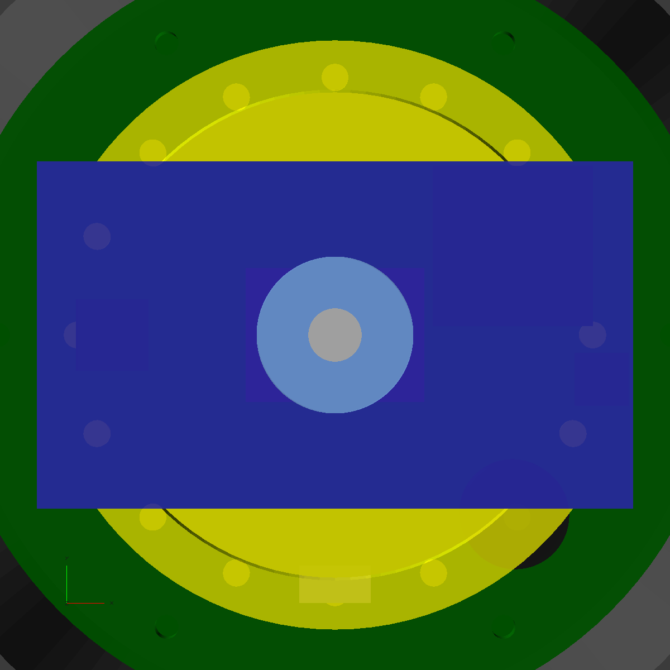
cad/assembled_top_view.png
