austinscip/table-wars-puck/cad/BUTTON_TEST_SIDE.png

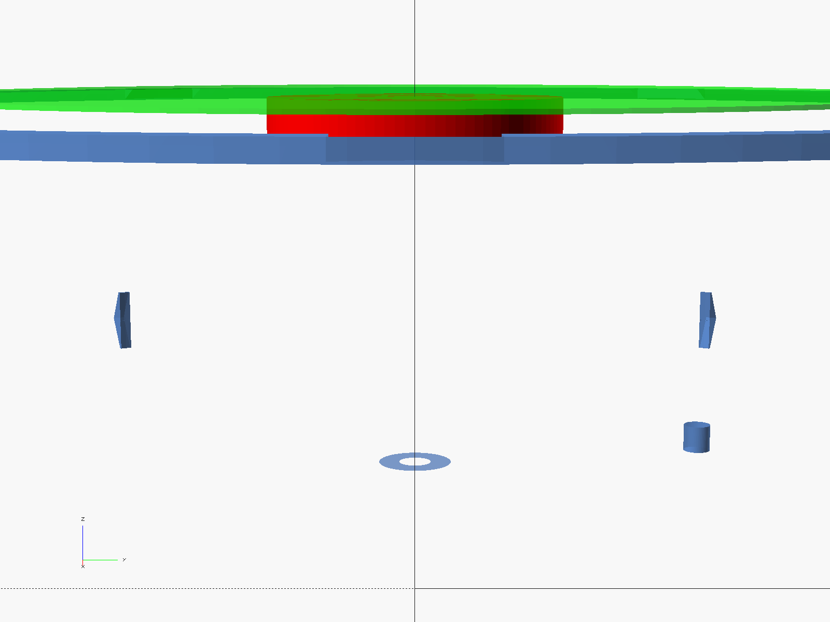
cad/BUTTON_TEST_SIDE.png
