austinscip/table-wars-puck/cad/BUTTON_TEST_z29.png

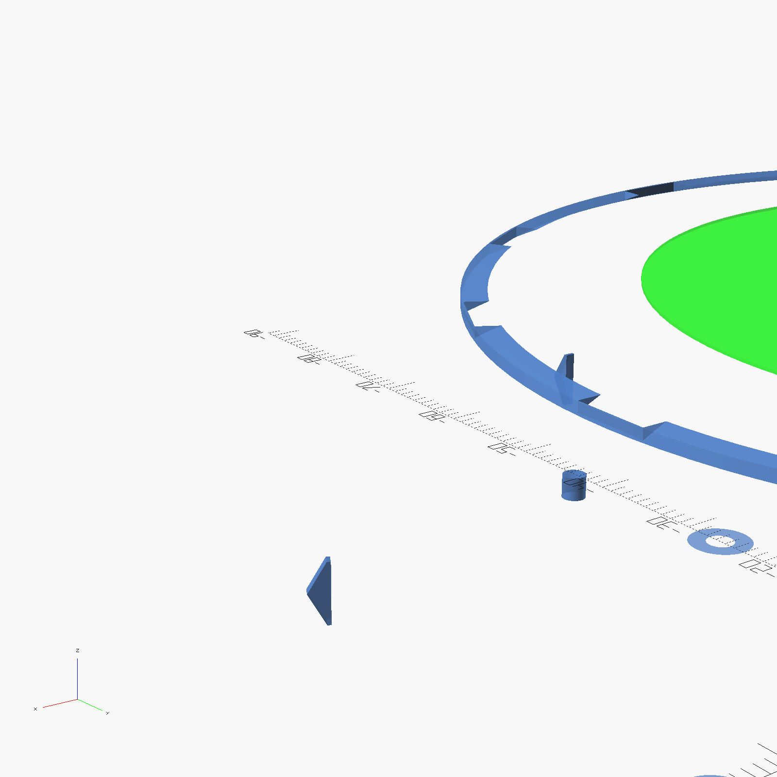
cad/BUTTON_TEST_z29.png
