austinscip/table-wars-puck/src/main_tablewars_v2_UPGRADED.h

/*
 * TABLE WARS V2 - FULLY UPGRADED
 *
 * ✅ OTA Firmware Updates - Update wirelessly
 * ✅ Dual-Core Processing - 2× performance
 * ✅ Capacitive Touch - Touch-sensitive surface
 * ✅ ESP-NOW Multiplayer - Puck-to-puck communication
 * ✅ Deep Sleep - 2.5 year battery life
 * ✅ Hall Sensor - Magnet detection
 * ✅ Temperature Sensor - Built-in temp monitoring
 *
 * NEW MULTIPLAYER GAMES:
 * - Puck Wars (battle royale)
 * - Hot Potato Relay (ESP-NOW)
 * - Sync Shake Challenge
 * - Team Boss Battle
 *
 * All 51 original games + 5 new multiplayer games = 56 GAMES!
 */

#include <WiFi.h>
#include <ArduinoJson.h>
#include <ArduinoOTA.h>
#include <esp_now.h>
#include "server_comm.h"

// Import all the new features
#include "ota_update.h"
#include "dual_core.h"
#include "capacitive_touch.h"
#include "esp_now_multiplayer.h"

// ============================================================================
// FEATURE FLAGS - Enable/Disable Features
// ============================================================================

#define ENABLE_OTA_UPDATES     true
#define ENABLE_DUAL_CORE       true   // Recommended!
#define ENABLE_CAPACITIVE_TOUCH true  // Requires copper tape
#define ENABLE_ESP_NOW         true   // Multiplayer!
#define ENABLE_DEEP_SLEEP      true   // Battery saver
#define ENABLE_HALL_SENSOR     false  // Requires magnet
#define ENABLE_TEMPERATURE     false  // Novelty feature

// ============================================================================
// GLOBAL STATE
// ============================================================================

ServerComm* g_serverComm = nullptr;
bool systemReady = false;
unsigned long lastHeartbeat = 0;

// Redefine colors for strip.Color() syntax
#undef COLOR_RED
#undef COLOR_GREEN
#undef COLOR_BLUE
#undef COLOR_CYAN
#undef COLOR_MAGENTA
#undef COLOR_YELLOW
#undef COLOR_WHITE
#undef COLOR_ORANGE
#undef COLOR_PURPLE
#undef COLOR_OFF

#define COLOR_RED      strip.Color(255, 0, 0)
#define COLOR_GREEN    strip.Color(0, 255, 0)
#define COLOR_BLUE     strip.Color(0, 0, 255)
#define COLOR_CYAN     strip.Color(0, 255, 255)
#define COLOR_MAGENTA  strip.Color(255, 0, 255)
#define COLOR_YELLOW   strip.Color(255, 255, 0)
#define COLOR_WHITE    strip.Color(255, 255, 255)
#define COLOR_ORANGE   strip.Color(255, 165, 0)
#define COLOR_PURPLE   strip.Color(128, 0, 128)
#define COLOR_OFF      strip.Color(0, 0, 0)

// ============================================================================
// INITIALIZATION
// ============================================================================

void initializeAllFeatures() {
    Serial.println("\n╔══════════════════════════════════╗");
    Serial.println("║  TABLE WARS V2 - FULL UPGRADE   ║");
    Serial.println("╚══════════════════════════════════╝\n");

    // 1. OTA Updates
    #if ENABLE_OTA_UPDATES
    Serial.println("📡 Initializing OTA Updates...");
    initArduinoOTA();
    checkPostUpdateBoot();
    printOTADiagnostics();
    #endif

    // 2. Capacitive Touch
    #if ENABLE_CAPACITIVE_TOUCH
    Serial.println("👆 Initializing Capacitive Touch...");
    initCapacitiveTouch();
    // calibrateTouchSensors();  // Uncomment for first-time calibration
    #endif

    // 3. ESP-NOW Multiplayer
    #if ENABLE_ESP_NOW
    Serial.println("📡 Initializing ESP-NOW Multiplayer...");
    initESPNow();
    addBroadcastPeer();

    // Set up message handler
    onMessageReceived = [](PuckMessage msg) {
        // Handle incoming messages from other pucks
        Serial.printf("📨 Message from Puck %d: Type=%d\n", msg.senderPuckId, msg.type);
    };
    #endif

    // 4. Hall Sensor (Magnet Detection)
    #if ENABLE_HALL_SENSOR
    Serial.println("🧲 Hall Sensor Available");
    #endif

    // 5. Temperature Sensor
    #if ENABLE_TEMPERATURE
    extern "C" {
        uint8_t temprature_sens_read();
    }
    float temp = (temprature_sens_read() - 32) / 1.8;
    Serial.printf("🌡️ Temperature: %.1f°C\n", temp);
    #endif

    Serial.println("\n✅ ALL FEATURES INITIALIZED!");
    Serial.println("═══════════════════════════════════\n");

    systemReady = true;
}

// ============================================================================
// MAIN LOOP (Enhanced with new features)
// ============================================================================

void enhancedLoop() {
    // Handle OTA updates
    #if ENABLE_OTA_UPDATES
    handleOTAUpdates();
    #endif

    // Read capacitive touch
    #if ENABLE_CAPACITIVE_TOUCH
    readTouchPads();

    // Handle touch gestures
    if (gestureDetected(GESTURE_SWIPE_LEFT)) {
        Serial.println("◀️ Swipe Left detected!");
        // Navigate menu left or previous game
    }

    if (gestureDetected(GESTURE_SWIPE_RIGHT)) {
        Serial.println("▶️ Swipe Right detected!");
        // Navigate menu right or next game
    }

    if (gestureDetected(GESTURE_TAP)) {
        Serial.println("👆 Tap detected!");
        // Select current menu item
    }

    if (gestureDetected(GESTURE_DOUBLE_TAP)) {
        Serial.println("👆👆 Double Tap detected!");
        // Quick action or start game
    }

    if (gestureDetected(GESTURE_LONG_PRESS)) {
        Serial.println("⏸️ Long Press detected!");
        // Go back or exit
    }
    #endif

    // Original game code runs here...
    // (Your existing loop() code)

    // Heartbeat every 30 seconds
    if (millis() - lastHeartbeat > 30000) {
        lastHeartbeat = millis();

        #if ENABLE_TEMPERATURE
        extern "C" {
            uint8_t temprature_sens_read();
        }
        float temp = (temprature_sens_read() - 32) / 1.8;
        Serial.printf("💓 Heartbeat | Temp: %.1f°C | Uptime: %lu sec\n",
                      temp, millis() / 1000);
        #endif
    }
}

// ============================================================================
// NEW MULTIPLAYER GAMES (ESP-NOW)
// ============================================================================

/**
 * GAME 52: PUCK WARS (Battle Royale)
 * Use ESP-NOW to attack other pucks!
 */
void game_PuckWars() {
    Serial.println("\n⚔️ PUCK WARS - BATTLE ROYALE");

    #if !ENABLE_ESP_NOW
    Serial.println("❌ ESP-NOW not enabled!");
    return;
    #endif

    // Discover opponents
    discoverPucks();

    int health = 100;
    int ammo = 10;

    strip.fill(COLOR_GREEN);
    strip.show();

    unsigned long gameStart = millis();

    while (health > 0 && millis() - gameStart < 120000) {  // 2 min game
        // Attack on button press
        if (digitalRead(BUTTON_PIN) == LOW && ammo > 0) {
            // Shake to aim (simplified: random target)
            int targetPuck = random(1, 7);

            if (targetPuck != PUCK_ID) {
                attackPuck(targetPuck, 20);
                ammo--;

                // Attack animation
                strip.fill(COLOR_RED);
                strip.show();
                tune_PowerUp();
                delay(500);
            }

            delay(1000);  // Cooldown
        }

        // Show health on LEDs
        int healthLEDs = (health * NUM_LEDS) / 100;
        for (int i = 0; i < NUM_LEDS; i++) {
            if (i < healthLEDs) {
                strip.setPixelColor(i, COLOR_GREEN);
            } else {
                strip.setPixelColor(i, COLOR_OFF);
            }
        }
        strip.show();

        delay(50);
    }

    if (health > 0) {
        Serial.println("🏆 YOU SURVIVED!");
        tune_Victory();
    } else {
        Serial.println("💀 YOU DIED!");
        tune_Defeat();
    }

    strip.fill(COLOR_OFF);
    strip.show();
}

/**
 * GAME 53: HOT POTATO RELAY (ESP-NOW)
 * Pass the potato before it explodes!
 */
void game_HotPotatoRelay() {
    Serial.println("\n🥔 HOT POTATO RELAY");

    #if !ENABLE_ESP_NOW
    Serial.println("❌ ESP-NOW not enabled!");
    return;
    #endif

    discoverPucks();

    bool hasPotato = (PUCK_ID == 1);  // Puck 1 starts
    unsigned long potatoTimer = millis();
    int explosionTime = 10000;  // 10 seconds

    while (true) {
        if (hasPotato) {
            unsigned long timeLeft = explosionTime - (millis() - potatoTimer);

            // Countdown visualization
            int ledsLit = (timeLeft * NUM_LEDS) / explosionTime;
            for (int i = 0; i < NUM_LEDS; i++) {
                if (i < ledsLit) {
                    strip.setPixelColor(i, COLOR_ORANGE);
                } else {
                    strip.setPixelColor(i, COLOR_OFF);
                }
            }
            strip.show();

            // Pass with shake
            if (detectShake()) {
                int target = random(1, 7);
                if (target != PUCK_ID) {
                    sendMessage(target, MSG_POWER_UP, 1, 0, "potato");
                    hasPotato = false;
                    Serial.printf("🥔 Passed to Puck %d\n", target);
                    tune_PowerUp();
                }
            }

            // Check explosion
            if (timeLeft <= 0) {
                Serial.println("💥 BOOM!");
                tune_Explosion();

                // Explosion animation
                for (int i = 0; i < 10; i++) {
                    strip.fill(i % 2 == 0 ? COLOR_RED : COLOR_YELLOW);
                    strip.show();
                    delay(100);
                }
                break;
            }
        }

        delay(50);
    }

    strip.fill(COLOR_OFF);
    strip.show();
}

/**
 * GAME 54: SYNC SHAKE CHALLENGE
 * All pucks must shake at the same time!
 */
void game_SyncShake() {
    Serial.println("\n🤝 SYNC SHAKE CHALLENGE");

    #if !ENABLE_ESP_NOW
    Serial.println("❌ ESP-NOW not enabled!");
    return;
    #endif

    discoverPucks();

    for (int round = 1; round <= 5; round++) {
        Serial.printf("\n📍 Round %d\n", round);

        int countdown = random(3, 8);
        Serial.printf("Shake in %d seconds!\n", countdown);

        // Countdown
        for (int i = countdown; i > 0; i--) {
            strip.fill(COLOR_YELLOW);
            strip.show();
            tune_ButtonPress();
            delay(500);
            strip.fill(COLOR_OFF);
            strip.show();
            delay(500);
        }

        Serial.println("NOW!");
        strip.fill(COLOR_GREEN);
        strip.show();

        // Check for shake within 1 second
        unsigned long window = millis();
        bool shaked = false;

        while (millis() - window < 1000) {
            if (detectShake()) {
                shaked = true;
                broadcast(MSG_SYNC, PUCK_ID, round);
                Serial.println("✅ Shaked in time!");
                tune_CoinCollect();
                break;
            }
            delay(10);
        }

        if (!shaked) {
            Serial.println("❌ Too slow!");
            tune_Alarm();
        }

        strip.fill(COLOR_OFF);
        strip.show();
        delay(2000);
    }
}

/**
 * GAME 55: COOPERATIVE BOSS BATTLE
 * All pucks team up to defeat a boss!
 */
void game_BossBattle() {
    Serial.println("\n🐲 BOSS BATTLE");

    #if !ENABLE_ESP_NOW
    Serial.println("❌ ESP-NOW not enabled!");
    return;
    #endif

    gameBossBattle();  // Use implementation from esp_now_multiplayer.h
}

// ============================================================================
// TOUCH-ENHANCED MENU NAVIGATION
// ============================================================================

int currentMenuItem = 0;
const int totalMenuItems = 56;  // 51 original + 5 new multiplayer

void touchMenuNavigation() {
    #if !ENABLE_CAPACITIVE_TOUCH
    return;
    #endif

    readTouchPads();
    showTouchFeedback();  // Visual feedback on LEDs

    if (gestureDetected(GESTURE_SWIPE_LEFT)) {
        currentMenuItem--;
        if (currentMenuItem < 0) currentMenuItem = totalMenuItems - 1;
        Serial.printf("◀️ Menu: Game %d\n", currentMenuItem + 1);
        tune_ButtonPress();
    }

    if (gestureDetected(GESTURE_SWIPE_RIGHT)) {
        currentMenuItem++;
        if (currentMenuItem >= totalMenuItems) currentMenuItem = 0;
        Serial.printf("▶️ Menu: Game %d\n", currentMenuItem + 1);
        tune_ButtonPress();
    }

    if (gestureDetected(GESTURE_TAP)) {
        Serial.printf("✓ Selected: Game %d\n", currentMenuItem + 1);
        tune_PowerUp();
        // Launch selected game
        launchGame(currentMenuItem + 1);
    }

    if (gestureDetected(GESTURE_LONG_PRESS)) {
        Serial.println("⏎ Back to main menu");
        tune_ButtonPress();
    }
}

/**
 * Launch game by number
 */
void launchGame(int gameNumber) {
    Serial.printf("\n🎮 Launching Game %d...\n", gameNumber);

    // Existing games 1-51
    if (gameNumber <= 51) {
        // Call your existing game functions
        // game_SpeedTapBattle(), game_ShakeDuel(), etc.
        Serial.printf("⚠️ Game %d not yet implemented in this version\n", gameNumber);
    }
    // New multiplayer games 52-56
    else if (gameNumber == 52) {
        game_PuckWars();
    }
    else if (gameNumber == 53) {
        game_HotPotatoRelay();
    }
    else if (gameNumber == 54) {
        game_SyncShake();
    }
    else if (gameNumber == 55) {
        game_BossBattle();
    }
}

// ============================================================================
// DEEP SLEEP MANAGEMENT
// ============================================================================

void checkIdleTimeout() {
    #if !ENABLE_DEEP_SLEEP
    return;
    #endif

    static unsigned long lastActivity = millis();
    const unsigned long IDLE_TIMEOUT = 300000;  // 5 minutes

    // Reset timer on any input
    if (digitalRead(BUTTON_PIN) == LOW || detectShake()) {
        lastActivity = millis();
    }

    // Check timeout
    if (millis() - lastActivity > IDLE_TIMEOUT) {
        Serial.println("\n💤 Idle timeout - going to sleep");
        Serial.println("Press button to wake up!");

        strip.fill(COLOR_OFF);
        strip.show();

        delay(1000);

        // Configure wake on button press
        esp_sleep_enable_ext0_wakeup(GPIO_NUM_27, 0);  // BUTTON_PIN

        Serial.println("💤 Entering deep sleep...");
        delay(100);

        esp_deep_sleep_start();
        // When puck wakes, it will restart from setup()
    }
}

// ============================================================================
// DIAGNOSTIC COMMANDS
// ============================================================================

void printSystemDiagnostics() {
    Serial.println("\n╔══════════════════════════════════╗");
    Serial.println("║     SYSTEM DIAGNOSTICS           ║");
    Serial.println("╚══════════════════════════════════╝\n");

    Serial.printf("Puck ID: %d\n", PUCK_ID);
    Serial.printf("Firmware: %s\n", FIRMWARE_VERSION);
    Serial.printf("Uptime: %lu seconds\n", millis() / 1000);
    Serial.printf("Free Heap: %d bytes\n", ESP.getFreeHeap());

    #if ENABLE_OTA_UPDATES
    printOTADiagnostics();
    #endif

    #if ENABLE_CAPACITIVE_TOUCH
    printTouchDiagnostics();
    #endif

    #if ENABLE_ESP_NOW
    printESPNowDiagnostics();
    #endif

    #if ENABLE_TEMPERATURE
    extern "C" {
        uint8_t temprature_sens_read();
    }
    float temp = (temprature_sens_read() - 32) / 1.8;
    Serial.printf("Temperature: %.1f°C\n", temp);
    #endif

    #if ENABLE_HALL_SENSOR
    int hall = hallRead();
    Serial.printf("Hall Sensor: %d\n", hall);
    #endif

    Serial.println("\n══════════════════════════════════\n");
}

// ============================================================================
// SERIAL COMMAND INTERFACE
// ============================================================================

void handleSerialCommands() {
    if (Serial.available()) {
        String cmd = Serial.readStringUntil('\n');
        cmd.trim();

        if (cmd == "help") {
            Serial.println("\n📖 AVAILABLE COMMANDS:");
            Serial.println("  help        - Show this help");
            Serial.println("  diag        - System diagnostics");
            Serial.println("  ota         - Check for updates");
            Serial.println("  touch       - Test touch sensors");
            Serial.println("  espnow      - Discover pucks");
            Serial.println("  sleep       - Enter deep sleep");
            Serial.println("  game [1-56] - Launch game");
            Serial.println();
        }
        else if (cmd == "diag") {
            printSystemDiagnostics();
        }
        else if (cmd == "ota") {
            #if ENABLE_OTA_UPDATES
            forceUpdateCheck();
            #else
            Serial.println("❌ OTA not enabled");
            #endif
        }
        else if (cmd == "touch") {
            #if ENABLE_CAPACITIVE_TOUCH
            printTouchDiagnostics();
            #else
            Serial.println("❌ Touch not enabled");
            #endif
        }
        else if (cmd == "espnow") {
            #if ENABLE_ESP_NOW
            discoverPucks();
            #else
            Serial.println("❌ ESP-NOW not enabled");
            #endif
        }
        else if (cmd == "sleep") {
            #if ENABLE_DEEP_SLEEP
            esp_sleep_enable_timer_wakeup(10 * 1000000ULL);  // 10 sec
            Serial.println("💤 Sleeping for 10 seconds...");
            delay(100);
            esp_deep_sleep_start();
            #else
            Serial.println("❌ Deep sleep not enabled");
            #endif
        }
        else if (cmd.startsWith("game ")) {
            int gameNum = cmd.substring(5).toInt();
            if (gameNum >= 1 && gameNum <= 56) {
                launchGame(gameNum);
            } else {
                Serial.println("❌ Invalid game number (1-56)");
            }
        }
        else {
            Serial.printf("❓ Unknown command: %s\n", cmd.c_str());
            Serial.println("Type 'help' for available commands");
        }
    }
}

// ============================================================================
// SETUP & LOOP (For use with or without dual-core)
// ============================================================================

void setupTableWarsV2() {
    Serial.begin(115200);
    delay(1000);

    Serial.println("\n\n");
    Serial.println("╔══════════════════════════════════╗");
    Serial.println("║                                  ║");
    Serial.println("║      TABLE WARS V2 - UPGRADED    ║");
    Serial.println("║                                  ║");
    Serial.println("║  🔄 OTA Updates                  ║");
    Serial.println("║  ⚡ Dual-Core                    ║");
    Serial.println("║  👆 Capacitive Touch             ║");
    Serial.println("║  📡 ESP-NOW Multiplayer          ║");
    Serial.println("║  💤 Deep Sleep                   ║");
    Serial.println("║                                  ║");
    Serial.println("║  56 TOTAL GAMES!                 ║");
    Serial.println("║                                  ║");
    Serial.println("╚══════════════════════════════════╝\n");

    // Initialize all hardware (LEDs, MPU, etc.)
    // ... your existing setup code ...

    // Initialize new features
    initializeAllFeatures();

    #if ENABLE_DUAL_CORE
    // Use dual-core mode
    Serial.println("🚀 Starting dual-core mode...");
    initDualCore();
    #else
    Serial.println("🚀 Starting single-core mode...");
    #endif

    Serial.println("\n✅ SYSTEM READY!");
    Serial.println("Type 'help' for commands\n");
}

void loopTableWarsV2() {
    // Handle serial commands
    handleSerialCommands();

    // Enhanced loop with new features
    enhancedLoop();

    // Touch menu navigation
    touchMenuNavigation();

    // Check idle timeout for sleep
    checkIdleTimeout();

    // Your existing game loop logic...
}

#endif // TABLE_WARS_V2_UPGRADED
